MKesenheimer/fault-injection-library/docs/images/multiplexing/gnd-1.8-1000ns.bmp

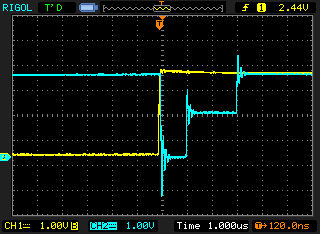
docs/images/multiplexing/gnd-1.8-1000ns.bmp
