MKesenheimer/fault-injection-library/docs/images/multiplexing/gnd-1.8.bmp

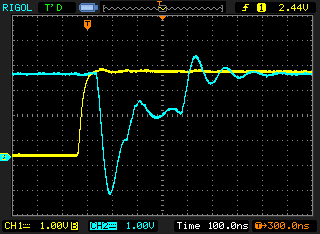
docs/images/multiplexing/gnd-1.8.bmp
