MKesenheimer/fault-injection-library/docs/images/multiplexing/gnd-3.3-gnd.bmp

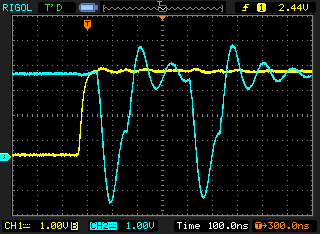
docs/images/multiplexing/gnd-3.3-gnd.bmp
