MKesenheimer/fault-injection-library/docs/images/pgfpv2.1.jpg

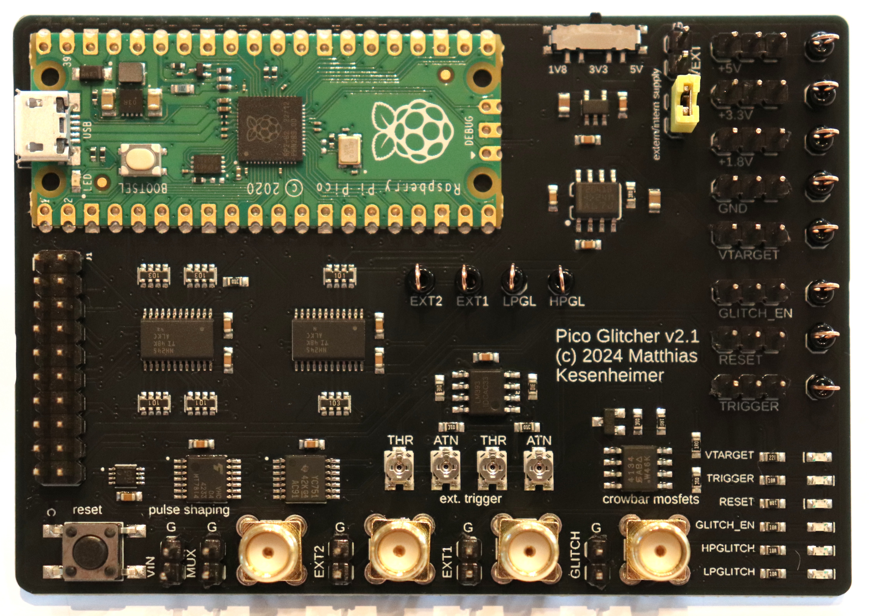
docs/images/pgfpv2.1.jpg
