MKesenheimer/fault-injection-library/docs/images/pinout.png

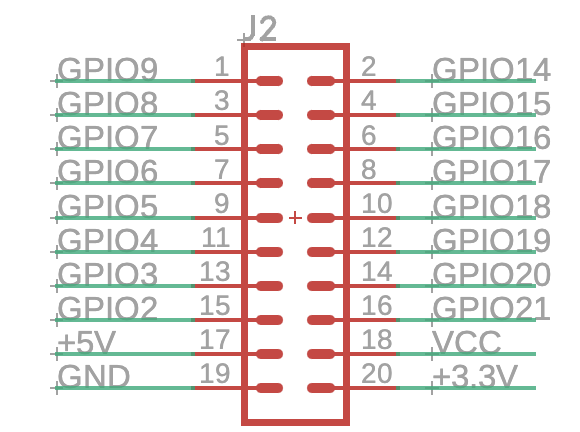
docs/images/pinout.png
