MKesenheimer/fault-injection-library/docs/images/pulse-shaping/4-100ns.bmp

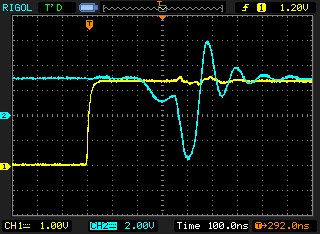
docs/images/pulse-shaping/4-100ns.bmp
