MKesenheimer/fault-injection-library/docs/images/pulse-shaping/4-1000ns.bmp

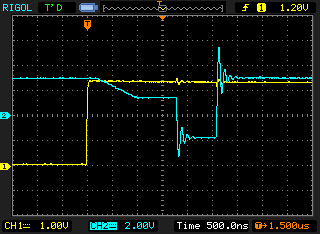
docs/images/pulse-shaping/4-1000ns.bmp
