MKesenheimer/fault-injection-library/docs/images/pulse-shaping/pchip-editor.bmp

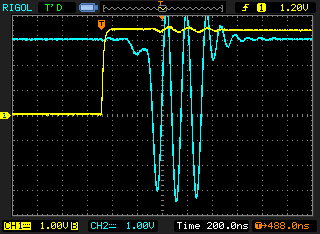
docs/images/pulse-shaping/pchip-editor.bmp
