MKesenheimer/fault-injection-library/docs/images/pulse-shaping/pchip-editor.png

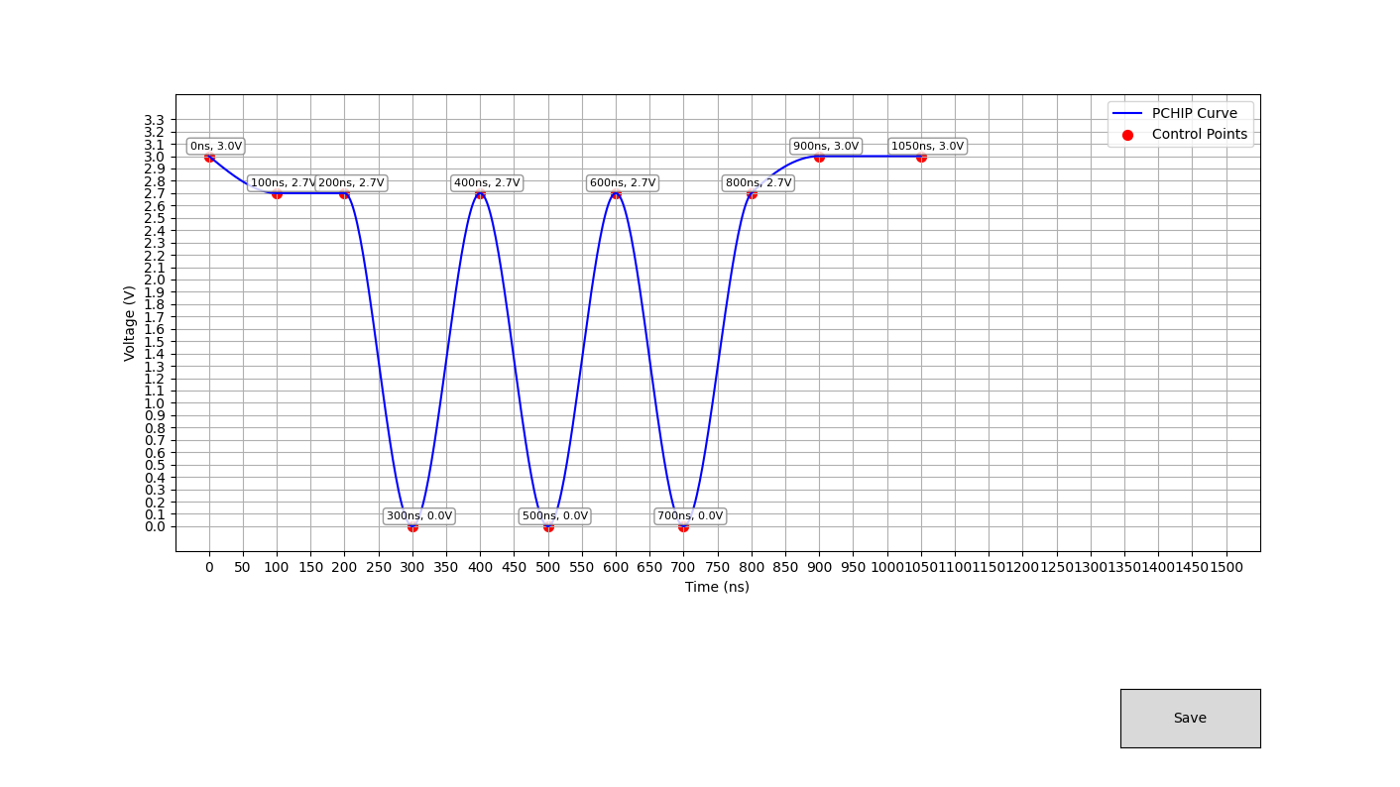
docs/images/pulse-shaping/pchip-editor.png
