MKesenheimer/fault-injection-library/docs/images/pulse-shaping/ps-100n-2.bmp

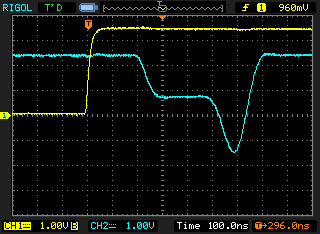
docs/images/pulse-shaping/ps-100n-2.bmp
