MKesenheimer/fault-injection-library/docs/images/pulse-shaping/ps-200n-2.bmp

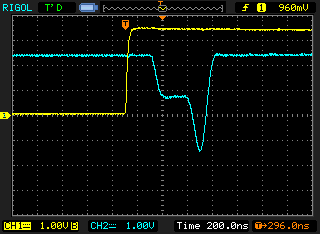
docs/images/pulse-shaping/ps-200n-2.bmp
