MKesenheimer/fault-injection-library/docs/images/stm8s/multiplexing-success.png

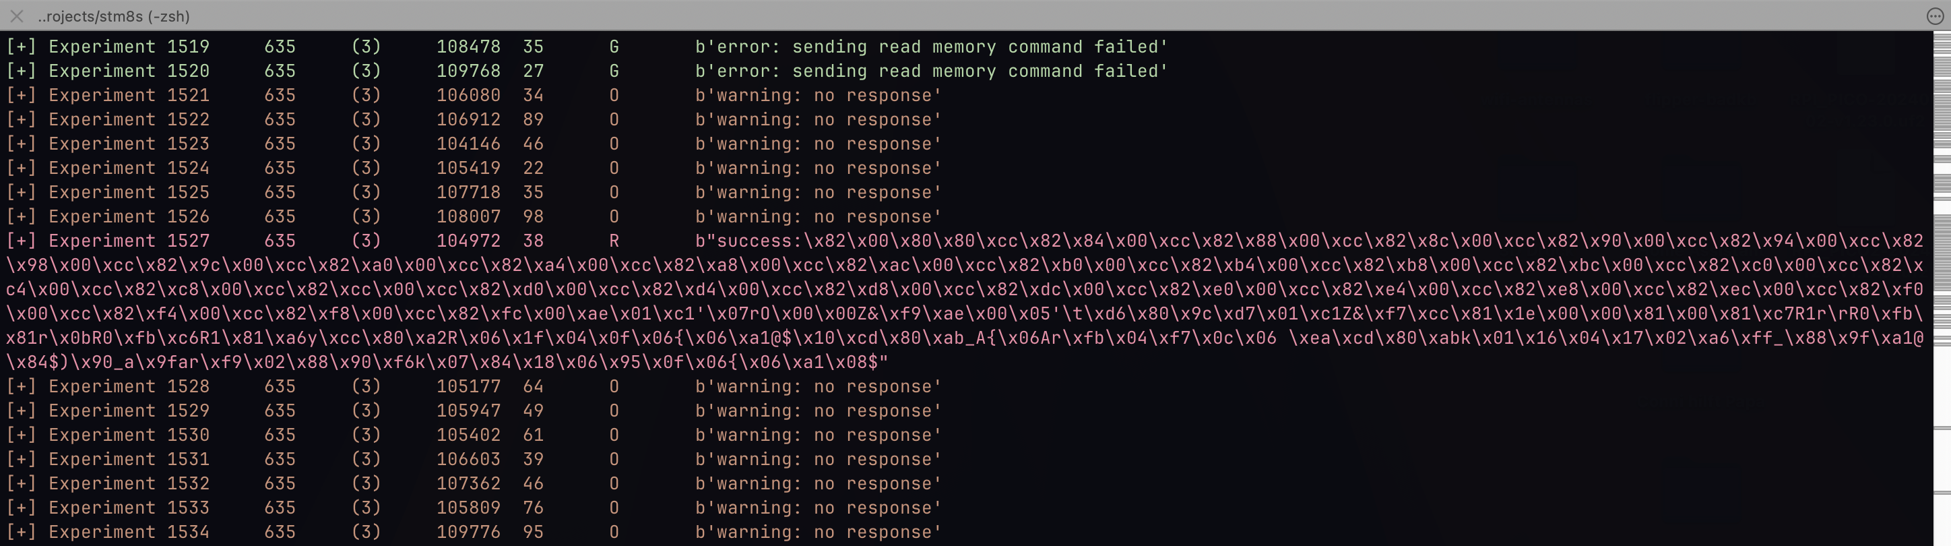
docs/images/stm8s/multiplexing-success.png
