MKesenheimer/fault-injection-library/projects/esp32v1.3/images/esp32-glitching.png

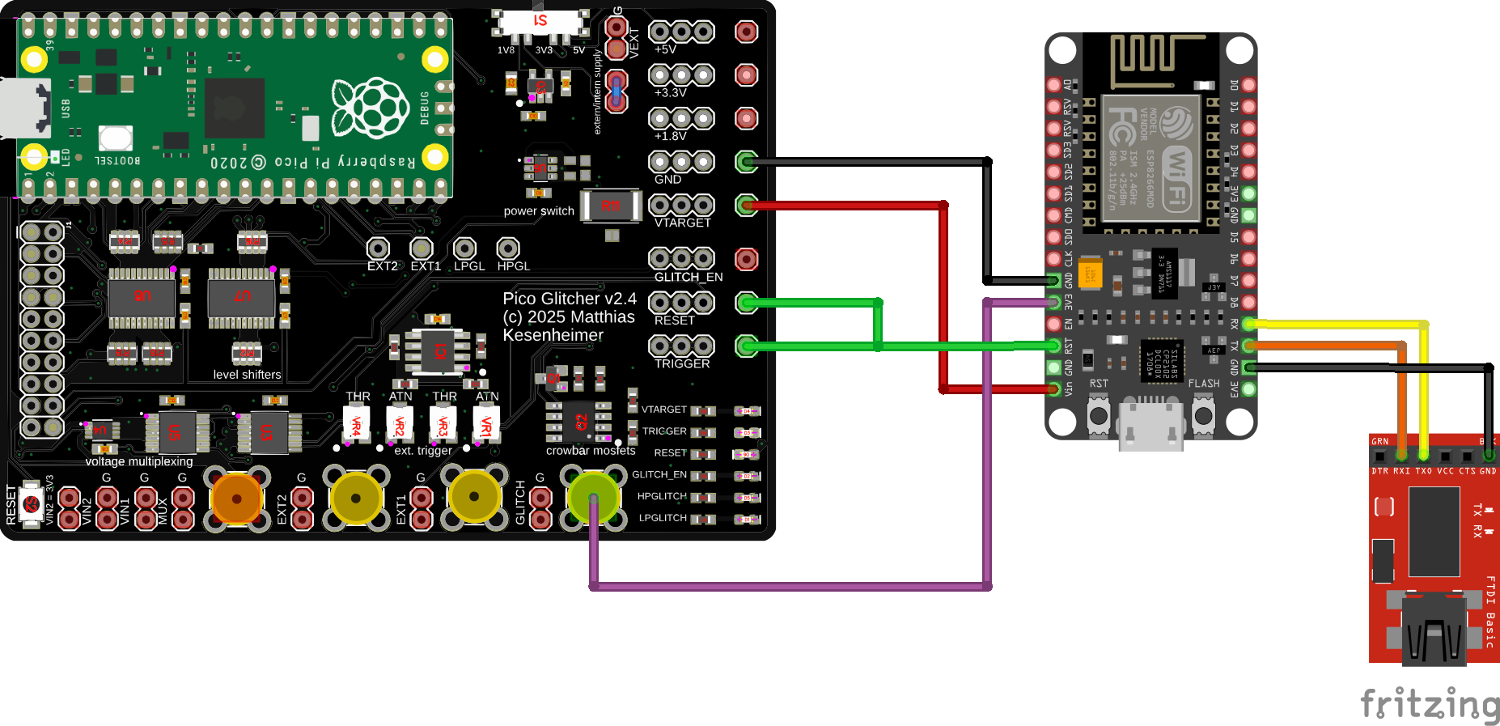
projects/esp32v1.3/images/esp32-glitching.png
