MKesenheimer/fault-injection-library/projects/esp32v1.3/images/multiplexing-t1_500ns-v1_1.8V-t2_variable-v2_GND.png

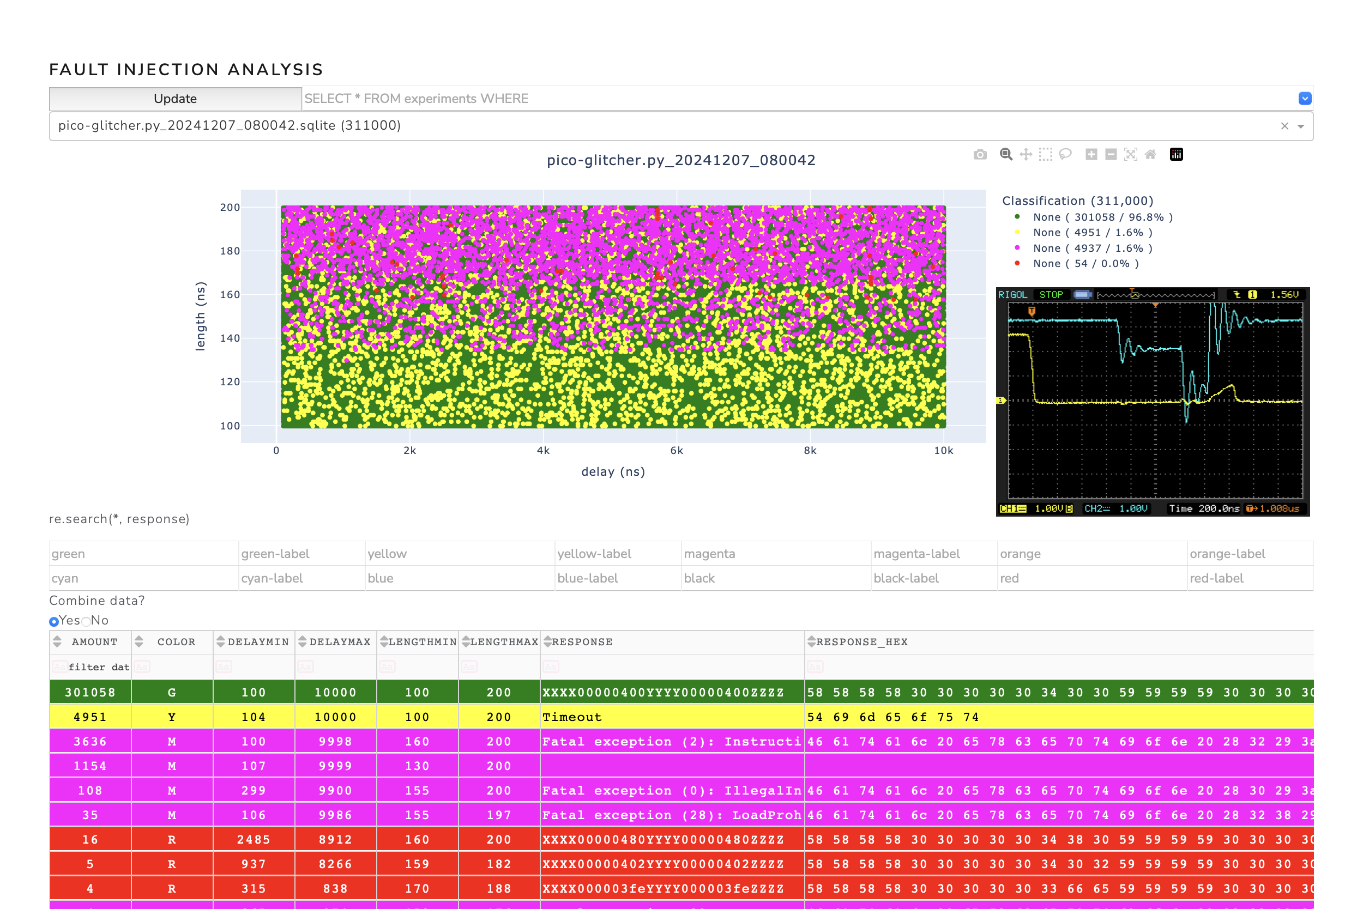
projects/esp32v1.3/images/multiplexing-t1_500ns-v1_1.8V-t2_variable-v2_GND.png
