MKesenheimer/fault-injection-library/projects/esp32v1.3/images/multiplexing-t1_1000ns-v1_1.8V-t2_variable-v2_GND-2.bmp

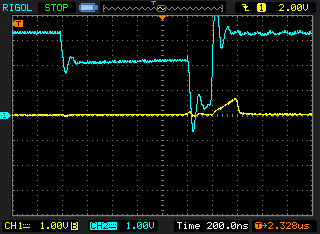
projects/esp32v1.3/images/multiplexing-t1_1000ns-v1_1.8V-t2_variable-v2_GND-2.bmp
