MKesenheimer/fault-injection-library/projects/esp32v1.3/images/multiplexing-t1_variable-v1_1.8V-t2_175ns-v2_GND.bmp

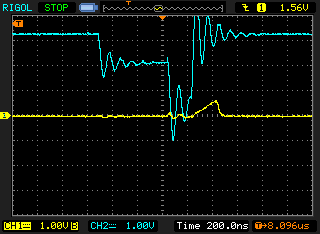
projects/esp32v1.3/images/multiplexing-t1_variable-v1_1.8V-t2_175ns-v2_GND.bmp
