MKesenheimer/fault-injection-library/projects/nrf52832/images/airtag/command-line-pro-glitcher.png

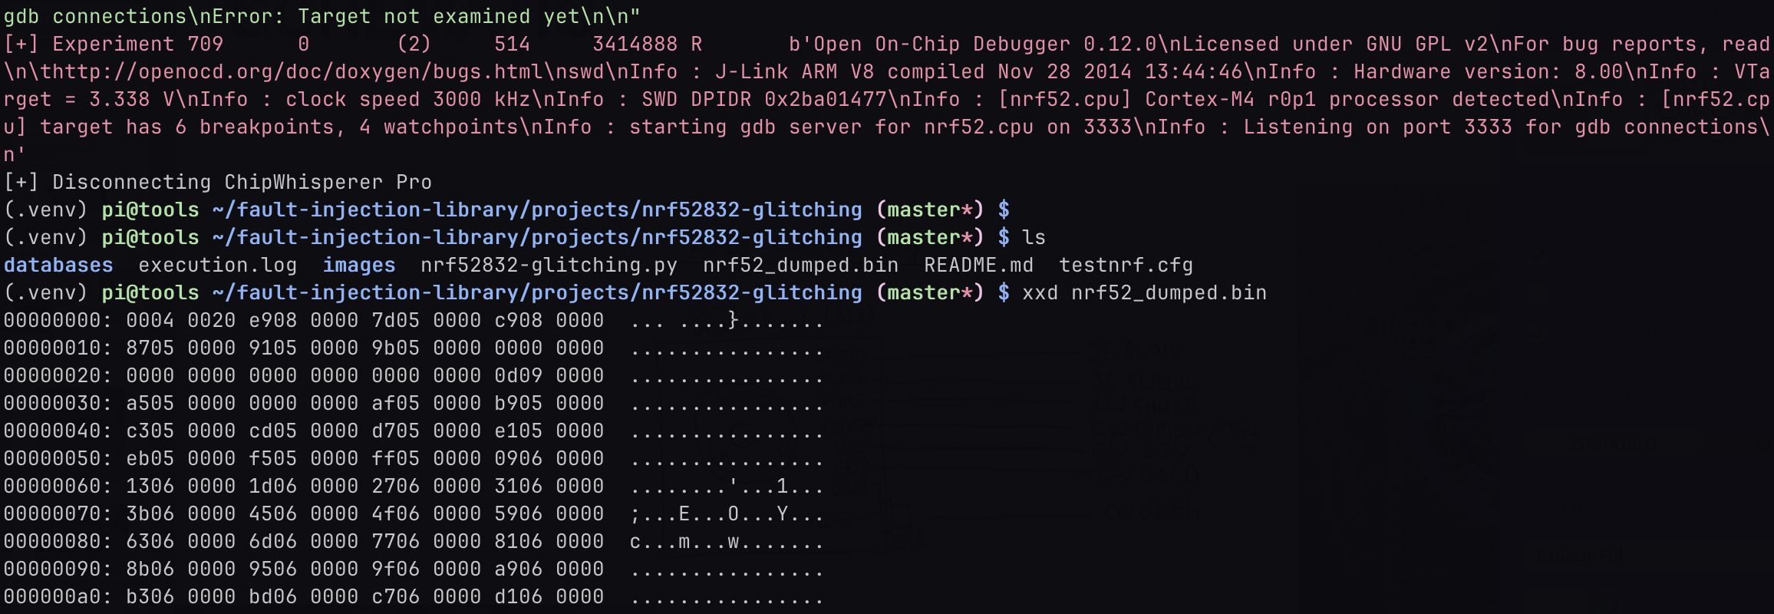
projects/nrf52832/images/airtag/command-line-pro-glitcher.png
