MKesenheimer/fault-injection-library/projects/nrf52832/images/airtag/glitch-2.png

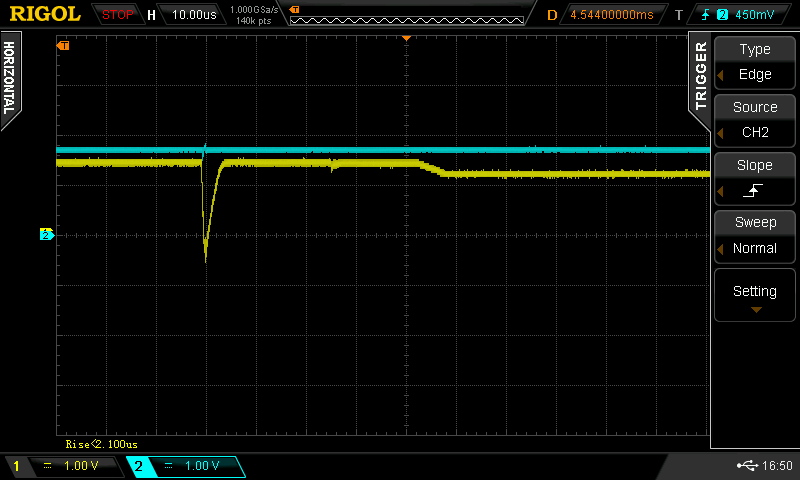
projects/nrf52832/images/airtag/glitch-2.png
