MKesenheimer/fault-injection-library/projects/nrf52832/images/airtag/parameterspace-pro-glitcher.png

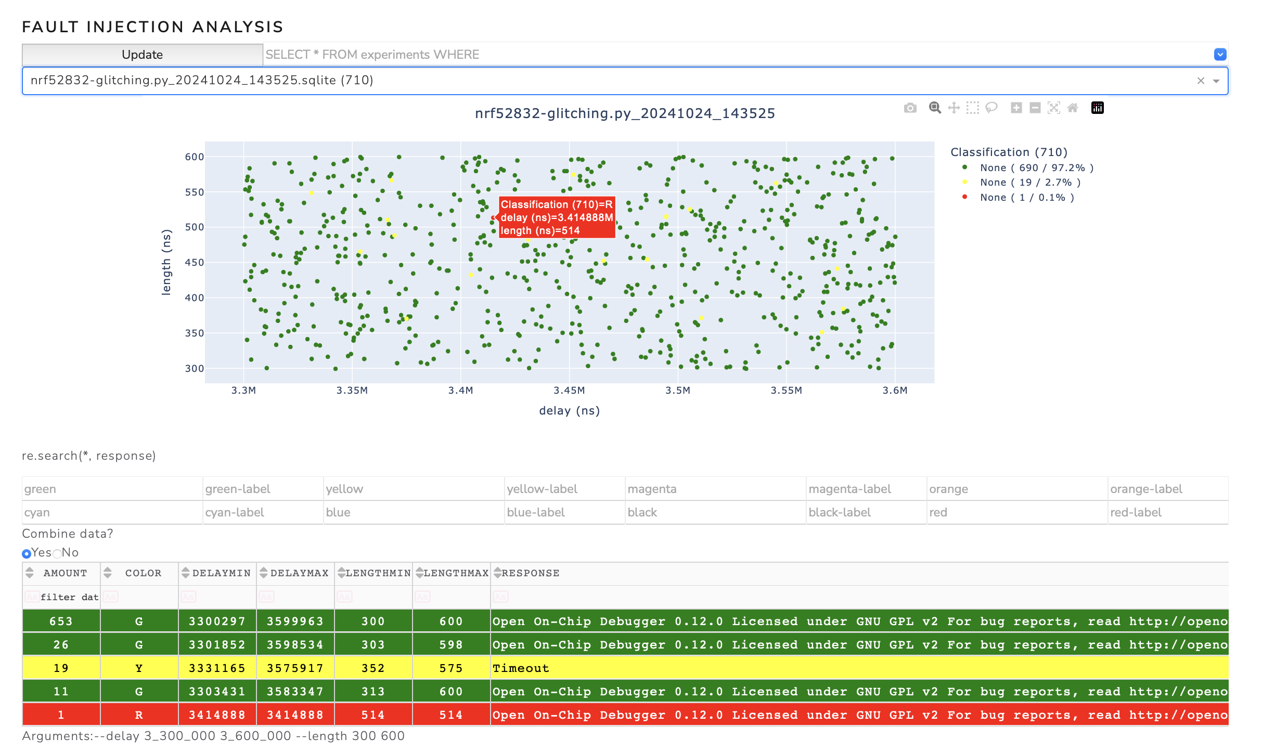
projects/nrf52832/images/airtag/parameterspace-pro-glitcher.png
