MKesenheimer/fault-injection-library/projects/nrf52832/images/airtag/voltage-trace-zoomed.png

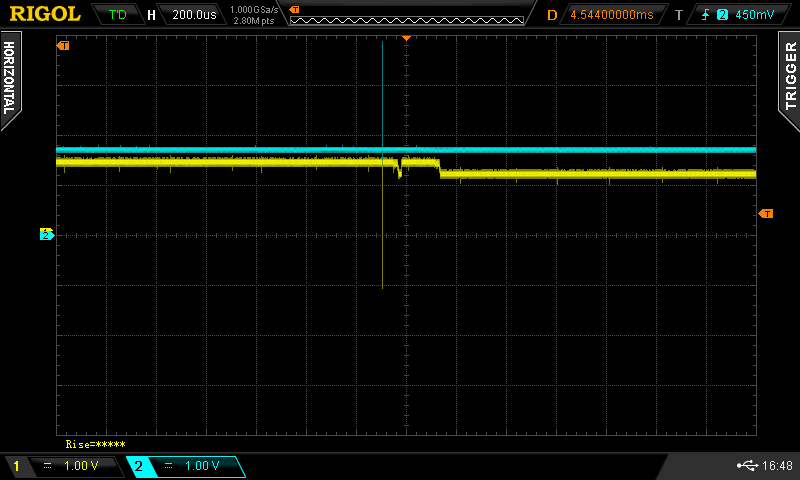
projects/nrf52832/images/airtag/voltage-trace-zoomed.png
