MKesenheimer/fault-injection-library/projects/nrf52832/images/keyboard/campaign-1.png

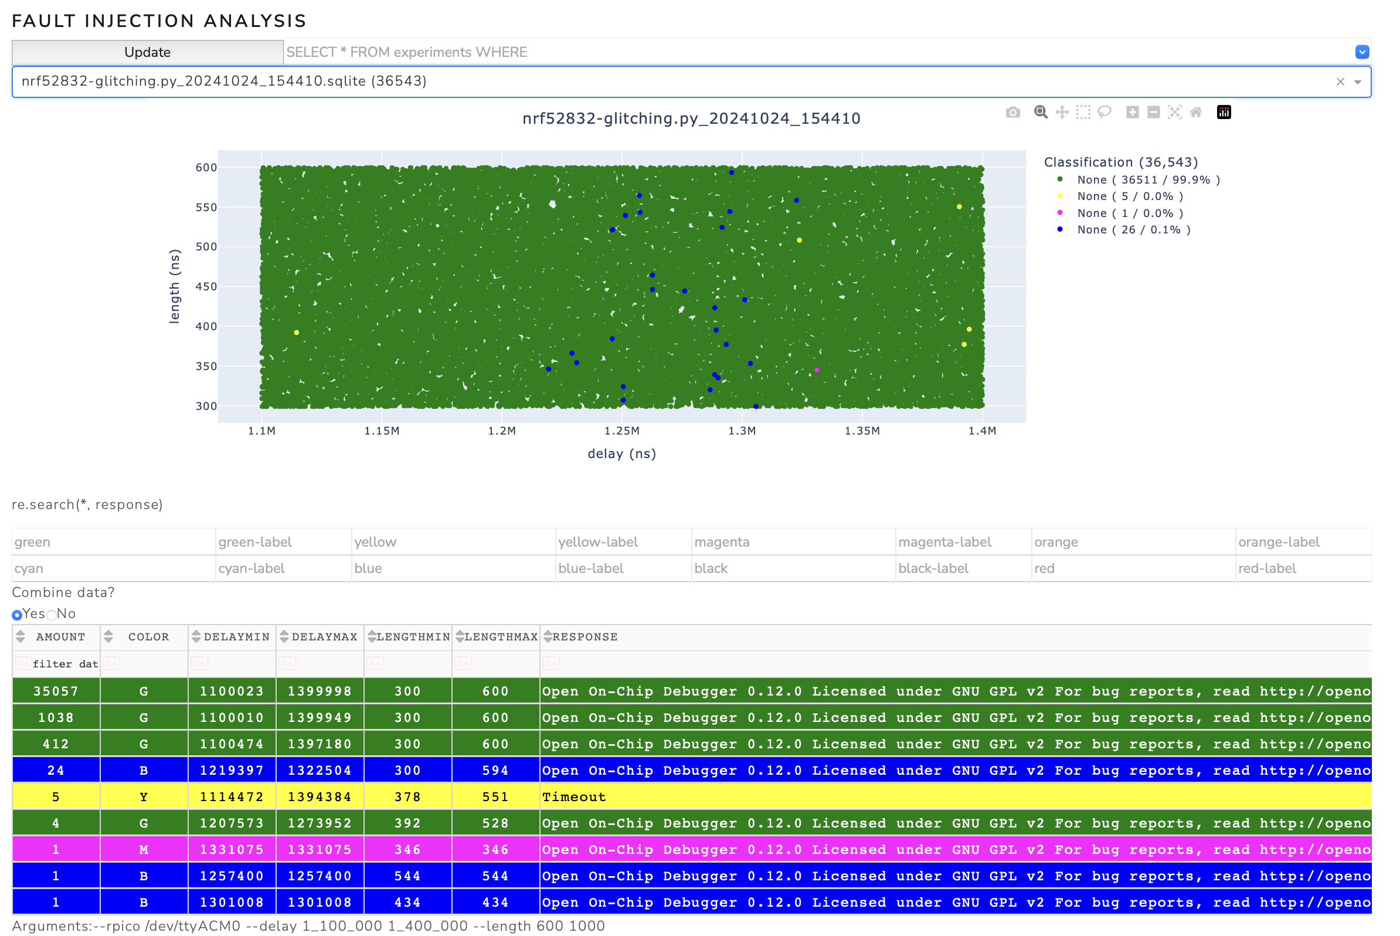
projects/nrf52832/images/keyboard/campaign-1.png
