MKesenheimer/fault-injection-library/projects/nrf52832/images/keyboard/campaign-2.png

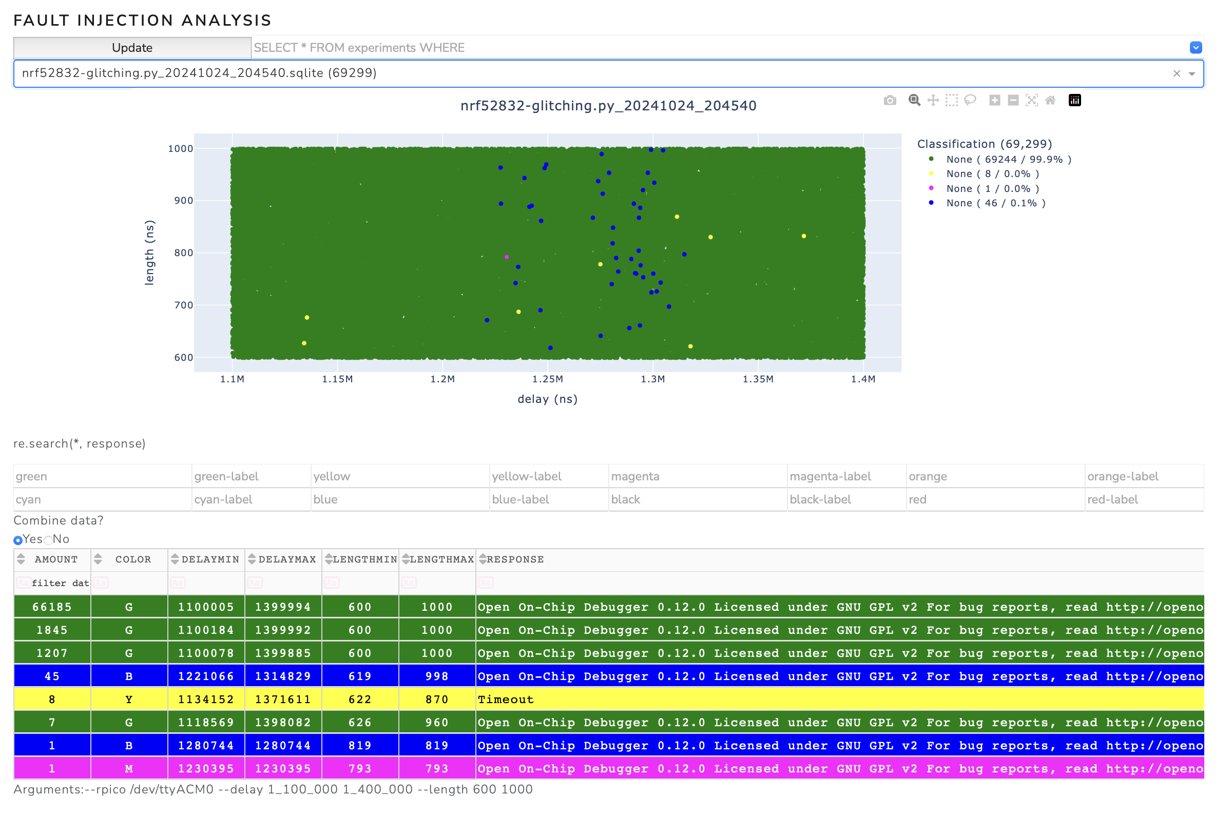
projects/nrf52832/images/keyboard/campaign-2.png
