MKesenheimer/fault-injection-library/projects/nrf52832/images/keyboard/glitch-zoomed.png

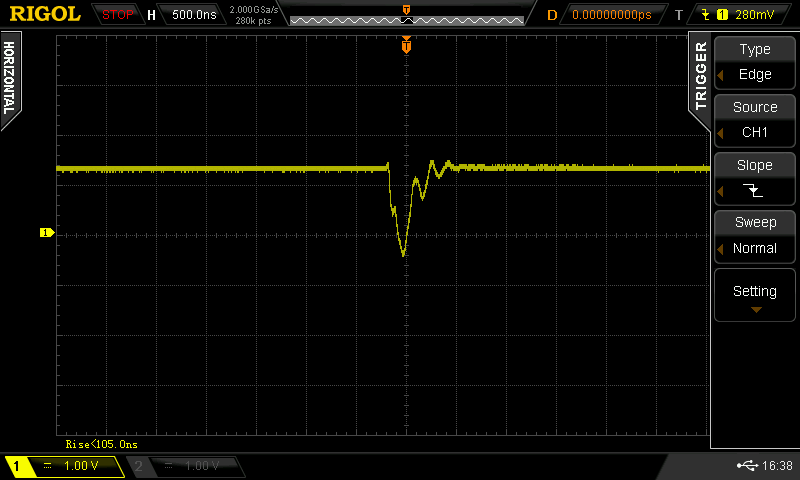
projects/nrf52832/images/keyboard/glitch-zoomed.png
