MKesenheimer/fault-injection-library/projects/nrf52832/images/keyboard/glitch.png

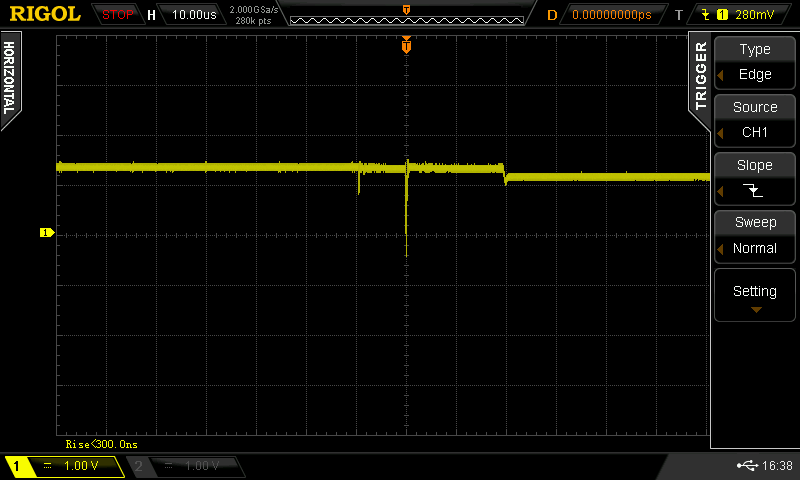
projects/nrf52832/images/keyboard/glitch.png
