MKesenheimer/fault-injection-library/projects/nrf52832/images/keyboard/gpio15_signal.png

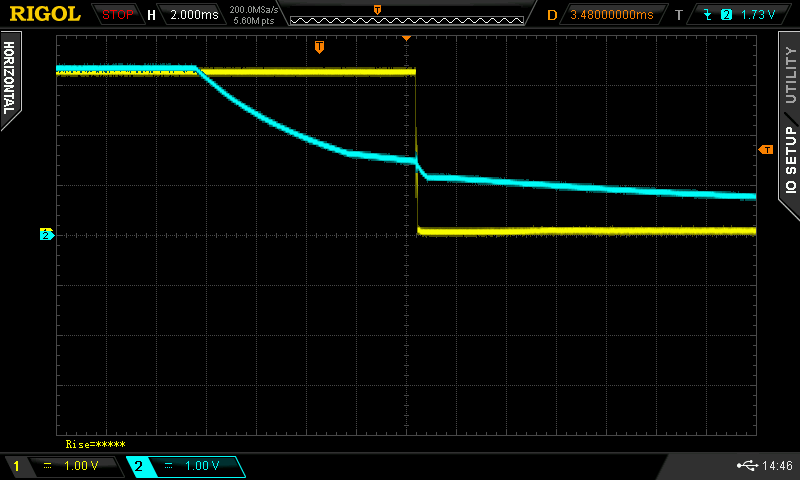
projects/nrf52832/images/keyboard/gpio15_signal.png
