MKesenheimer/fault-injection-library/projects/nrf52832/images/keyboard/gpio15_signal_zoomed.png

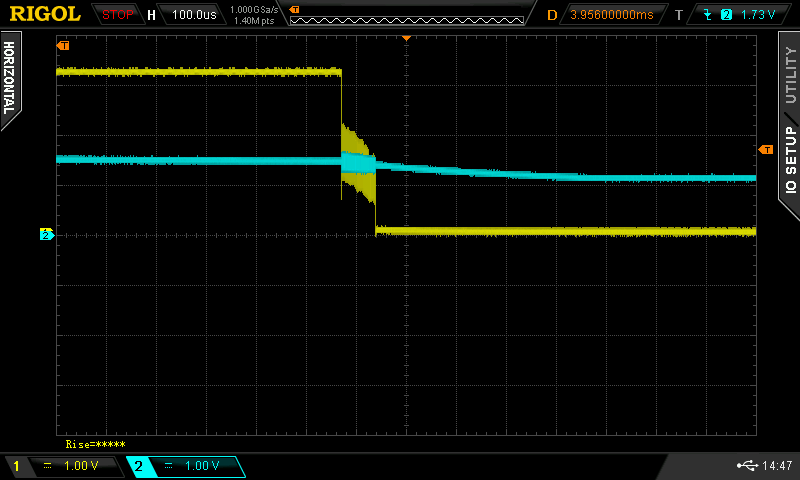
projects/nrf52832/images/keyboard/gpio15_signal_zoomed.png
