MKesenheimer/fault-injection-library/projects/nrf52832/images/keyboard/power-curve.png

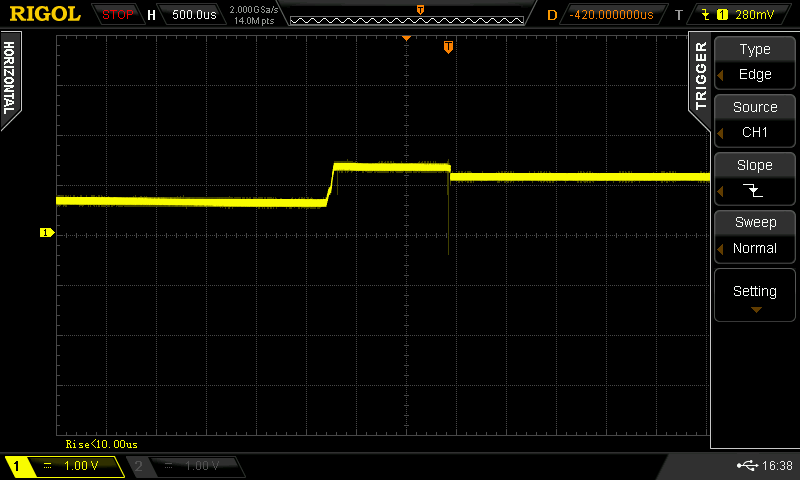
projects/nrf52832/images/keyboard/power-curve.png
