MKesenheimer/fault-injection-library/projects/rp2040/images/no-glitch.png

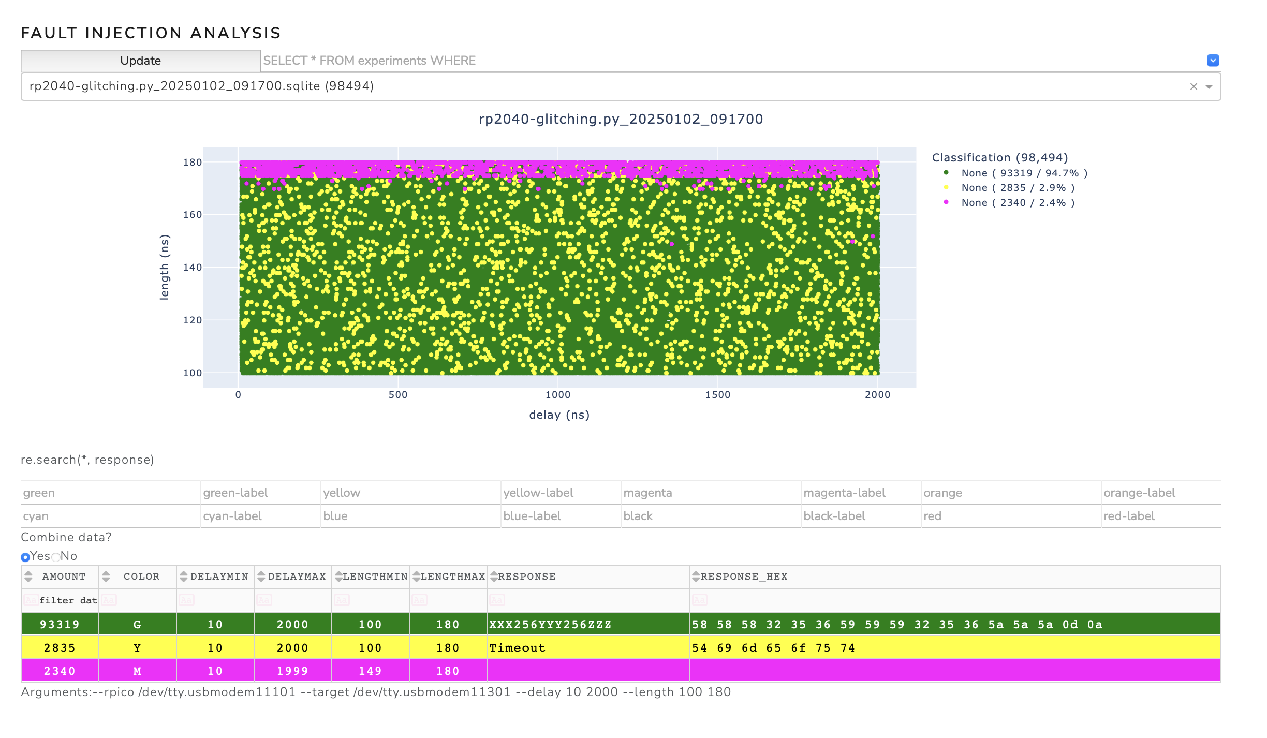
projects/rp2040/images/no-glitch.png
