MKesenheimer/fault-injection-library/projects/rp2040/rpi-program/raspberry-pi-pico-gpio.png

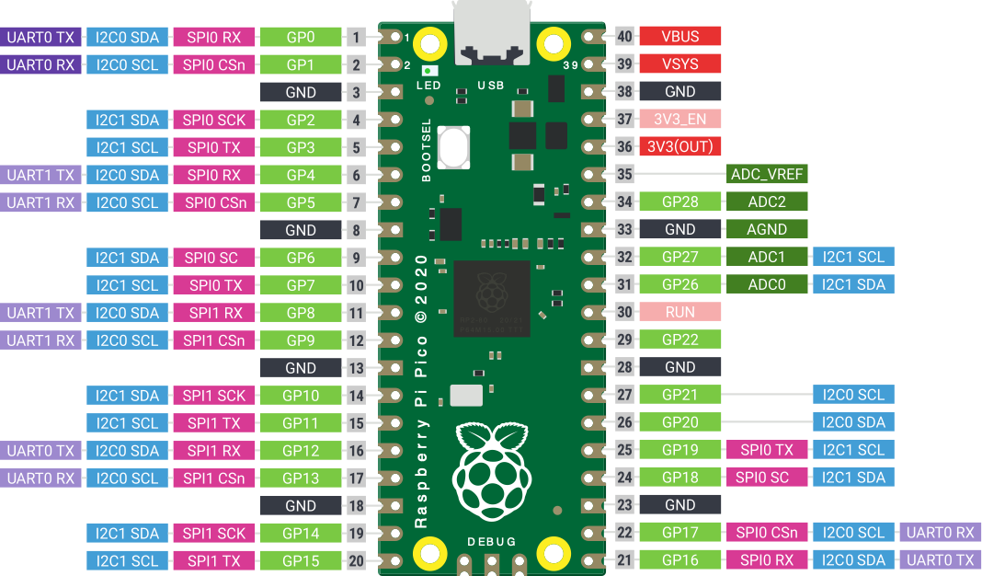
projects/rp2040/rpi-program/raspberry-pi-pico-gpio.png
