MKesenheimer/fault-injection-library/projects/rp2350/images/current-trace.bmp

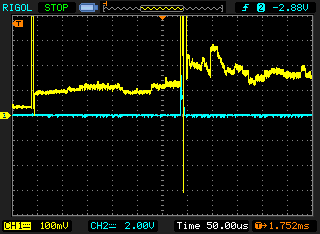
projects/rp2350/images/current-trace.bmp
