MKesenheimer/fault-injection-library/projects/rp2350/images/glitch1.bmp

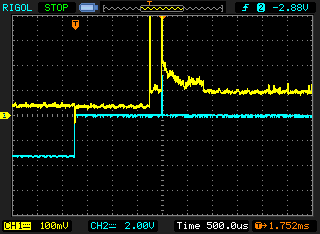
projects/rp2350/images/glitch1.bmp
