MKesenheimer/fault-injection-library/projects/rp2350/images/glitch2.bmp

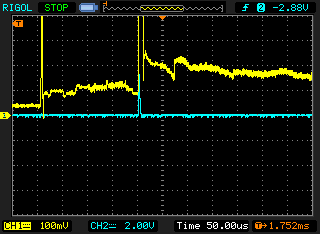
projects/rp2350/images/glitch2.bmp
