MKesenheimer/fault-injection-library/projects/rp2350/images/glitch3.bmp

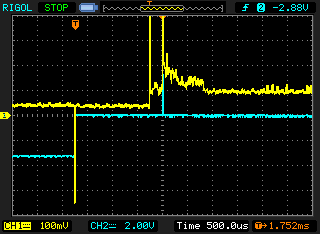
projects/rp2350/images/glitch3.bmp
