MKesenheimer/fault-injection-library/projects/rp2350/images/overall.JPG

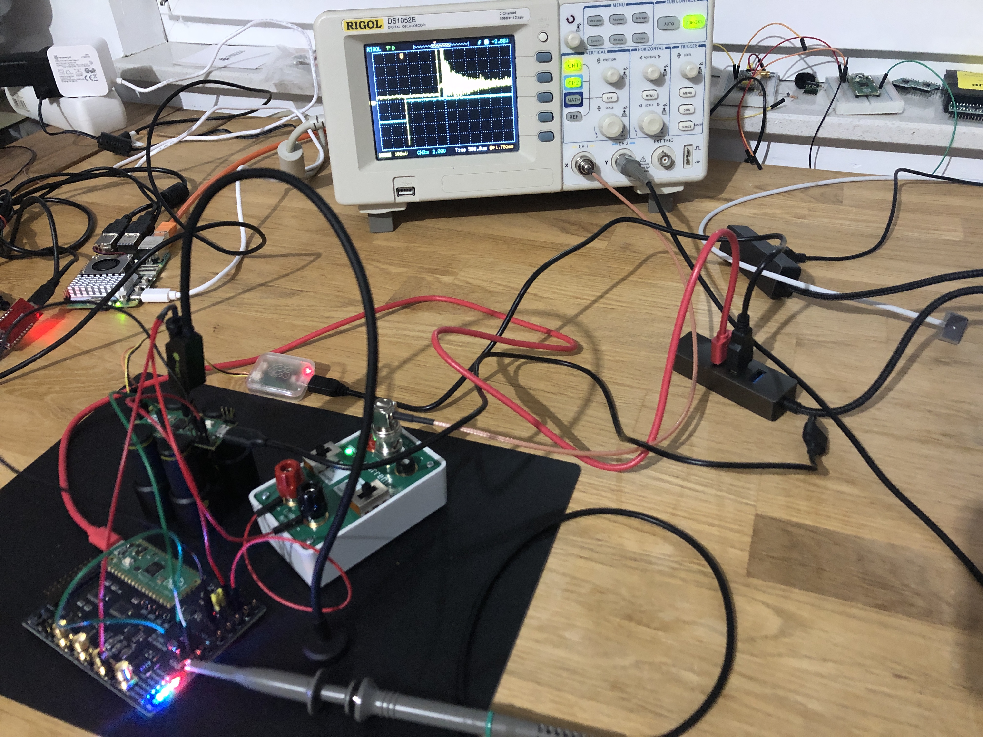
projects/rp2350/images/overall.JPG
