MKesenheimer/fault-injection-library/projects/rp2350/images/parameterspace1.png

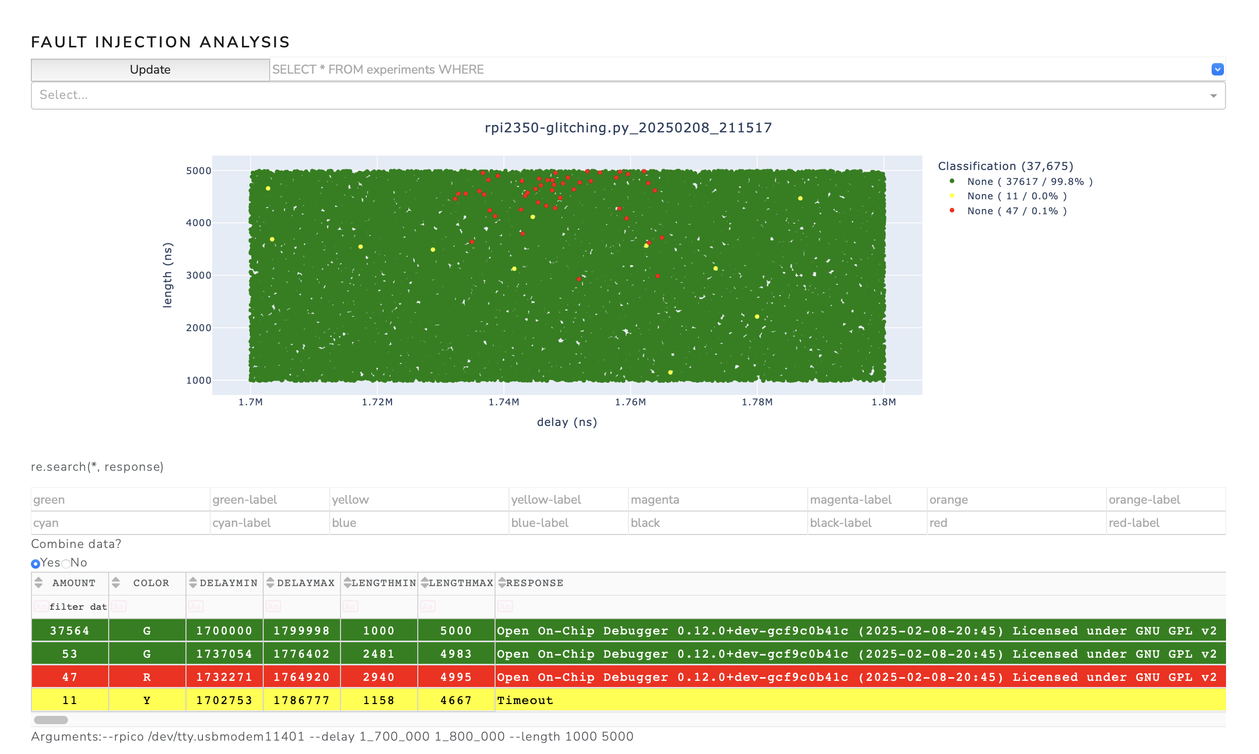
projects/rp2350/images/parameterspace1.png
