MKesenheimer/fault-injection-library/projects/rp2350/images/parameterspace2.png

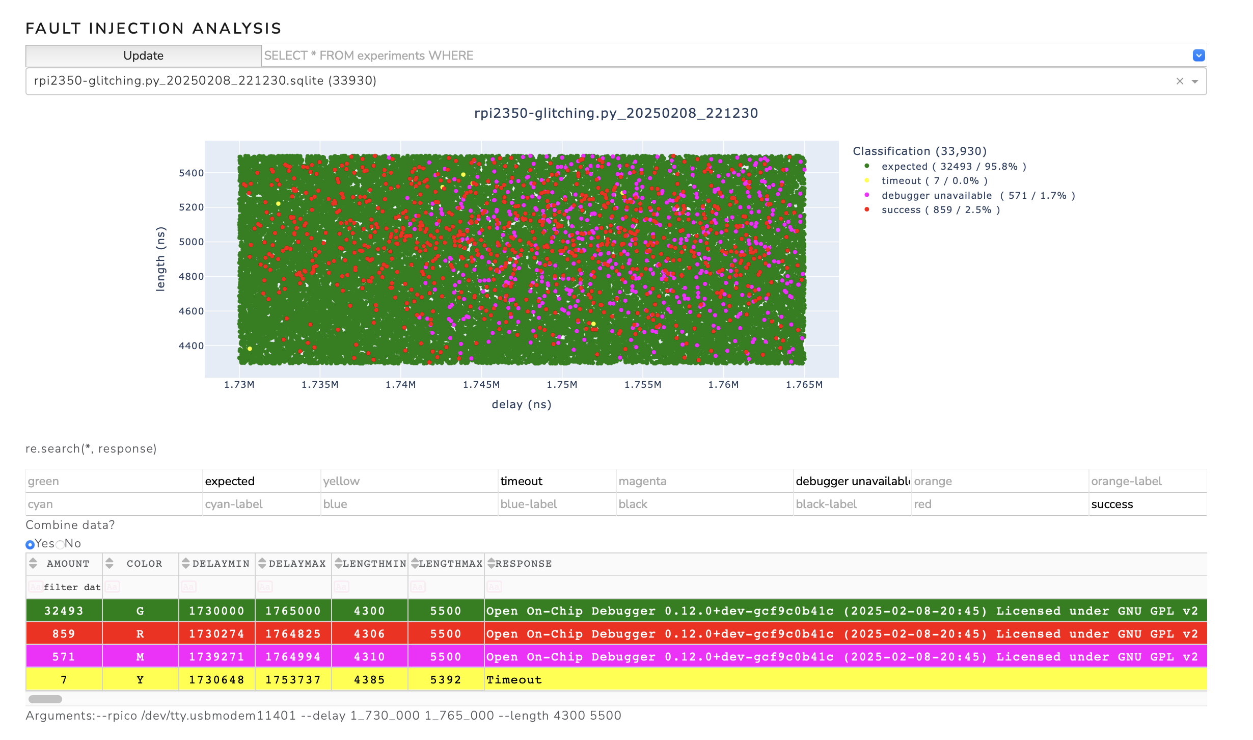
projects/rp2350/images/parameterspace2.png
