MKesenheimer/fault-injection-library/projects/rp2350/images/rp2350-glitching.png

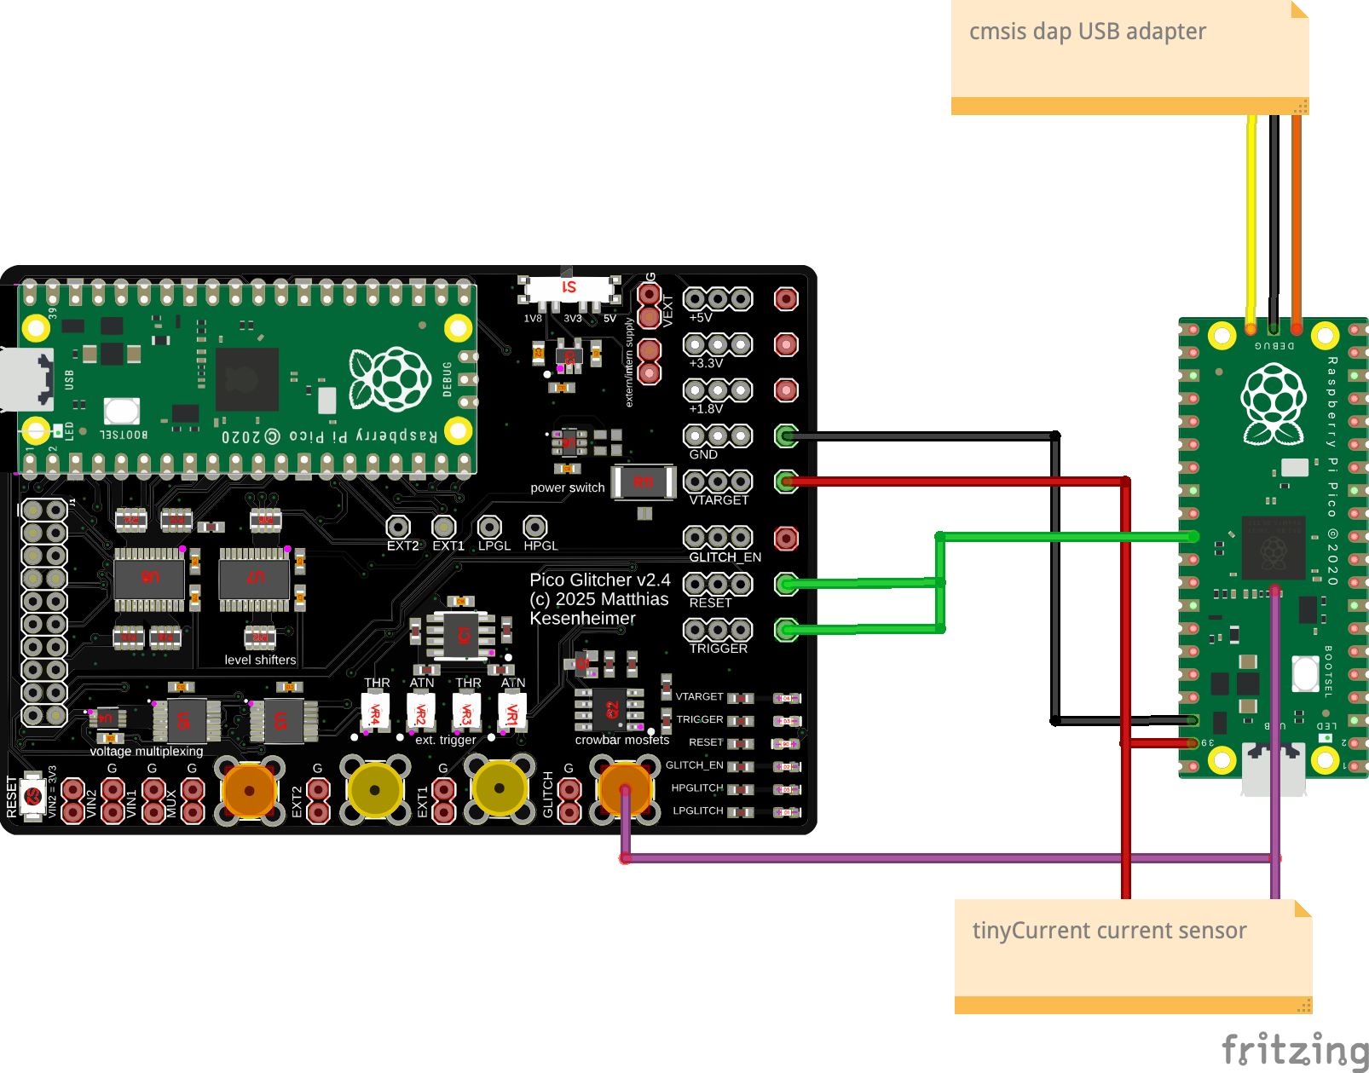
projects/rp2350/images/rp2350-glitching.png
