MKesenheimer/fault-injection-library/projects/rp2350/images/success.png

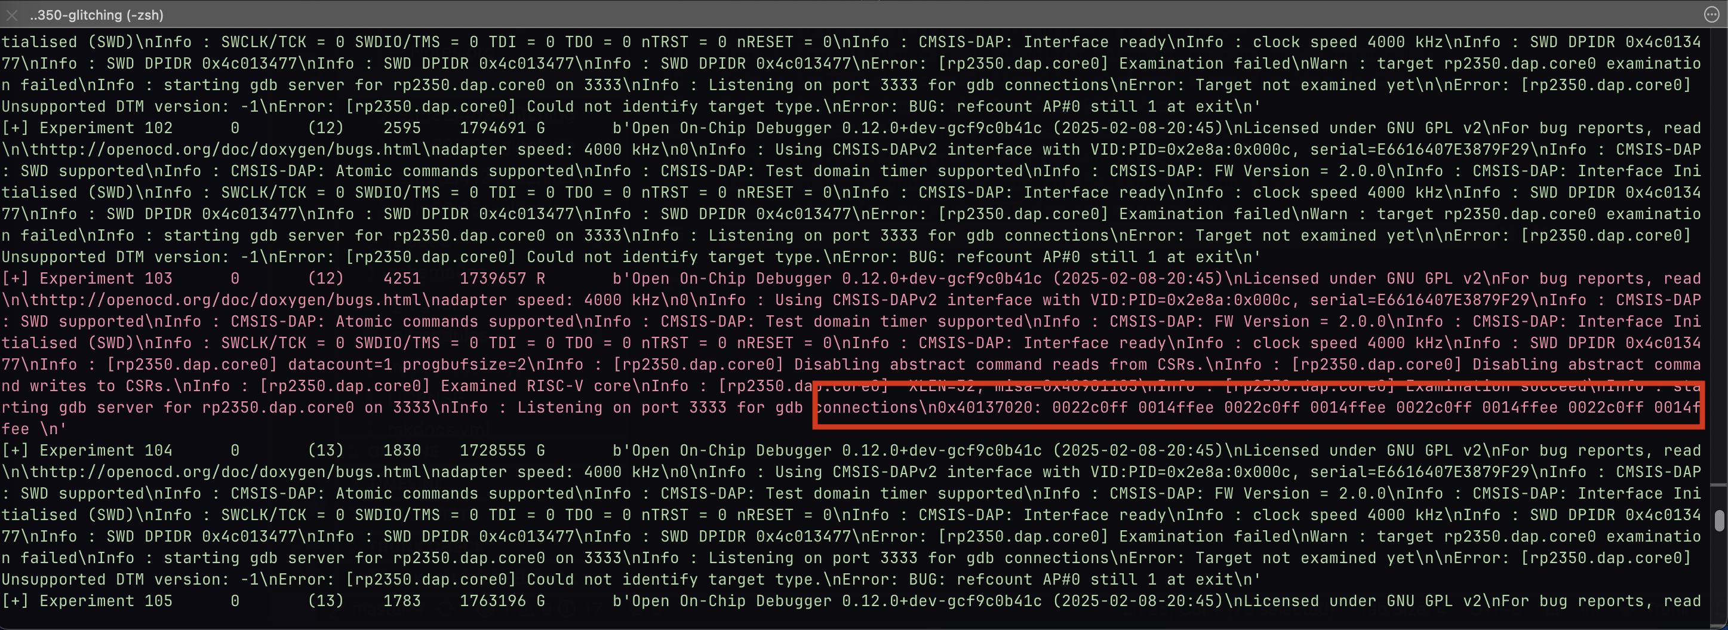
projects/rp2350/images/success.png
