MKesenheimer/fault-injection-library/projects/stm8s/images/bootloader-communication-1.png

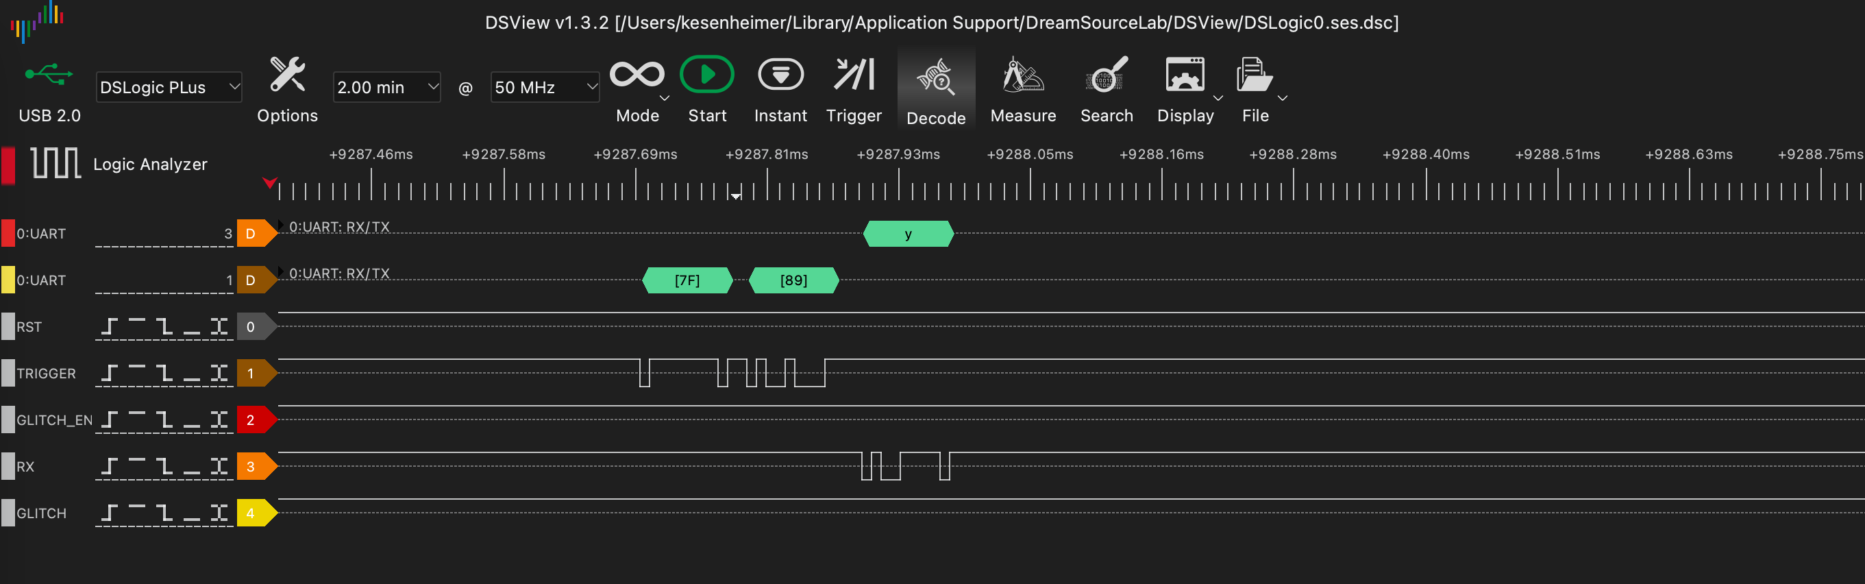
projects/stm8s/images/bootloader-communication-1.png
