MKesenheimer/fault-injection-library/projects/stm8s/images/bootloader-communication-2.png

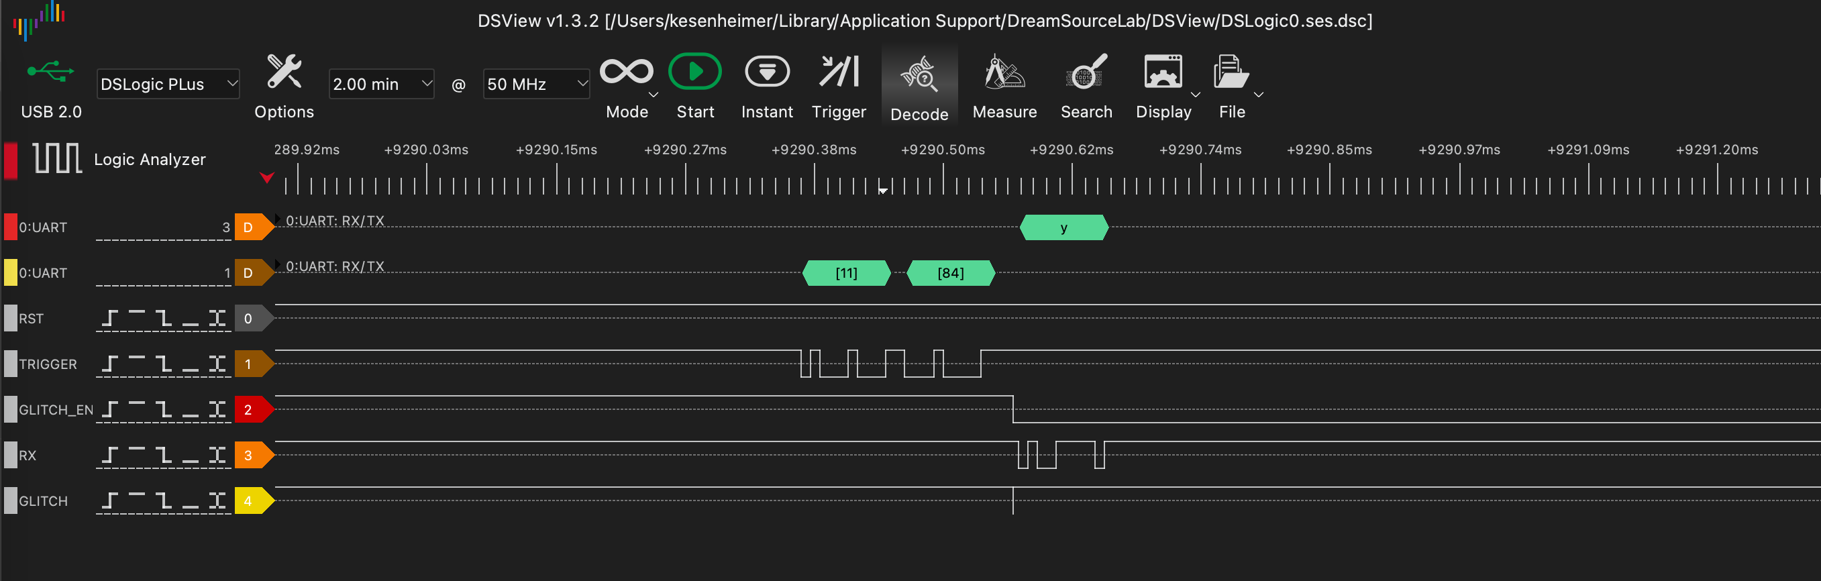
projects/stm8s/images/bootloader-communication-2.png
