MKesenheimer/fault-injection-library/projects/stm8s/images/bootloader-communication-3.png

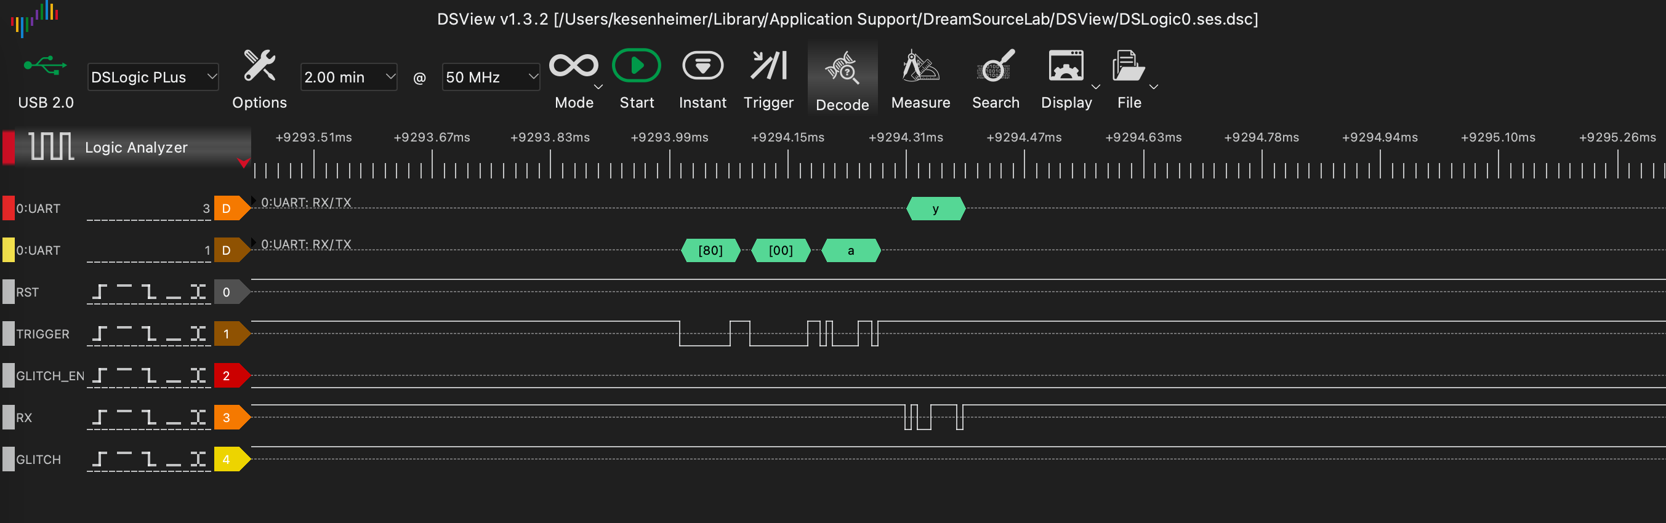
projects/stm8s/images/bootloader-communication-3.png
