MKesenheimer/fault-injection-library/projects/stm8s/images/bootloader-communication-4.png

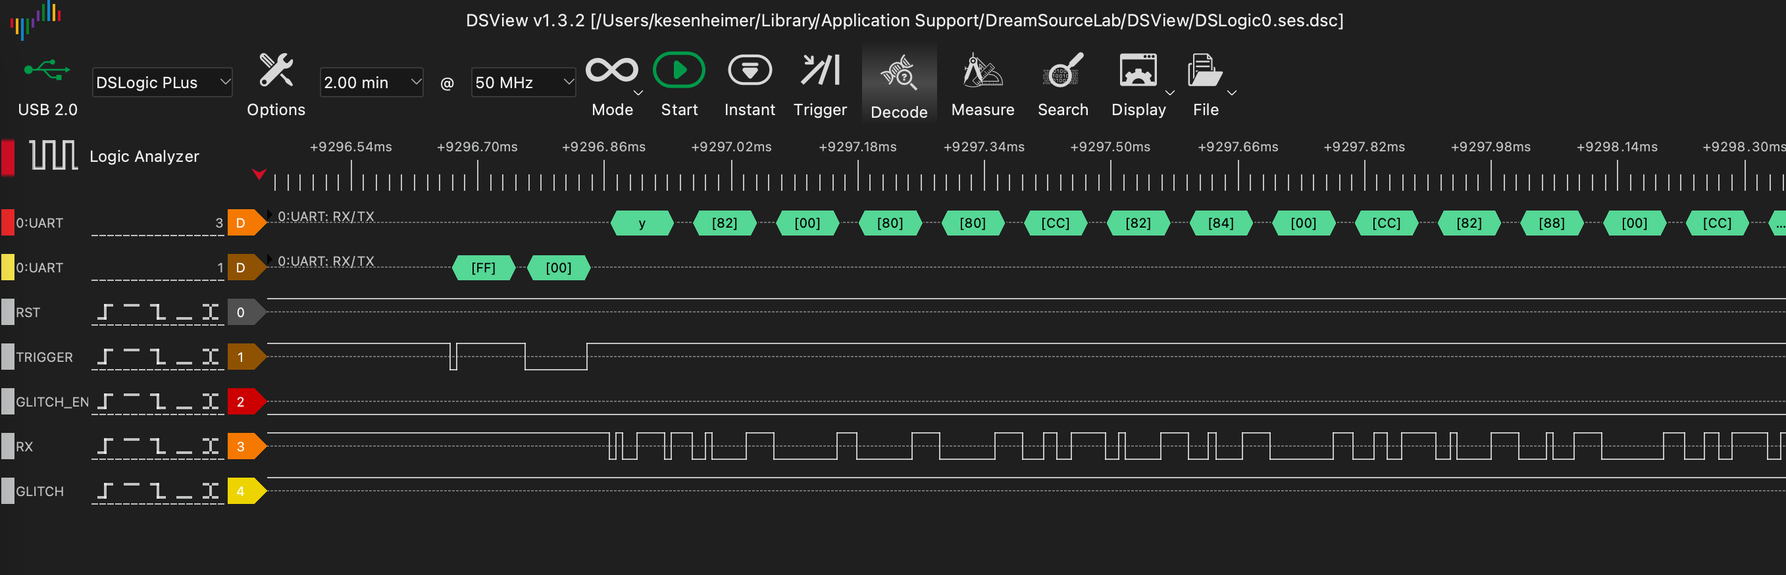
projects/stm8s/images/bootloader-communication-4.png
