MKesenheimer/fault-injection-library/projects/stm8s/images/bootloader-communication.png

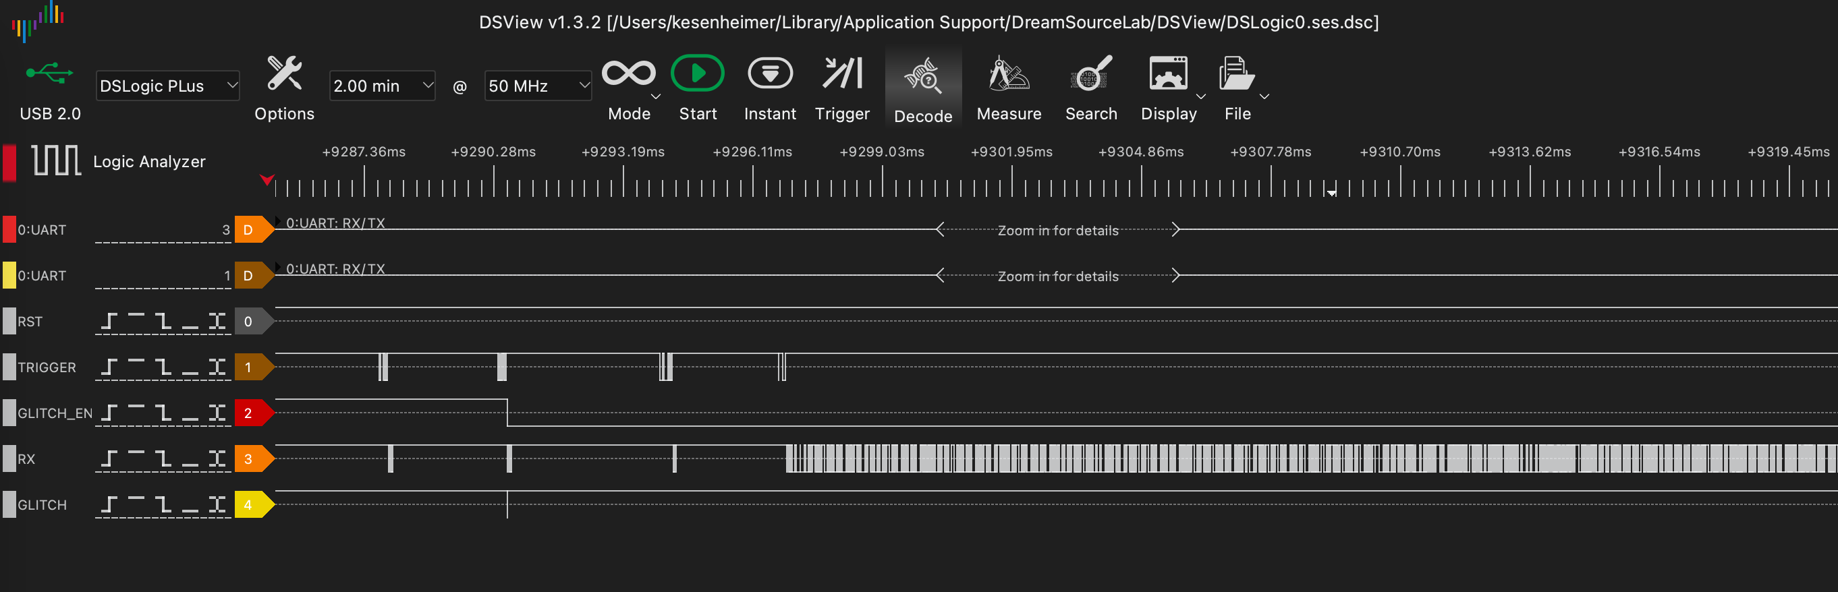
projects/stm8s/images/bootloader-communication.png
