MKesenheimer/fault-injection-library/projects/stm8s/images/success-scaled.png

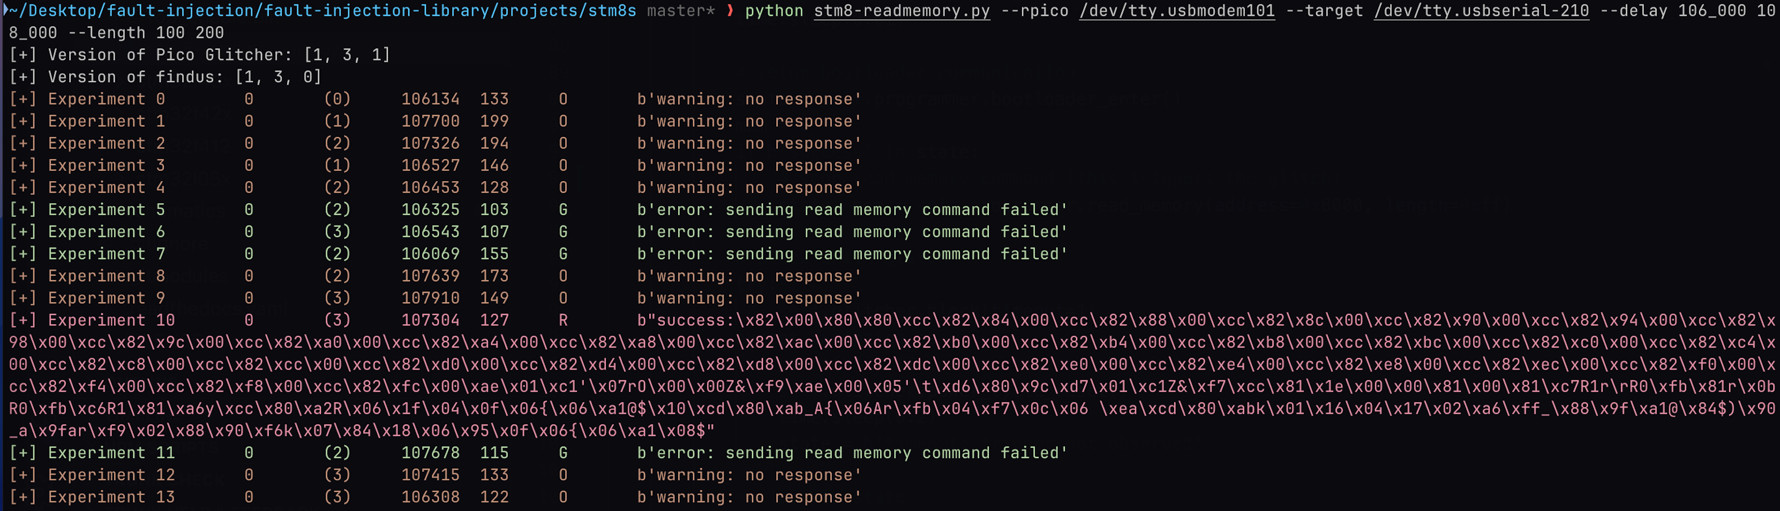
projects/stm8s/images/success-scaled.png
