MKesenheimer/fault-injection-library/projects/stm32f40x/images/Black_pill_pinout.png

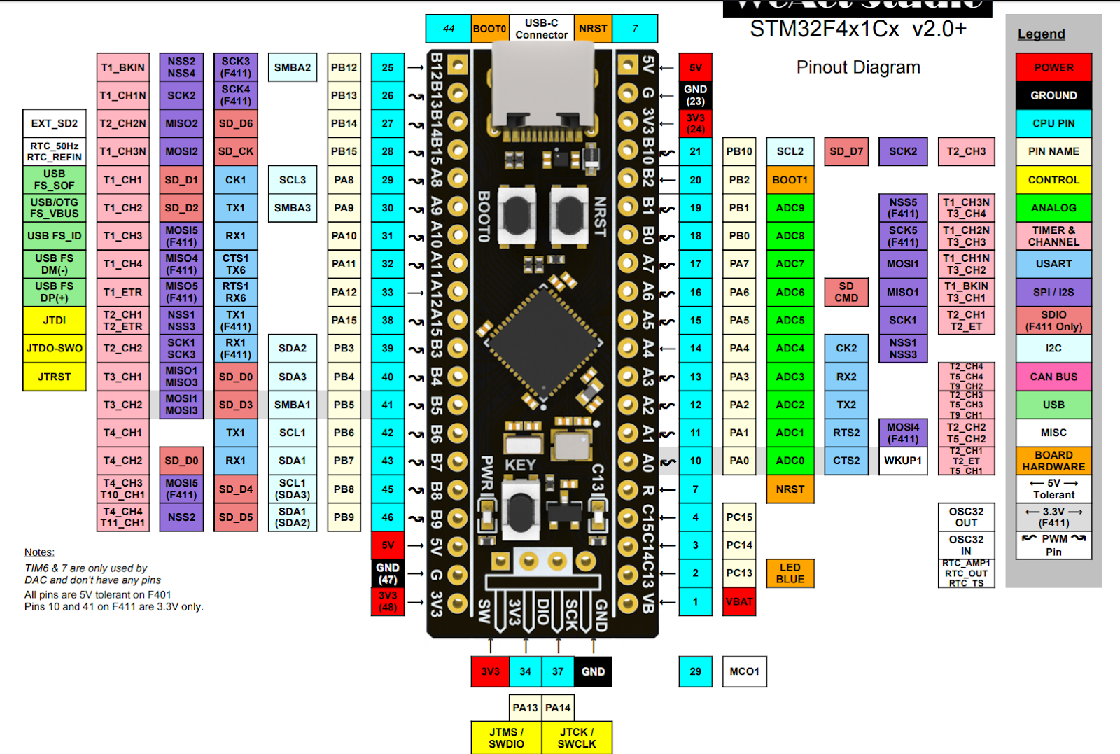
projects/stm32f40x/images/Black_pill_pinout.png
