MKesenheimer/fault-injection-library/projects/stm32f40x/images/power_supply_scheme.png

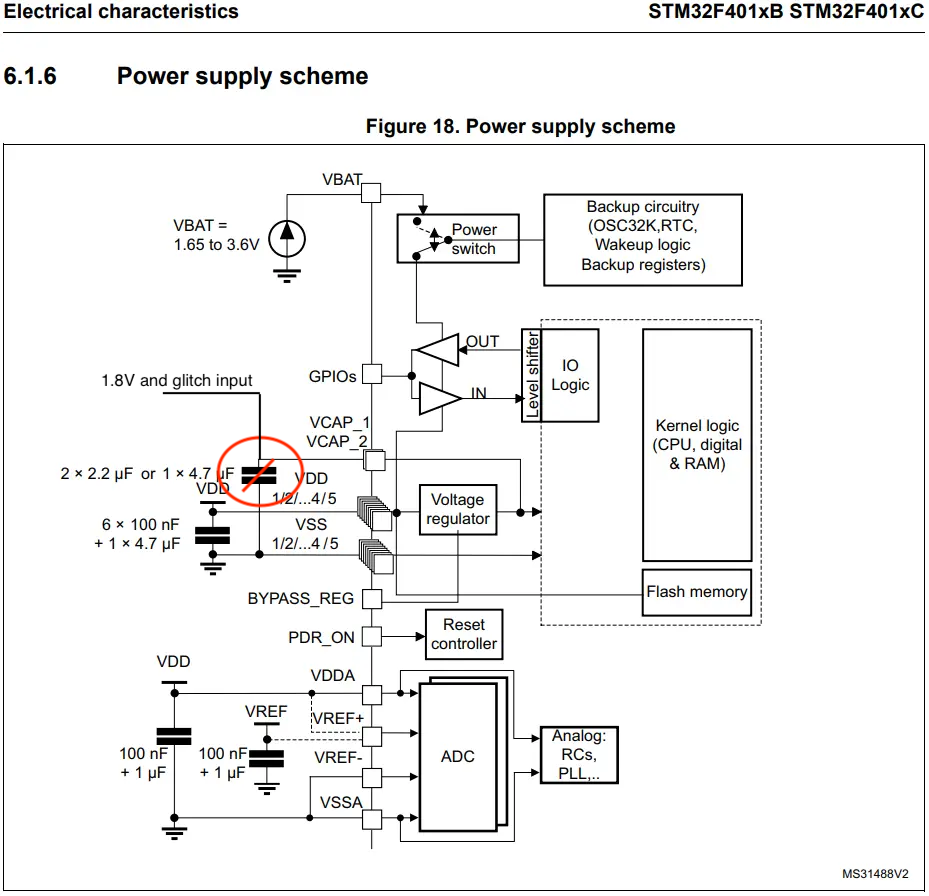
projects/stm32f40x/images/power_supply_scheme.png
