MKesenheimer/fault-injection-library/projects/stm32f40x/images/programmed_flash.png

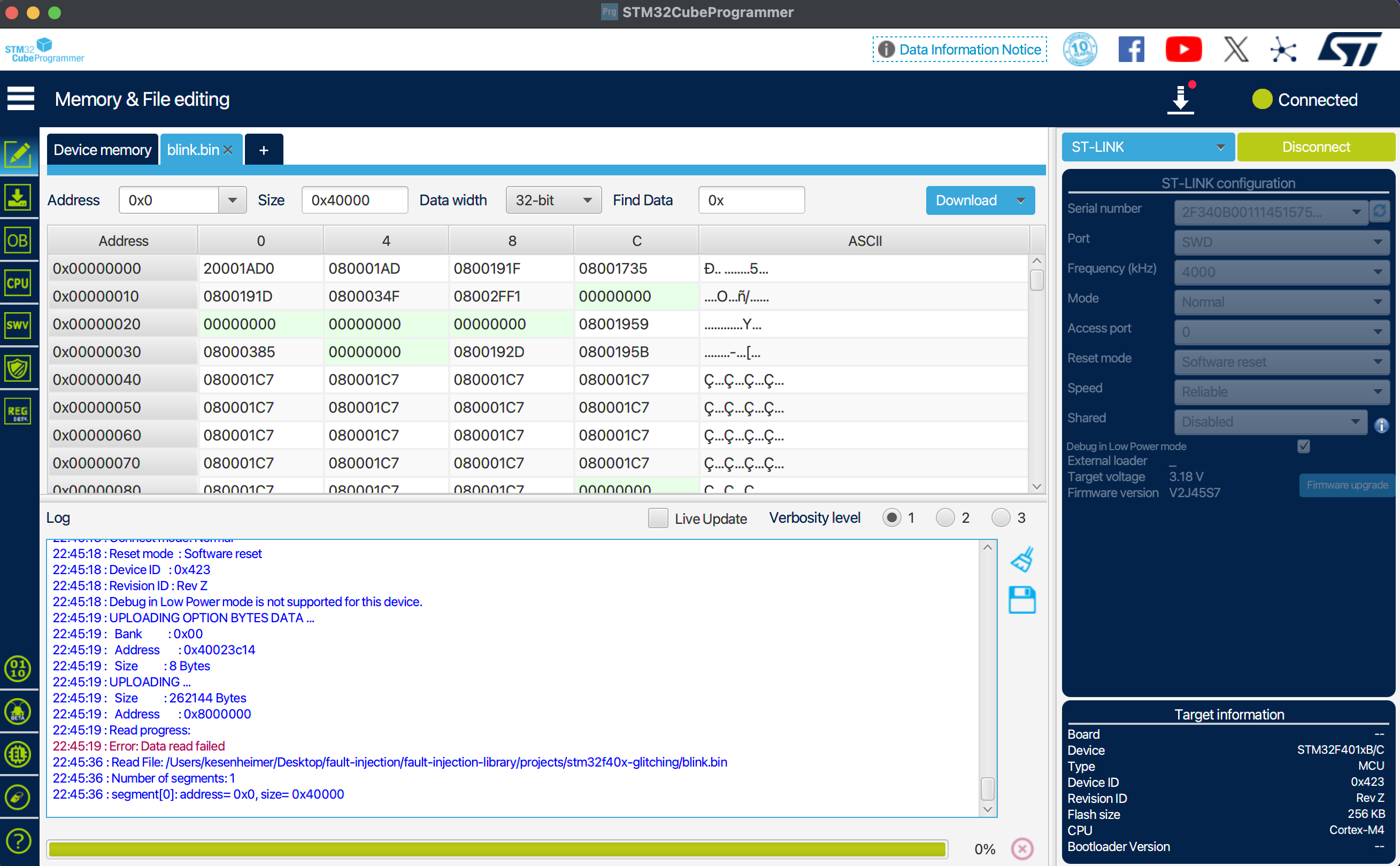
projects/stm32f40x/images/programmed_flash.png
