MKesenheimer/fault-injection-library/projects/stm32l422/datasheets/pinout-lqfp32.png

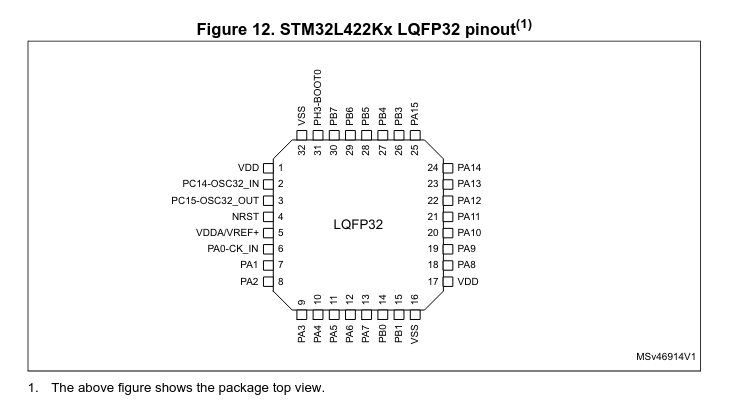
projects/stm32l422/datasheets/pinout-lqfp32.png
