MKesenheimer/fault-injection-library/projects/stm32l422/datasheets/power-scheme.png

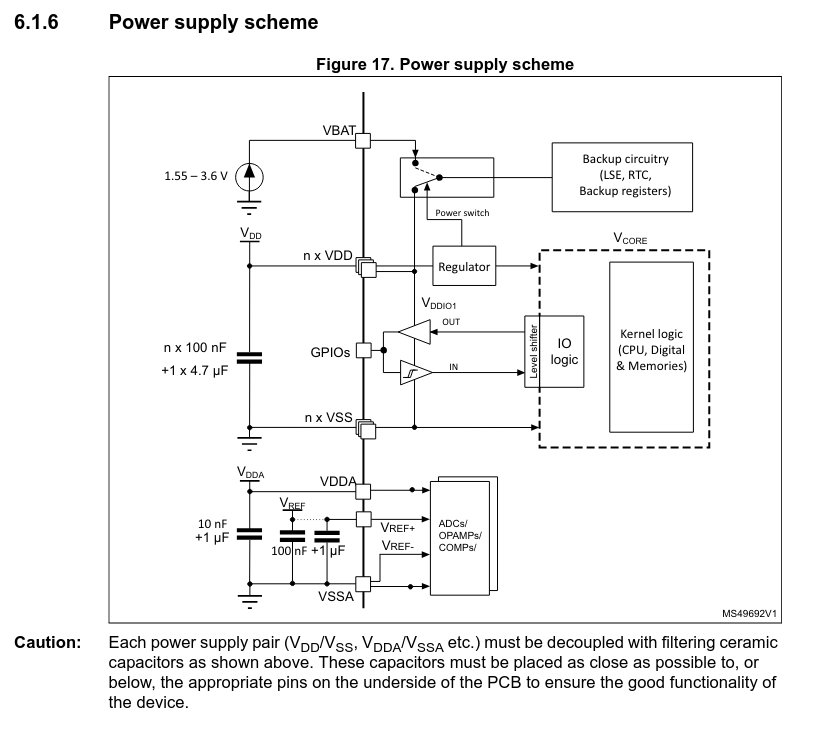
projects/stm32l422/datasheets/power-scheme.png
