MKesenheimer/fault-injection-library/projects/stm32l422/images/cw308-stm32l422.png

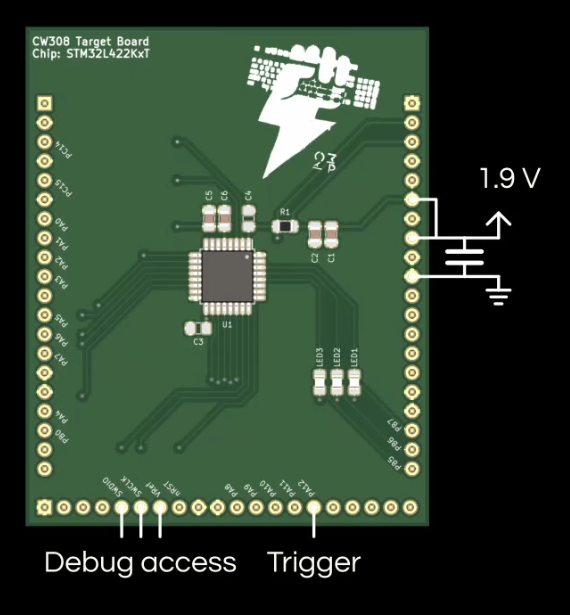
projects/stm32l422/images/cw308-stm32l422.png
