MKesenheimer/fault-injection-library/projects/stm32l422/images/erase-suppression-attack-success-cmd.png

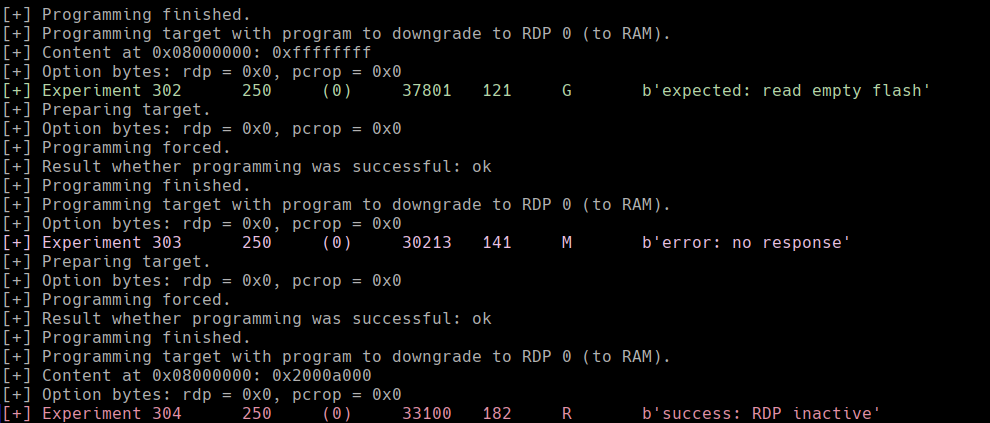
projects/stm32l422/images/erase-suppression-attack-success-cmd.png
