MKesenheimer/fault-injection-library/projects/stm32l422/images/erase-suppression-attack-success-parameterspace.png

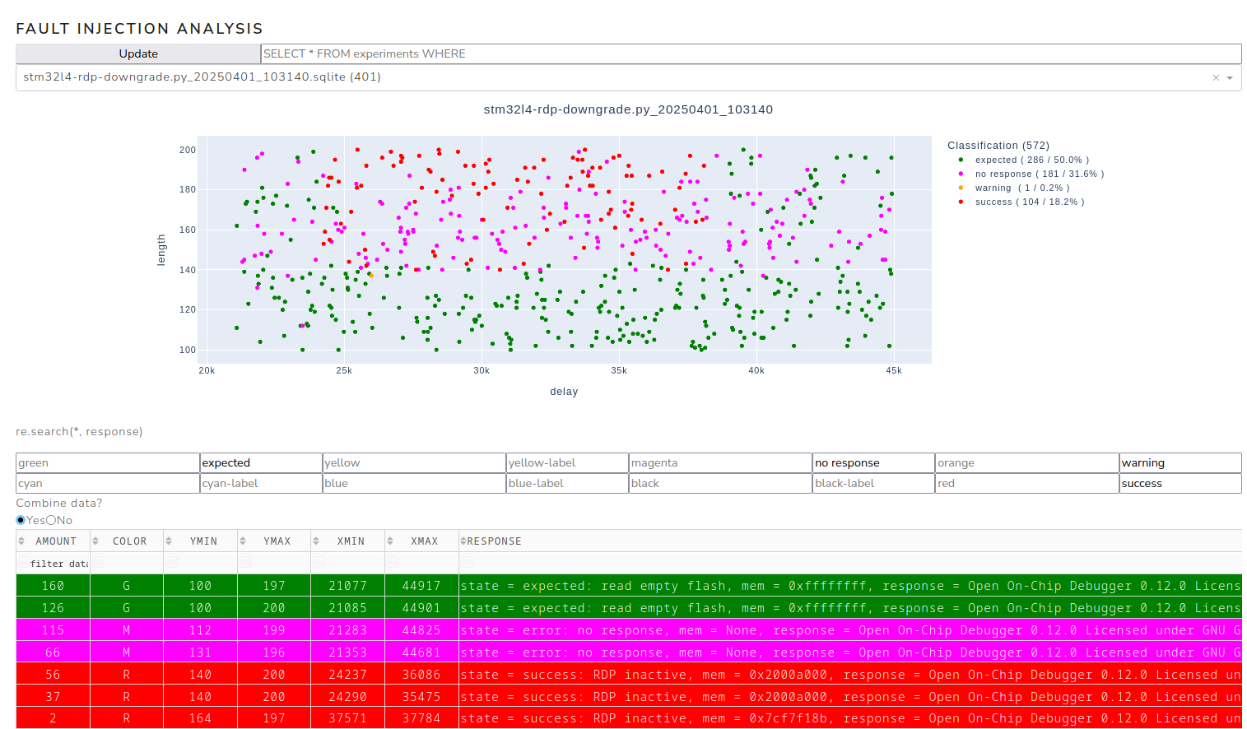
projects/stm32l422/images/erase-suppression-attack-success-parameterspace.png
