MKesenheimer/fault-injection-library/projects/stm32l422/images/flash_erase_100us.bmp

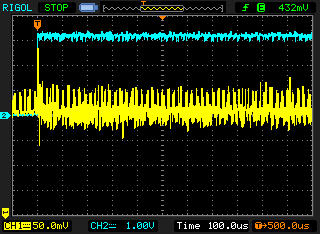
projects/stm32l422/images/flash_erase_100us.bmp
