MKesenheimer/fault-injection-library/projects/stm32l422/images/glitch-burst.png

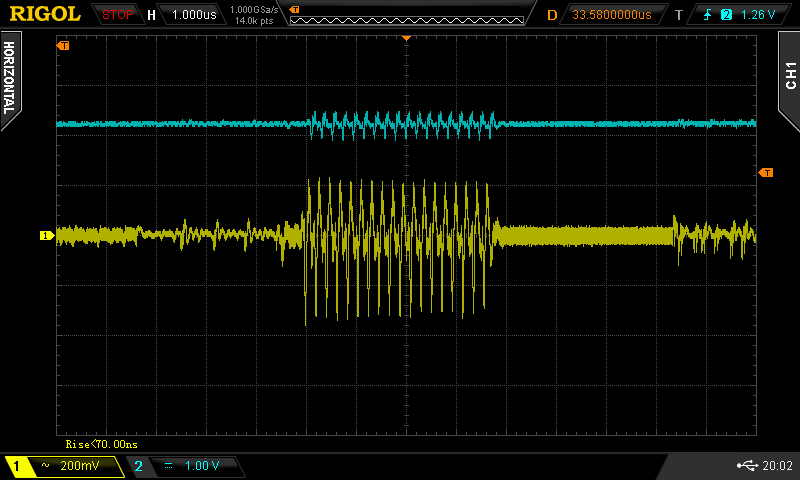
projects/stm32l422/images/glitch-burst.png
