MKesenheimer/fault-injection-library/projects/stm32l422/images/rdp_downgrade_100us.bmp

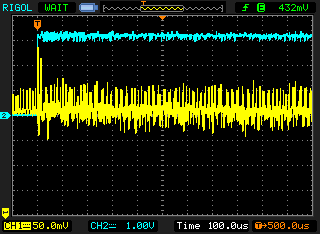
projects/stm32l422/images/rdp_downgrade_100us.bmp
