MKesenheimer/fault-injection-library/projects/stm32l422/images/stm32cubeprogrammer.png

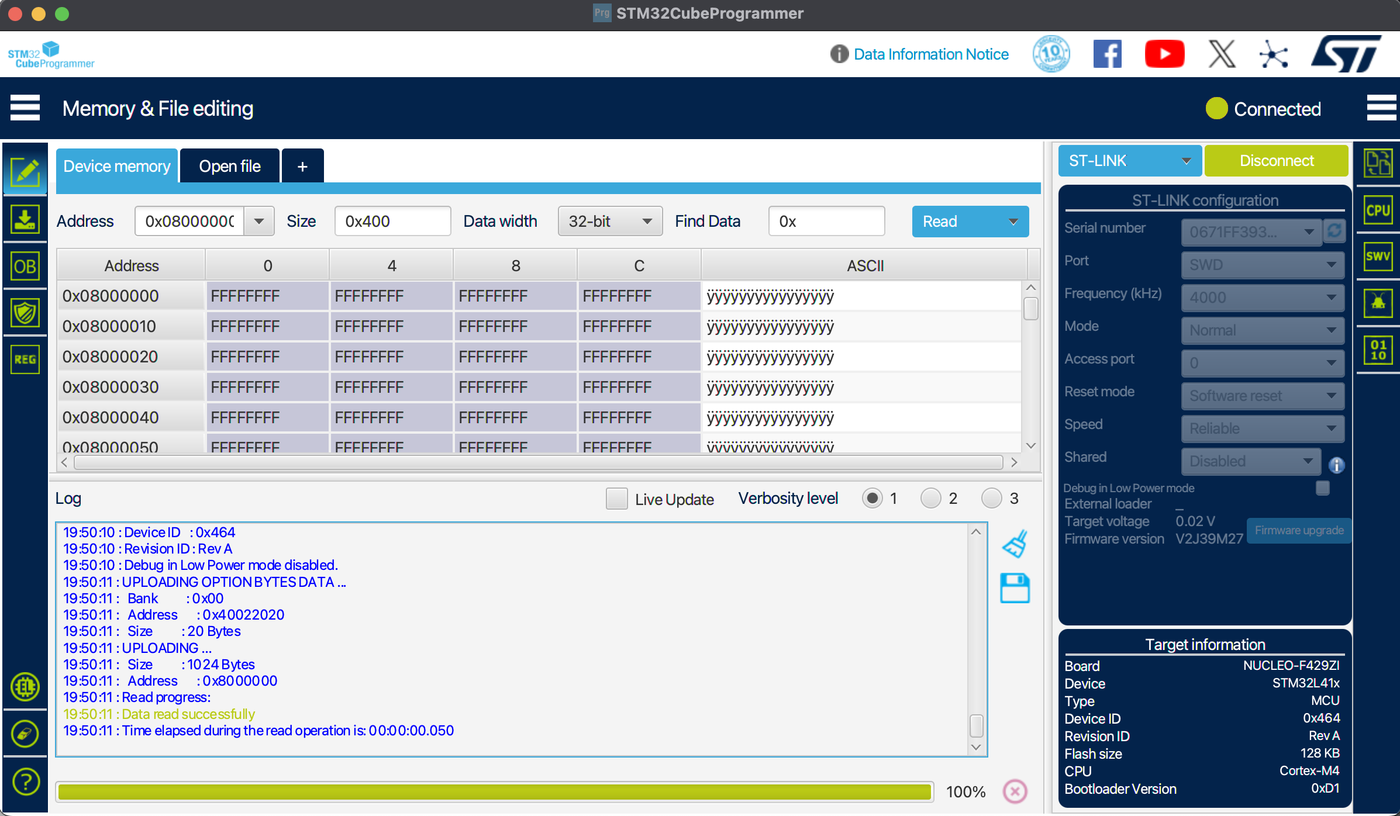
projects/stm32l422/images/stm32cubeprogrammer.png
