MKesenheimer/fault-injection-library/schematics/fusion360/pico-glitcher-v1/pico-glitcher-v1.1_sch.png

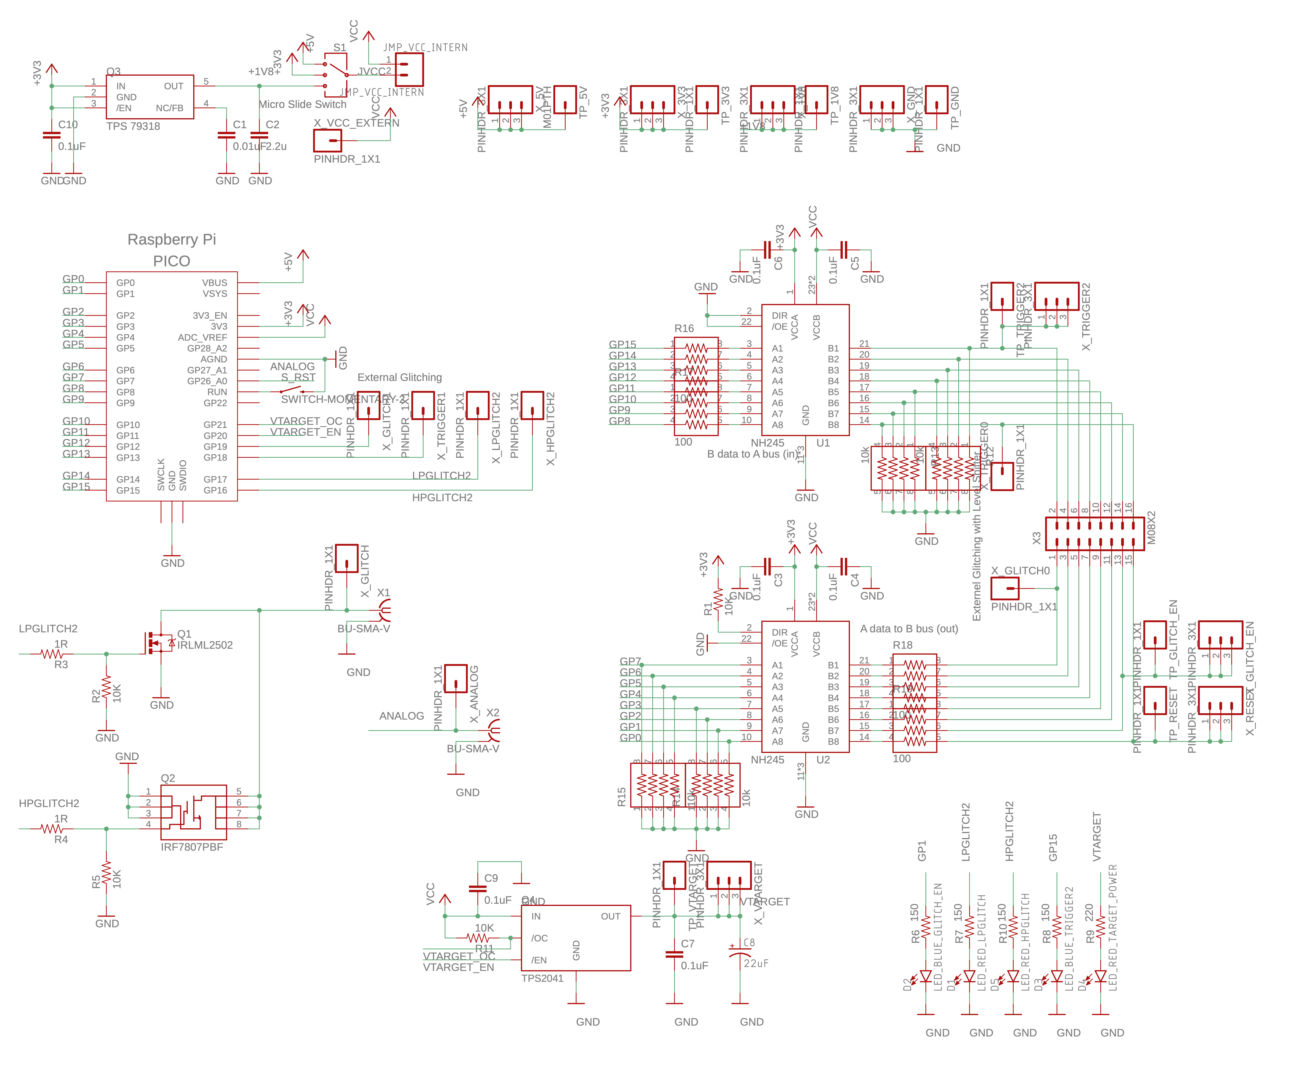
schematics/fusion360/pico-glitcher-v1/pico-glitcher-v1.1_sch.png
