MKesenheimer/fault-injection-library/projects/nrf52832/images/airtag/setup-2.JPG

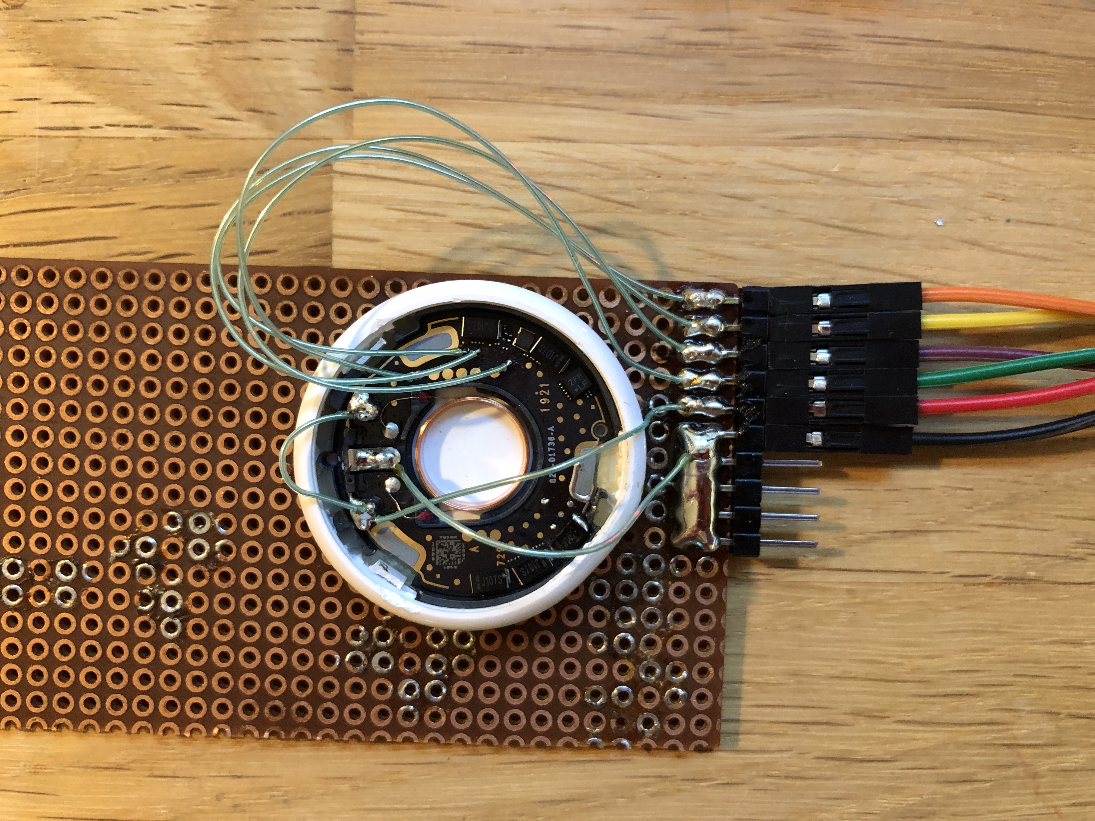
projects/nrf52832/images/airtag/setup-2.JPG
