MKesenheimer/fault-injection-library/projects/rp2350/images/glitching-setup.JPG

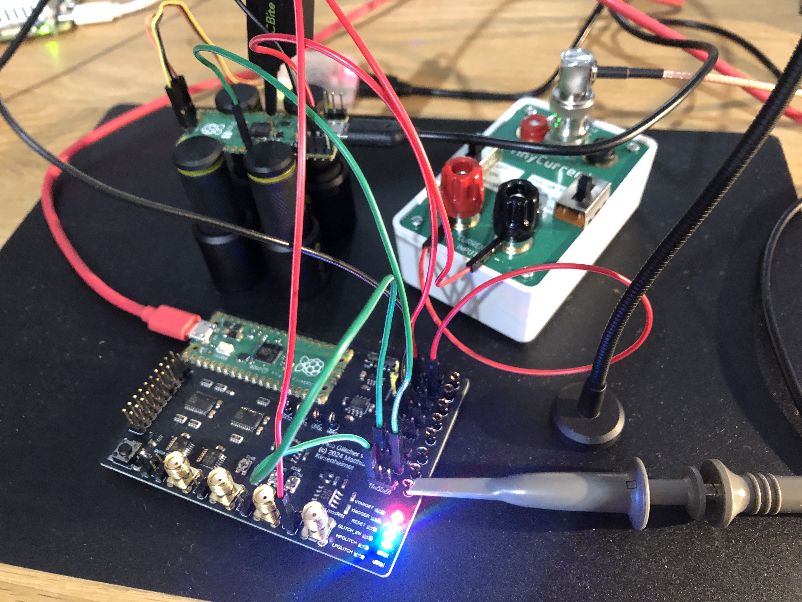
projects/rp2350/images/glitching-setup.JPG
