MKesenheimer/fault-injection-library/projects/rp2350/images/pcbite-setup.JPG

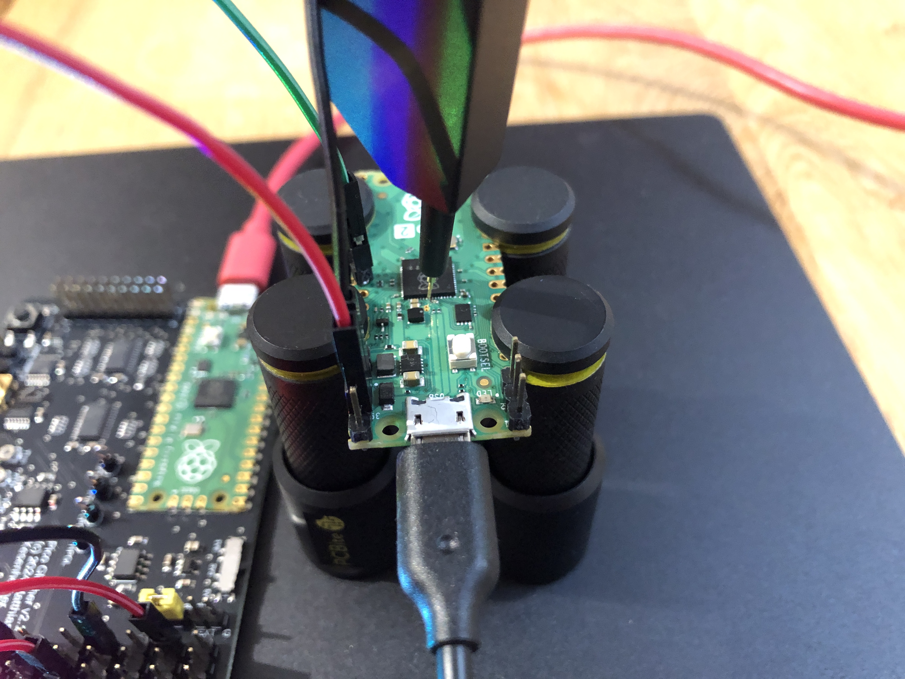
projects/rp2350/images/pcbite-setup.JPG
