MKesenheimer/fault-injection-library/projects/rp2350/images/rp2350-setup.JPG

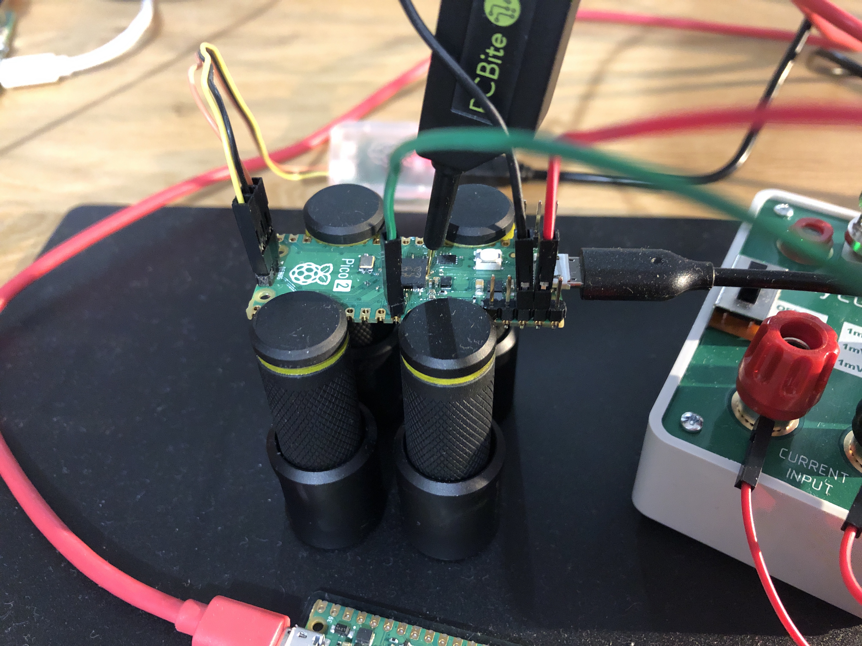
projects/rp2350/images/rp2350-setup.JPG
