MKesenheimer/fault-injection-library/projects/stm32f42x/images/setup-5.JPG

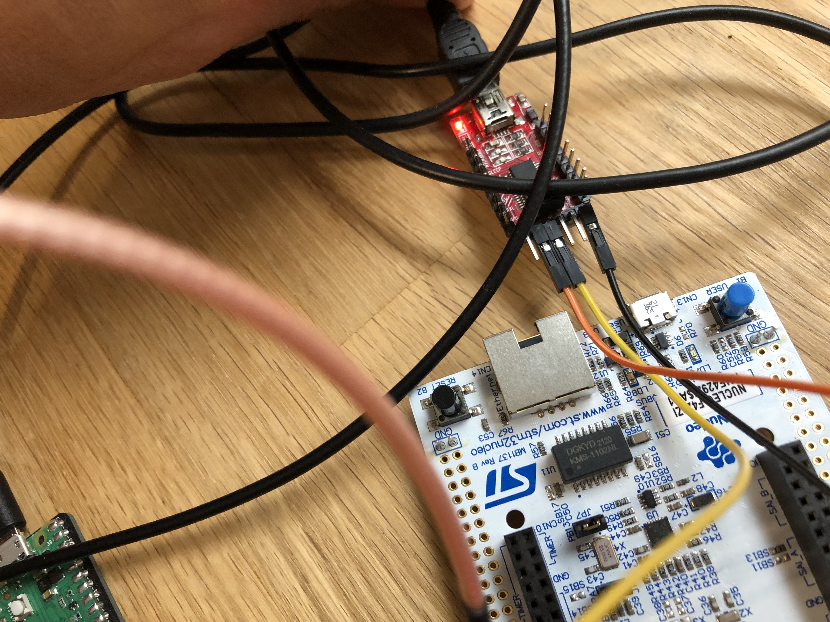
projects/stm32f42x/images/setup-5.JPG
