MKesenheimer/fault-injection-library/projects/stm32l422/images/setup-2.JPG

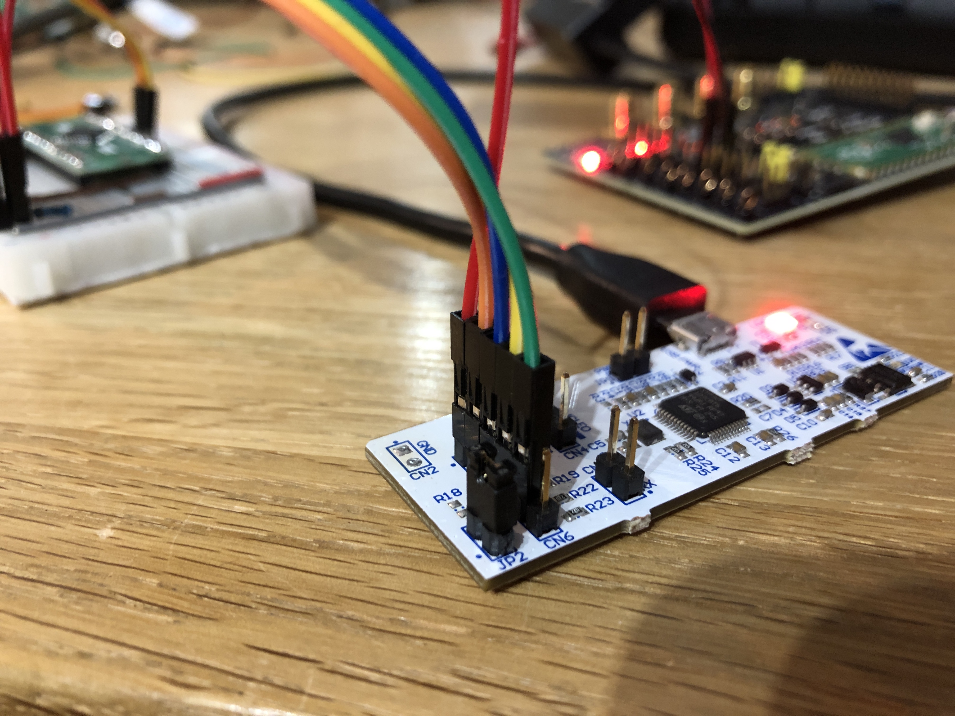
projects/stm32l422/images/setup-2.JPG
