MKesenheimer/fault-injection-library/projects/stm32l422/images/debug-unlock-A.png

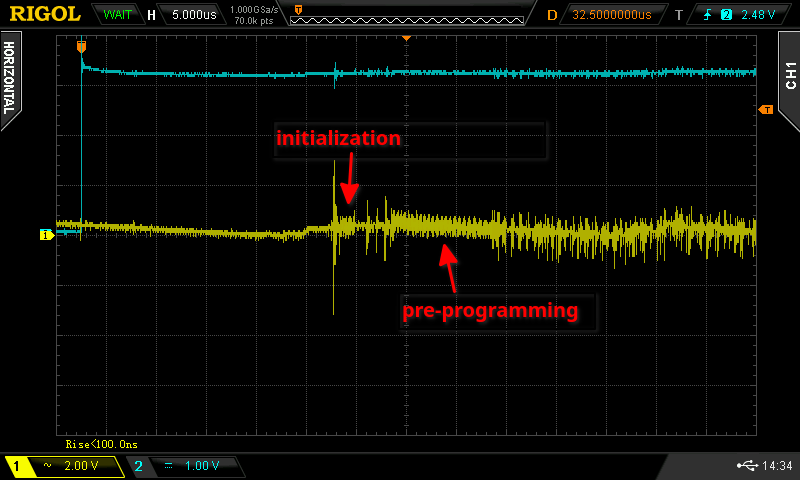
projects/stm32l422/images/debug-unlock-A.png
