MKesenheimer/fault-injection-library/projects/stm32l422/images/debug-unlock-B.png

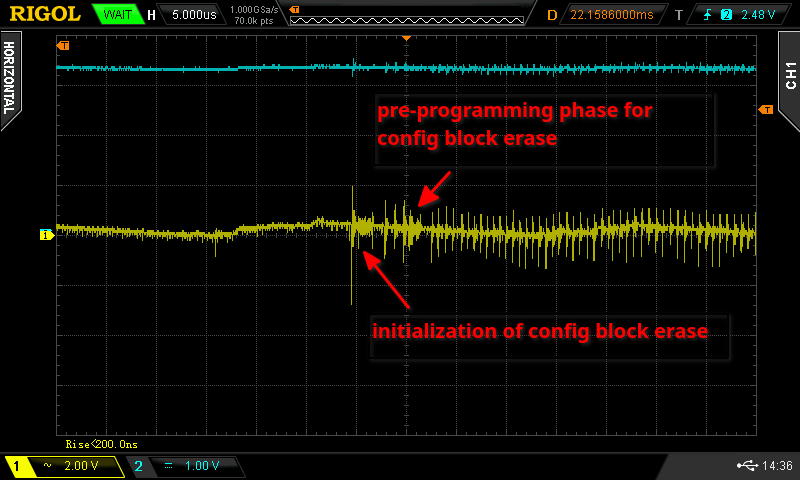
projects/stm32l422/images/debug-unlock-B.png
