MKesenheimer/fault-injection-library/projects/stm32l422/images/debug-unlock-end.png

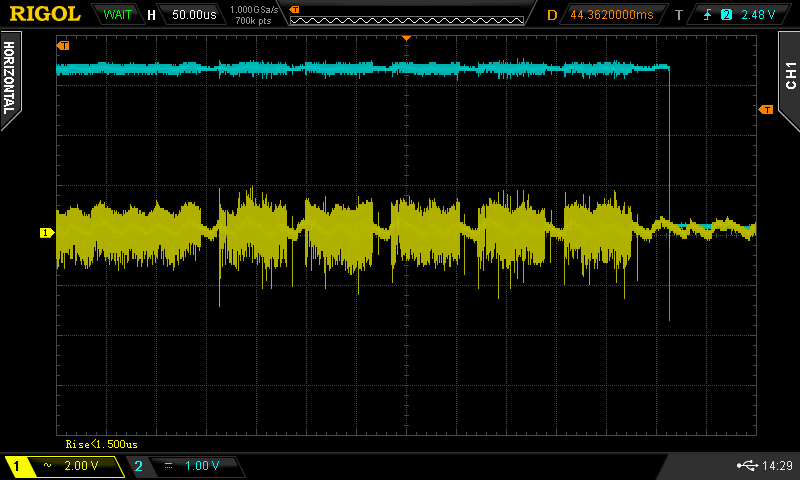
projects/stm32l422/images/debug-unlock-end.png
