MKesenheimer/fault-injection-library/projects/stm32l422/images/debug-unlock-mid.png

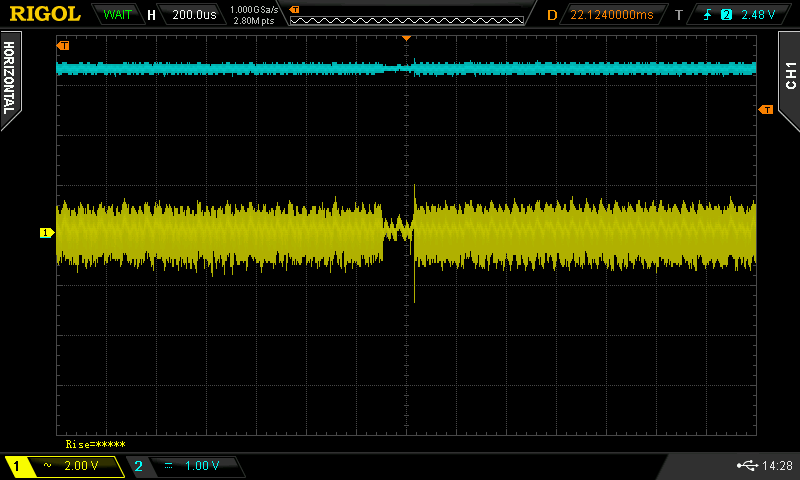
projects/stm32l422/images/debug-unlock-mid.png
