MKesenheimer/fault-injection-library/projects/stm32l422/images/debug-unlock-overview.png

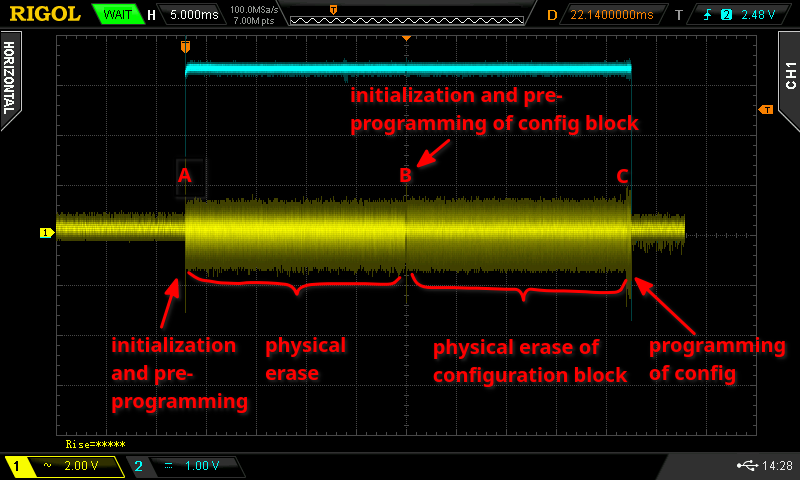
projects/stm32l422/images/debug-unlock-overview.png
