MKesenheimer/fault-injection-library/projects/stm32l422/images/debug-unlock-start.png

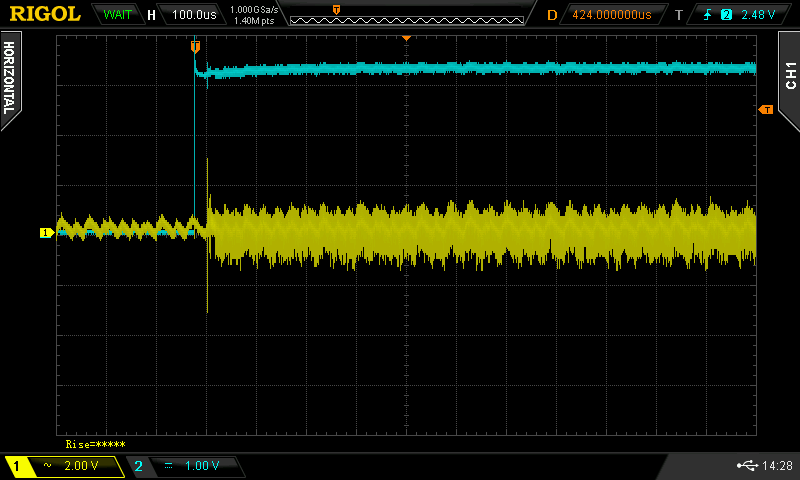
projects/stm32l422/images/debug-unlock-start.png
