MKesenheimer/fault-injection-library/findus/InteractivePchipEditor.py

#!/usr/bin/env python3
# Copyright (C) 2025 Bedri Zija - All Rights Reserved.
# You may use, distribute and modify this code under the terms of the GPL3 license.
#
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
import numpy as np
import matplotlib.pyplot as plt
from matplotlib.widgets import Button
from scipy.interpolate import PchipInterpolator
try:
    import tkinter as tk
    from tkinter.scrolledtext import ScrolledText
except Exception as _:
    pass

class InteractivePchipEditor:
    def __init__(self):
        """
        Initialize the plot with control points, curve, and interactive elements.
        Sets up the figure, axes, data points, annotations, and event handlers.
        """
        self.xpoints = [0, 100, 200, 300, 400, 500, 600, 700, 800, 900, 1050]
        self.ypoints = [3.3, 2.7, 2.7, 0.0, 2.7, 0.0, 2.7, 0.0, 2.7, 3.0, 3.3]

        self.fig, self.ax = plt.subplots()
        plt.subplots_adjust(bottom=0.3)
        self.selected_point = None
        self.annotations = []  # To store annotation objects for the points

        self.curve_line, = self.ax.plot([], [], label="PCHIP Curve", color="blue")
        self.point_scatter = self.ax.scatter(self.xpoints, self.ypoints, color="red", s=50, label="Control Points", picker=True)

        # Set axis limits and finer ticks
        self.ax.set_xlim(-50, 1550)
        self.ax.set_ylim(-0.2, 3.5)
        self.ax.set_xticks(np.arange(0, 1550, 50))  # X-axis gridlines at 50 ns
        self.ax.set_yticks(np.arange(0, 3.4, 0.1))  # Y-axis gridlines at 0.1 V

        self.ax.set_xlabel("Time (ns)")
        self.ax.set_ylabel("Voltage (V)")
        self.ax.legend()
        self.ax.grid(True)

        save_ax = plt.axes([0.8, 0.05, 0.1, 0.075])
        self.save_button = Button(save_ax, 'Save')
        self.save_button.on_clicked(self.save_points)

        self.update_curve()
        self.update_annotations()  # Initialize annotations
        self.cid_click = self.fig.canvas.mpl_connect('button_press_event', self.on_click)
        self.cid_release = self.fig.canvas.mpl_connect('button_release_event', self.on_release)
        self.cid_motion = self.fig.canvas.mpl_connect('motion_notify_event', self.on_motion)

    def update_curve(self):
        """
        Updates the curve based on the stored points using PCHIP interpolation.
        """
        interpolator = PchipInterpolator(self.xpoints, self.ypoints)
        x_smooth = np.linspace(min(self.xpoints), max(self.xpoints), 500)
        y_smooth = interpolator(x_smooth)
        self.curve_line.set_data(x_smooth, y_smooth)
        self.point_scatter.set_offsets(np.c_[self.xpoints, self.ypoints])
        self.fig.canvas.draw_idle()

    def update_annotations(self):
        """
        Clears all existing annotations associated with the object and resets the annotations list.
        """
        # Clear existing annotations
        for annotation in self.annotations:
            annotation.remove()
        self.annotations = []

        # Add new annotations for each point
        for x, y in zip(self.xpoints, self.ypoints):
            annotation = self.ax.annotate(
                f"{x:.0f}ns, {y:.1f}V",
                (x, y),
                textcoords="offset points",
                xytext=(5, 5),  # Offset to prevent overlap
                ha="center",
                fontsize=8,
                color="black",
                bbox=dict(boxstyle="round,pad=0.3", edgecolor="gray", facecolor="white", alpha=0.8),
            )
            self.annotations.append(annotation)
        self.fig.canvas.draw_idle()

    def on_click(self, event):
        """
        Handles mouse click events to select a point from the scatter plot.
        Updates self.selected_point if a point is clicked.
        
        Parameters:
            event: The mouse click event object.
        """
        if event.inaxes != self.ax:
            return
        contains, index = self.point_scatter.contains(event)
        if contains:
            self.selected_point = index["ind"][0]

    def on_release(self, event):
        """
        Handle the release event by deselecting the current point.
        Resets the selected_point attribute to None when the mouse button is released.

        Parameters:
            event: The mouse motion event containing xdata and ydata coordinates.
        """
        self.selected_point = None

    def on_motion(self, event):
        """
        Handles mouse motion events to adjust the position of a selected point.
        Modifies the selected point's coordinates, keeps xpoints sorted, and updates
        the curve and annotations on the plot.
        
        Parameters:
            event: The mouse motion event containing xdata and ydata coordinates.
        """
        if self.selected_point is None or event.inaxes != self.ax:
            return

        # Update point position
        new_x = np.clip(event.xdata, 0, 1500)
        new_y = np.clip(event.ydata, 0, 3.3)
        self.xpoints[self.selected_point] = new_x
        self.ypoints[self.selected_point] = new_y

        # Keep xpoints sorted
        self.xpoints, self.ypoints = zip(*sorted(zip(self.xpoints, self.ypoints)))
        self.xpoints, self.ypoints = list(self.xpoints), list(self.ypoints)

        # Update the curve and annotations
        self.update_curve()
        self.update_annotations()

    def save_points(self, event):
        """
        Formats and saves the x and y points into a string representation.
        Attempts to create a text window with the formatted points. If an error occurs,
        the output is printed to the console instead.
    
        Parameters:
            event: The event that triggered this method (not used in the current implementation).
        """
        xpoints_str = ", ".join(f"{x:.0f}" for x in self.xpoints)
        ypoints_str = ", ".join(f"{y:.1f}" for y in self.ypoints)
        output = f"xpoints = [{xpoints_str}]\nypoints = [{ypoints_str}]"
        try:
            self.create_text_window(output)
        except Exception as _:
            print(output)

    def get_points(self):
        """
        Converts each element in self.xpoints and self.ypoints to float.

        Returns:
            Returns the x and y points as lists of floats.
        """
        return [float(x) for x in self.xpoints], [float(x) for x in self.ypoints]

    def show(self, block=True):
        """
        Displays the current plot and pauses briefly to ensure it is updated properly.
    
        Parameters:
            block: If True, the display call blocks until the window is closed. If False, the display call returns immediately.
        """
        plt.show(block=block)
        plt.pause(0.001)

    def create_text_window(self, output):
        """
        Creates a new topmost window displaying the provided output text.
        The window features a scrollable text area with a fixed font and size.
        The text area is set to be editable to allow copying of content.

        Parameters:
            output: The text content to be displayed in the window.
        """
        self.root = tk.Tk()
        self.root.title("Saved Points")
        self.text_output = ScrolledText(self.root, wrap=tk.WORD, width=80, height=5, font=("Courier", 10))
        self.text_output.pack(fill=tk.BOTH, expand=True)
        self.text_output.insert(tk.END, output)
        self.text_output.configure(state='normal')  # Enable copying
        self.root.attributes("-topmost", True)  # Keep window on top
        self.root.mainloop()

def main():
    editor = InteractivePchipEditor()
    editor.show()
    editor.get_points()

if __name__ == "__main__":
    main()
