MKesenheimer/fault-injection-library/findus/findus.py

#!/usr/bin/env python3
# Copyright (C) 2024 Dr. Matthias Kesenheimer - All Rights Reserved.
# This file is based on TAoFI-FaultLib which is released under the GPL3 license.
# Go to https://github.com/raelize/TAoFI-FaultLib/LICENSE for full license details.
#
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
"""
Findus is a Python library to perform fault-injection attacks on embedded devices. It was developed for the Pico Glitcher, however, the ChipWhisperer Pro and the ChipWhisperer Husky is also supported.

This is the documentation of the findus module and all its classes.
"""

import sqlite3
import time
import ast
import serial
import sys
import datetime
import os
import glob
import random
from findus import pyboard
from importlib.metadata import version

class Database():
    """
    Database class managing access to the SQLite databases to store results from a glitching campaign.
    The parameter points stored in these databases are used to render an overview of the scanned parameter point via a web application.
    The web application and data analyzer can be run separately from the glitcher scripts by the following command:

        analyzer --directory databases

    Example usage:

        # import Database from findus
        from findus import Database
        ...
        database = Database(argv=argv)
        ...
        database.insert(experiment_id, delay, length, color, response)

    Example usage for multi-dimensional parameter space:

        # import Database from findus
        from findus import Database
        ...
        database = Database(argv=argv, column_names=["delay", "length", "t1"])
        ...
        database.insert(experiment_id, delay, length, t1, color, response)

    If you want to plot the `(length, t1)`-slice, you can call the `analyzer` script as follows:

        analyzer --directory databases -x length -y t1

    If `dbname` is not provided, a name will automatically generated based on `argv`.

    Methods:
        __init__: Default constructor.
        insert: Method to insert datapoints into the SQLite database.
        get_parameters_of_experiment_rel: Get the parameters of a dataset by experiment_id relative to the base row count.
        get_parameters_of_experiment: Get the parameters of a dataset by experiment_id.
        remove_conditional: Remove a parameter point from the database by a condition.
        remove_rel: Remove a parameter point from the database by experiment_id relative to the base row count.
        remove: Remove a parameter point from the database by experiment_id.
        cleanup: Remove all parameter points with a given color.
        get_number_of_experiments: Get the total number of performed experiments (number of datasets in the database).
        get_latest_experiment_id: Get the latest experiment_id.
        get_base_experiments_count: [Deprecated] Get the total number of performed experiments (number of datasets in the database).
        close: Close the connection to the database.
    """

    def __init__(self, argv:list[str], dbname:str = None, resume:bool = False, nostore:bool = False, column_names:list[str] = None, dirname:str = "databases"):
        """
        Default constructor of the Database class.

        Parameters:
            argv: Arguments that were supplied to the main-script. These arguments are stored as metadata when the database is instantiated.
            dbname: Name of the database to be generated.
            resume: Resume a previous run and write the results into the previously generated database
            nostore: Do not store the results in a database (can be used for debugging).
            column_names: Specify the parameter names of the experiments.
            dirname: Directory name to store the databases. If dirname is None, dbname can be an absolut path.
        """
        self.nostore = nostore
        if dirname is not None and not os.path.isdir(dirname):
            os.mkdir(dirname)

        if resume and dbname is None:
            list_of_files = glob.glob(f'{dirname}/*.sqlite')
            latest_file = max(list_of_files, key=os.path.getctime)[10:]
            print(f"[+] Resuming previous database {latest_file}")
            self.dbname = latest_file
        elif dbname is None:
            script_name = os.path.basename(sys.argv[0])
            self.dbname = f"{script_name}_%s.sqlite" % datetime.datetime.now().strftime("%Y%m%d_%H%M%S")
        else:
            self.dbname = dbname

        if dirname is not None:
            self.con = sqlite3.connect(f"{dirname}/" + self.dbname)
        else:
            self.con = sqlite3.connect(self.dbname)
        self.cur = self.con.cursor()
        self.argv = argv
        self.column_names = column_names
        if column_names is None:
            self.column_names = ["delay", "length"]
        if not resume:
            columns = ", ".join(f"{col} INTEGER" for col in self.column_names)
            #print(f"CREATE TABLE experiments (id INTEGER, {columns}, color TEXT, response BLOB)")
            self.cur.execute(f"CREATE TABLE experiments (id INTEGER, {columns}, color TEXT, response BLOB);")
            self.cur.execute("CREATE TABLE metadata (stime_seconds INTEGER, argv BLOB);")

        self.base_row_count = self.get_latest_experiment_id()
        if self.base_row_count is None:
            self.base_row_count = 0

    def get_column_names(self):
        self.cur.execute("SELECT * FROM experiments LIMIT 1")
        column_names = [description[0] for description in self.cur.description]
        return column_names[1:-2]

    def insert(self, *dataset):
        """
        Method to insert datapoints into the SQLite database.

        Parameters:
            dataset: Dataset consisting of experiment_id, delay, length, [additional parameters, ...], color and response.
                - experiment_id: ID of the experiment to insert into the database.
                - delay: Time from trigger until the glitch is set (in nano seconds).
                - length: Length of glitch (in nano seconds).
                - color: Color with which the parameter point (delay, length) is to be displayed in the graph.
                - response: Byte string of target response. 
        """
        if len(dataset) < 4:
            raise Exception("Database.insert: Too less arguments given.")
        experiment_id = dataset[0]
        if not self.nostore:
            if (experiment_id + self.base_row_count) == 0:
                s_argv = ' '.join(self.argv[1:])
                self.cur.execute("INSERT INTO metadata (stime_seconds,argv) VALUES (?,?)", [int(time.time()), s_argv])
            parameters = dataset[1:-2]
            color = dataset[-2]
            response = dataset[-1]
            #print(f"{experiment_id}, {parameters}, {color}, {response}")
            columns = ",".join(f"{col}" for col in self.column_names)
            values = [experiment_id + self.base_row_count, color, response]
            # insert the parameters after position 1
            values[1:1] = parameters
            #print(values)
            qmarks = ",".join("?" for _ in range(len(values)))
            #print(qmarks)
            #print(f"INSERT INTO experiments (id,{columns},color,response) VALUES ({qmarks})")
            self.cur.execute(f"INSERT INTO experiments (id,{columns},color,response) VALUES ({qmarks})", values)
            self.con.commit()

    def change_color_of_experiment_rel(self, experiment_id:int, color:str):
        """
        Change the color of a dataset by experiment_id relative to the base row count.

        Parameters:
            experiment_id: ID of the experiment r1elative to the base row count
        """
        self.cur.execute("UPDATE experiments SET color = (?) WHERE id = (?);", [color, experiment_id + self.base_row_count])
        self.con.commit()

    def change_color_of_experiment(self, experiment_id:int, color:str):
        """
        Change the color of a dataset by experiment_id.
        
        Parameters:
            experiment_id: ID of the experiment
        """
        self.cur.execute("UPDATE experiments SET color = (?) WHERE id = (?);", [color, experiment_id])
        self.con.commit()

    def get_parameters_of_experiment(self, experiment_id:int) -> list:
        """
        Get the parameters of a dataset by experiment_id.

        Parameters:
            experiment_id: ID of the experiment

        Returns:
            List of parameters.
        """
        self.cur.execute("SELECT * FROM experiments WHERE id = (?);", [experiment_id])
        self.con.commit()
        return next(self.cur, [None])

    def get_parameters_of_experiment_rel(self, experiment_id:int) -> list:
        """
        Get the parameters of a dataset by experiment_id relative to the base row count.

        Parameters:
            experiment_id: ID of the experiment relative to the base row count.

        Returns:
            List of parameters.
        """
        self.cur.execute("SELECT * FROM experiments WHERE id = (?);", [experiment_id + self.base_row_count])
        self.con.commit()
        return next(self.cur, [None])

    def remove_conditional(self, condition:str):
        r"""
        Remove a parameter point from the database by a condition.

        Parameters:
            condition: Condition to apply. For example, `id = 1000`, `id > 1000`, `color = \"C\"` or `delay < 6000`.
        """
        self.cur.execute(f"DELETE FROM experiments WHERE {condition};")
        self.con.commit()

    def remove(self, experiment_id:int):
        """
        Remove a parameter point from the database by experiment_id.

        Parameters:
            experiment_id: ID of the experiment to insert into the database.
        """
        self.cur.execute("DELETE FROM experiments WHERE id = (?);", [experiment_id])
        self.con.commit()

    def remove_rel(self, experiment_id:int):
        """
        Remove a parameter point from the database by experiment_id relative to the base row count.

        Parameters:
            experiment_id: ID of the experiment to insert into the database.
        """
        self.cur.execute("DELETE FROM experiments WHERE id = (?);", [experiment_id + self.base_row_count])
        self.con.commit()

    def cleanup(self, color):
        """
        Remove all parameter points with a given color.
        """
        self.cur.execute("DELETE FROM experiments WHERE color = (?);", [color])
        #self.cur.execute("DELETE FROM experiments WHERE length >= (?);", [color])
        self.con.commit()

    def get_number_of_experiments(self) -> int:
        """
        Get the total number of performed experiments (number of datasets in the database).

        Returns:
            Number of experiments performed so far in the current database.
        """
        self.cur.execute("SELECT count(id) FROM experiments")
        result = self.cur.fetchone()
        row_count = result[0]
        return row_count

    def get_latest_experiment_id(self) -> int:
        """
        Get the latest experiment_id.

        Returns:
            Experiment ID.
        """
        try:
            self.cur.execute("SELECT * FROM experiments WHERE id=(SELECT max(id) FROM experiments);")
            self.con.commit()
            return next(self.cur, [None])[0]
        except sqlite3.OperationalError:
            return 0

    def get_base_experiments_count(self) -> int:
        """
        [Deprecated] Get the total number of performed experiments (number of datasets in the database).

        Returns:
            Number of experiments performed so far in the current database.
        """
        return self.base_row_count

    def close(self):
        """
        Close the connection to the database.
        """
        self.con.close()

class Serial():
    r"""
    Class to manage serial connections more easily.
    Example usage:

        # import Serial from findus
        from findus import Serial
        ser = Serial(port="/dev/ttyUSB0")
        ser.write(b'\x7f')
        ...
        result = ser.read(3)

    Methods:
        __init__: Default constructor.
        write: Write data out via the serial interface.
        read: Read data from the serial interface.
        reset: Reset target via DTR pin and flush data lines.
        flush: Flush data buffers.
        flush_v2: Flush serial data buffers with timeout.
        close: Close serial connection.
    """
    def __init__(self, port:str = "/dev/ttyUSB0", baudrate:int = 115200, timeout:float = 0.1, bytesize:int = 8, parity:str = 'N', stopbits:int = 1):
        """
        __init__: Default constructor.

        Parameters:
            port: Port identifier of the serial connection.
            baudrate: Baudrate of the serial connection.
            timeout: Timeout after the serial connection stops listening.
            bytesize: Number of bytes per payload.
            parity: Even ('E') or Odd ('O') parity.
            stopbits: Number of stop bits.
        """
        self.ser = None
        self.port = port
        self.baudrate = baudrate
        self.timeout = timeout
        self.bytesize = bytesize
        self.parity = parity
        self.stopbits = stopbits
        self.init()

    def init(self):
        """
        Initializes the serial connection. Can be called again, if the connection was closed previously.
        """
        try:
            self.ser = serial.Serial(port=self.port, baudrate=self.baudrate, timeout=self.timeout, bytesize=self.bytesize, parity=self.parity, stopbits=self.stopbits)
        except Exception as _:
            print("[-] Serial device not found. Aborting")
            sys.exit(-1)

    def write(self, message: bytes) -> int:
        """
        Write the bytes data to the port. This should be of type `bytes` (or compatible such as `bytearray` or `memoryview`). Unicode strings must be encoded (e.g. `'hello'.encode('utf-8')`.

        Parameters:
            message: Data to send
        Returns:
            Number of bytes written.
        """
        return self.ser.write(message)

    def read(self, length: int) -> bytes:
        """
        Read `length` bytes from the serial port. If a timeout is set it may return fewer characters than requested. With no timeout it will block until the requested number of bytes is read.

        Parameters:
            length: Number of bytes to read.
        Returns:
            Bytes read from the port.
        """
        response = self.ser.read(length)
        return response
    
    def readline(self) -> bytes:
        r"""
        Read up to one line, including the \n at the end.

        Returns:
            The line received from the target.
        """
        response = self.ser.readline()
        return response

    def read_until(self, expected:bytes = '\n', size:int = None) -> bytes:
        r"""
        Read until an expected sequence is found (`\n` by default), the size is exceeded or until timeout occurs. If a timeout is set it may return fewer characters than requested. With no timeout it will block until the requested number of bytes is read.

        Parameters:
            expected: The byte string to search for.
            size: Number of bytes to read

        Returns:
            The line received from the target.
        """
        response = self.ser.read_until(expected, size)
        return response

    def reset_target(self, debug:bool = False) -> bool:
        """
        Reset target via DTR pin and flush data lines. Can be used alternatively to the reset lines of the Pico Glitcher (or ChipWhisperer Husky, or ChipWhisperer Pro) to reset the target.

        Parameters:
            debug: If set to true, garbage on the serial interface is plotted to tty.
        """
        print("[+] Resetting target...")
        self.ser.dtr = True
        time.sleep(0.1)
        self.ser.dtr = False
        response = self.ser.read(4096)
        if debug:
            for line in response.splitlines():
                print('\t', line.decode())

    def reset(self, debug:bool = False) -> bool:
        """
        Reset target via DTR pin and flush data lines. Can be used alternatively to the reset lines of the Pico Glitcher (or ChipWhisperer Husky, or ChipWhisperer Pro) to reset the target. This function is the same as `reset_target`. Left in for downward compatibility.

        Parameters:
            debug: If set to true, garbage on the serial interface is plotted to tty.
        """
        return self.reset_target(debug)

    def flush(self):
        """
        Flush serial data buffers.
        """
        self.ser.reset_input_buffer()

    def flush_v2(self, timeout:float = 0.01):
        """
        Flush serial data buffers with timeout.

        Parameters:
            timeout: Timeout after the serial connection stops listening. Can be tweaked to make sure all data is flushed.
        """
        self.ser.timeout = timeout
        self.ser.read(8192)
        self.ser.timeout = self.timeout

    def close(self):
        """
        Close serial connection.
        """
        self.ser.close()

class MicroPythonScript():
    def __init__(self, port:str = '/dev/ttyACM1', debug:bool = False):
        self.port   = None
        self.pyb    = None
        self.debug = debug

    def init(self, port:str, micropy_script:str, debug:bool = False):
        self.port = port
        try:
            self.pyb = pyboard.Pyboard(self.port)
        except Exception as _:
            print("[-] Pico Glitcher not found. Aborting")
            sys.exit(-1)
        self.pyb.enter_raw_repl()
        self.pyb.exec(f'import {micropy_script}')
        self.pyb.exec(f'mp = {micropy_script}.{micropy_script}()')

# inherit functionality and overwrite some functions
class PicoGlitcherInterface(MicroPythonScript):
    def clean_init(self):
        self.pyb.exec('mp.init()')

    def switch_pio(self, pio_base:int):
        if pio_base == 0 or pio_base == 1:
            self.pyb.exec(f'mp.switch_pio({pio_base})')

    def get_firmware_version(self):
        version_bytes = self.pyb.exec('mp.get_firmware_version()')
        decoded_str = version_bytes.decode('utf-8').strip()
        return ast.literal_eval(decoded_str)

    def set_trigger(self, mode:str, pin_trigger:str, edge_type:str = "rising"):
        self.pyb.exec(f'mp.set_trigger("{mode}", "{pin_trigger}", "{edge_type}")')

    def set_number_of_edges(self, number_of_edges:int):
        self.pyb.exec(f'mp.set_number_of_edges({number_of_edges})')

    def set_frequency(self, frequency:int):
        self.pyb.exec(f'mp.set_frequency({frequency})')

    def get_frequency(self):
        return self.pyb.exec('mp.get_frequency()')

    def set_baudrate(self, baud:int):
        self.pyb.exec(f'mp.set_baudrate({baud})')

    def set_number_of_bits(self, number_of_bits:int):
        self.pyb.exec(f'mp.set_number_of_bits({number_of_bits})')

    def set_pattern_match(self, pattern:int):
        self.pyb.exec(f'mp.set_pattern_match({pattern})')

    def power_cycle_target(self, power_cycle_time:float):
        self.pyb.exec(f'mp.power_cycle_target({power_cycle_time})')

    def power_cycle_reset(self, power_cycle_time:float):
        self.pyb.exec(f'mp.power_cycle_reset({power_cycle_time})')

    def set_mux_voltage(self, voltage:str):
        self.pyb.exec(f'mp.set_mux_voltage("{voltage}")')

    def cleanup_pio(self):
        self.pyb.exec('mp.cleanup_pio()')

    def arm(self, delay:int, length:int, number_of_pulses:int = 1, delay_between:int = 0):
        if number_of_pulses == 1:
            self.pyb.exec(f'mp.arm({delay}, {length})')
        else:
            self.pyb.exec(f'mp.arm({delay}, {length}, {number_of_pulses}, {delay_between})')

    def arm_double(self, delay1:int, length1:int, delay2:int, length2:int):
        self.pyb.exec(f'mp.arm_double({delay1}, {length1}, {delay2}, {length2})')

    def arm_multiplexing(self, delay:int, mul_config:dict, vinit:str = "config"):
        return self.pyb.exec(f'mp.arm_multiplexing({delay}, {mul_config}, "{vinit}")')

    def arm_pulseshaping_from_config(self, delay:int, ps_config:list[list[int]]):
        return self.pyb.exec(f'mp.arm_pulseshaping_from_config({delay}, {ps_config})')

    def arm_pulseshaping_from_spline(self, delay:int, xpoints:list[int], ypoints:list[float]):
        return self.pyb.exec(f'mp.arm_pulseshaping_from_spline({delay}, {xpoints}, {ypoints})')

    def arm_pulseshaping_from_lambda(self, delay:int, ps_lambda:str, pulse_number_of_points:int):
        return self.pyb.exec(f'mp.arm_pulseshaping_from_lambda({delay}, {ps_lambda}, {pulse_number_of_points})')

    def arm_pulseshaping_from_list(self, delay:int, pulse:list[int]):
        return self.pyb.exec(f'mp.arm_pulseshaping_from_list({delay}, {pulse})')

    def initiate_reset(self):
        self.pyb.exec('mp.initiate_reset()')

    def release_reset(self):
        self.pyb.exec('mp.release_reset()')

    def disable_vtarget(self):
        self.pyb.exec('mp.disable_vtarget()')

    def enable_vtarget(self):
        self.pyb.exec('mp.enable_vtarget()')

    def reset_target(self, reset_time:float):
        self.pyb.exec(f'mp.reset_target({reset_time})')

    def configure_gpio_out(self, pin_number:int):
        self.pyb.exec(f'mp.configure_gpio_out({pin_number})')

    def set_gpio(self, pin_number:int, value:int):
        self.pyb.exec(f'mp.set_gpio({pin_number}, {value})')

    def block(self, timeout:float):
        self.pyb.exec(f'mp.block({timeout})')

    def check_glitch(self) -> bool:
        ret = self.pyb.exec('mp.check_glitch()')
        return ret.strip() == b'True'

    def get_sm1_output(self) -> str:
        return self.pyb.exec('mp.get_sm1_output()')

    def set_lpglitch(self):
        self.pyb.exec('mp.set_lpglitch()')

    def set_hpglitch(self):
        self.pyb.exec('mp.set_hpglitch()')
    
    def set_ext_mosfet(self, pin):
        if len(pin) == 1:
            self.pyb.exec(f'mp.set_ext_mosfet({pin[0]})')
        else:
            self.pyb.exec('mp.set_ext_mosfet()')

    def set_multiplexing(self):
        self.pyb.exec('mp.set_multiplexing()')

    def set_pulseshaping(self, vinit=1.8):
        self.pyb.exec(f'mp.set_pulseshaping({vinit})')

    def do_calibration(self, vhigh:float):
        self.pyb.exec(f'mp.do_calibration({vhigh})')

    def apply_calibration(self, vhigh:float, vlow:float, store:bool = True):
        self.pyb.exec(f'mp.apply_calibration({vhigh}, {vlow}, {store})')

    def waveform_generator(self, frequency:int, gain:float, waveid:int):
        return self.pyb.exec(f'mp.waveform_generator({frequency}, {gain}, {waveid})')

    def set_dead_zone(self, dead_time:float, pin_condition:str, condition:str):
        self.pyb.exec(f'mp.set_dead_zone({dead_time}, "{pin_condition}", "{condition}")')

    def change_config_and_reset(self, key, value) -> str:
        return self.pyb.exec(f'mp.change_config_and_reset("{key}", "{value}")')

    def change_config_and_apply(self, key, value) -> str:
        return self.pyb.exec(f'mp.change_config_and_apply("{key}", "{value}")')

    def arm_adc(self):
        self.pyb.exec('mp.arm_adc()')

    def get_adc_samples(self, timeout:float = 1.0) -> list[int]:
        return self.pyb.exec(f'mp.get_adc_samples({timeout})')

    def configure_adc(self, number_of_samples:int = 1024, sampling_freq:int = 500_000):
        self.pyb.exec(f'mp.configure_adc({number_of_samples}, {sampling_freq})')

    def hard_reset(self):
        self.pyb.exec('mp.hard_reset()')

class Glitcher():
    """
    Glitcher template class. This class defines a common anchestor from which other glitcher modules should inherit from.

    Methods:
        __init__: Default constructor. Does nothing in this case.
        classify: Template method to classify an output state.
        colorize: Returns a colored string depending on a color identifier (G, Y, R, M, C, B).
        get_speed: Calculate and return the average speed of the glitching campaign (glitches per second).
    """
    def __init__(self):
        """
        Default constructor. Does nothing in this case.
        """
        pass

    @staticmethod
    def classify(state:bytes) -> str:
        """
        Template method to classify an output state. Overload this class if you want to customize the targets response classification. Alternatively, use the built-in class `GlitchState` to characterize the targets responses. Remember to define certain response states depending on the possible responses. See class `STM32Bootloader` for an example.

            from findus import PicoGlitcher
            from findus.STM32Bootloader import STM32Bootloader
            glitcher = PicoGlitcher()
            ...
            programmer = STM8Programmer(port=self.args.target, baud=115200)
            ...
            state = programmer.bootloader_enter()
            ...
            glitcher.classify(state)
        """
        color = 'C'
        if b'expected' in state:
            color = 'G'
        elif b'ok' in state:
            color = 'C'
        elif b'error' in state:
            color = 'M'
        elif b'failure' in state:
            color = 'B'
        elif b'timeout' in state:
            color = 'Y'
        elif b'warning' in state:
            color = 'O'
        elif b'success' in state:
            color = 'R'
        return color

    @staticmethod
    def colorize(s:str, color:str) -> str:
        """
        Returns a colorized string depending on a color identifier (G, Y, R, M, C, B, O, Z).
        
        Parameters:
            s: The string you want to colorize.
            color: Color identifier, one of 'G', 'Y', 'R', 'M', 'C', 'B', 'O', 'Z' (black).
        Returns:
            Returns the colorized string.
        """
        colors = {
            'G': [182, 214, 168],
            'Y': [232, 237, 164],
            'R': [228, 145, 167],
            'M': [234, 192, 226],
            'C': [113, 198, 177],
            'B': [109, 174, 217],
            'O': [197, 148, 124],
            'Z': [31, 31, 31]
        }
        #colors = {
        #    'G': [0, 255, 0],
        #    'Y': [255, 255, 0],
        #    'R': [170, 0, 0],
        #    'M': [255, 0, 255],
        #    'C': [0, 255, 255],
        #    'B': [0, 0, 255],
        #    'O': [255, 100, 50],
        #    'Z': [0, 0, 0]
        #}
        r = colors[color][0]
        g = colors[color][1]
        b = colors[color][2]
        return f"\033[38;2;{r};{g};{b}m{s}\033[0m"

    @staticmethod
    def get_speed(start_time:int, number_of_experiments:int) -> int | str:
        """
        Calculate and return the average speed of the glitching campaign (glitches per second).
        
        Parameters:
            start_time: Start time of the glitching campaign in seconds.
            number_of_experiments: Number of experiments carried out so far.
        Returns:
            Returns the average number of experiments per second.
        """
        elapsed_time = int(time.time()) - start_time
        if elapsed_time == 0:
            return 'NA'
        else:
            return number_of_experiments // elapsed_time

class PicoGlitcher(Glitcher):
    """
    Class giving access to the functions of the Pico Glitcher. Derived from Glitcher class.
    For an example, connect the Pico Glitcher as follows:

    - Remove any capacitors on your target device that could infere with the glitch.
    - Set the desired output voltage `VTARGET` with the micro switch.
    - Connect `VTARGET` with the voltage input of your target (`VCC`).
    - Connect the `GLITCH` output (either the SMA connector or the pin header) to an appropriate target pin, for example `VCC`.
    - Connect the `RESET` output with the target's reset input.
    - Connect the `RESET` line with the `TRIGGER` input.
    
    Code snippet:

        from findus import PicoGlitcher
        glitcher = PicoGlitcher()
        glitcher.init(port="/dev/ttyACM0", ext_power="/dev/ttyACM1", ext_power_voltage=3.3)
        # set up database, define delay and length
        ...
        # one shot glitching
        glitcher.arm(delay, length)
        # reset target for 0.01 seconds (the rising edge on reset line triggers the glitch)
        glitcher.reset_target(0.01)
        # read the response from the device (for example UART, SWD, etc.)
        response = ...
        # classify the response and put into database
        color = glitcher.classify(response)
        database.insert(experiment_id, delay, length, color, response)

    Methods:
        __init__: Default constructor. Does nothing in this case.
        init: Default initialization procedure.
        arm: Arm the Pico Glitcher and wait for trigger condition.
        block: Block the main script until trigger condition is met. Times out.
        reset: Reset the target via the Pico Glitcher's `RESET` output.
        release_reset: Release the reset to the target via the Pico Glitcher's `RESET` output.
        power_cycle_target: Power cycle the target via the Pico Glitcher `VTARGET` output or optionally via the multiplexing stage.
        power_cycle_reset: Power cycle and reset the target via the Pico Glitcher `RESET` and `VTARGET` output.
        reset_and_eat_it_all: Reset the target and flush the serial buffers.
        reset_wait: Reset the target and read from serial.
        set_lpglitch: Enable low-power MOSFET for glitch generation.
        set_hpglitch: Enable high-power MOSFET for glitch generation.
        rising_edge_trigger: Configure the Pico Glitcher to trigger on a rising edge on the `TRIGGER` line.
        uart_trigger: Configure the Pico Glitcher to trigger when a specific byte pattern is observed on the `TRIGGER` line.
        set_cpu_frequency: Set the CPU frequency of the Raspberry Pi Pico.
        get_cpu_frequency: Get the current CPU frequency of the Raspberry Pi Pico.
        __del__: Default deconstructor. Disconnects Pico Glitcher.
    """
    def __init__(self):
        """
        Default constructor. Does nothing in this case.
        """
        self.pico_glitcher = None

    def __del__(self):
        print("[+] Terminating gracefully.")
        try:
            self.hard_reset()
        except Exception as _:
            pass

    def clean_init(self):
        """
        Re-initialize the Pico Glitcher on the fly. Can be used to make changes to the configuration on the fly.
        """
        self.pico_glitcher.clean_init()

    def init(self, port:str, ext_power:str = None, ext_power_voltage:float = 3.3, enable_vtarget:bool = True):
        """
        Default initialization procedure of the Pico Glitcher. Default configuration is:

        - Set the trigger input to rising-edge trigger on `TRIGGER` input and assume triggering when the reset is released.
        - Set a dead time that prohibits triggering within a certain time (trigger rejection). This is intended to exclude false trigger conditions.
        - Use the low-power crowbar MOSFET as default.

        Parameters:
            port: Port identifier of the Pico Glitcher.
            ext_power: Port identifier of the external power supply (RD6006). If None, target is assumed to be supplied by `VTARGET` of the Pico Glitcher.
            ext_power_voltage: Supply voltage of the external power supply. Must be used in combination with `ext_power`. You can not control the supply voltage `VTARGET` of the Pico Glitcher with this parameter.
        """
        self.pico_glitcher = PicoGlitcherInterface()
        self.pico_glitcher.init(port, 'PicoGlitcher')

        # check compatibility
        try:
            pg_fw_version = self.pico_glitcher.get_firmware_version()
            fi_fw_version = list(map(int, version("findus").split('.')))
            print(f"[+] Version of Pico Glitcher: {pg_fw_version}")
            print(f"[+] Version of findus: {fi_fw_version}")
            # check only major and minor version, but not the build number
            if pg_fw_version[:2] != fi_fw_version[:2]:
                raise Exception("Version mismatch")
        except Exception as _:
            print("[-] Fatal error: Versions of findus and Pico Glitcher do not match.")
            print("[*] Update the Pico Glitcher firmware and findus software. See README.md.")
            print("[*] pip install --upgrade findus")
            print("[*] update-fw --port /dev/<rpi-tty-port> --version <pico-glitcher-version>")
            sys.exit(-1)

        if ext_power is not None:
            from findus.ExternalPowerSupply import ExternalPowerSupply
            self.pico_glitcher.disable_vtarget()
            self.power_supply = ExternalPowerSupply(port=ext_power)
            self.power_supply.set_voltage(ext_power_voltage)
            print(self.power_supply.status())
            if enable_vtarget:
                self.power_supply.enable_vtarget()
        else:
            if enable_vtarget:
                self.pico_glitcher.enable_vtarget()
            self.power_supply = None

    def get_power_supply(self):
        """
        To control the external power supply in a script, the `power_supply` object is necessary.

        Returns:
            Returns the `power_supply` object if the external power supply is used.
        """
        return self.power_supply

    def cleanup_pio(self):
        """
        Remove all programs from the internal statemachines. Could be necessary before a program is added to the statemachine but it is out of memory. Some weird behavior was observed when removing and adding programs to the statemachines. Use with caution.
        """
        self.pico_glitcher.cleanup_pio()

    def switch_pio(self, pio_base:int):
        """
        In some rare cases, it might be necessary to switch to the other internal statemachine. For example, if a change in the glitch configuration is necessary but the statemachine is out of memory. Instead of removing the programs from the statemachine (`cleanup_pio`), one can simply switch to the other statemachine and setup the Pico Glitcher to use the configuration on the second statemachine.

        Parameters:
            pio_base: Base number of the statemachine. Can either be 0 or 1. Other values are ignored.
        """
        self.pico_glitcher.switch_pio(pio_base)

    def arm(self, delay:int, length:int, number_of_pulses:int = 1, delay_between:int = 0):
        """
        Arm the Pico Glitcher and wait for the trigger condition. The trigger condition can either be when the reset on the target is released or when a certain pattern is observed in the serial communication.

        Parameters:
            delay: Glitch is emitted after this time. Given in nano seconds. Expect a resolution of about 5 nano seconds.
            length: Length of the glitch in nano seconds. Expect a resolution of about 5 nano seconds.
            number_of_pulses: The number of pulses to emit. This can be used to emit bursts of crowbar glitches.
            delay_between: The delay between each pulse.
        """
        self.pico_glitcher.arm(delay, length, number_of_pulses, delay_between)

    def arm_double(self, delay1:int, length1:int, delay2:int, length2:int):
        """
        Arm the Pico Glitcher and wait for the trigger condition. The trigger condition can either be when the reset on the target is released or when a certain pattern is observed in the serial communication. This functions emits two glitches after a given time, each measured separately from the trigger condition.
        Be sure that `delay2 > delay1 + length1`.

        Parameters:
            delay1: First glitch is emitted after this time. Given in nano seconds. Expect a resolution of about 5 nano seconds.
            length1: Length of the frist glitch in nano seconds. Expect a resolution of about 5 nano seconds.
            delay2: Second glitch is emitted after this time measured from the trigger condition.
            length2: Length of the second glitch in nano seconds.
        """
        self.pico_glitcher.arm_double(delay1, length1, delay2, length2)

    def arm_multiplexing(self, delay:int, mul_config:dict, vinit:str = "config"):
        """
        Arm the Pico Glitcher and wait for the trigger condition. The trigger condition can either be when the reset on the target is released or when a certain pattern is observed in the serial communication. Only available for hardware revision 2 and later.

        Parameters:
            delay: Glitch is emitted after this time. Given in nano seconds. Expect a resolution of about 5 nano seconds.
            mul_config: The dictionary for the multiplexing profile with pairs of identifiers and values. For example, this could be `{"t1": 10, "v1": "GND", "t2": 20, "v2": "1.8", "t3": 30, "v3": "GND", "t4": 40, "v4": "1.8"}`. Meaning that when triggered, a GND-voltage pulse with duration of `10ns` is emitted, followed by a +1.8V step with duration of `20ns` and so on.
            vinit: The initial value of the multiplexer. If `'config'` is chosen, the initial value is read from the configuration file. Additionally, the user can choose between `'VI1'` or `'VI2'`.
        """
        self.pico_glitcher.arm_multiplexing(delay, mul_config, vinit)

    def arm_pulseshaping_from_config(self, delay:int, ps_config:list[list[int]]):
        """
        Arm the Pico Glitcher and wait for the trigger condition. The trigger condition can either be when the reset on the target is released or when a certain pattern is observed in the serial communication. Only available for hardware revision 2 and later. Additionally, the Pulse Shaping Expansion board is needed.

        Parameters:
            delay: Glitch is emitted after this time. Given in nano seconds. Expect a resolution of about 5 nano seconds.
            ps_config: The pulse configuration given as a list of time deltas and voltage values.

        Example:

            ps_config = [[4*length, 1.8], [4*length, 0.95], [length, 0.0]]
            glitcher.arm_pulseshaping_from_config(delay, ps_config)
        """
        return self.pico_glitcher.arm_pulseshaping_from_config(delay, ps_config)

    def arm_pulseshaping_from_spline(self, delay:int, xpoints:list[int], ypoints:list[float]):
        """
        Arm the Pico Glitcher and wait for the trigger condition. The pulse definition is given by time and voltage points. Intermediate values are interpolated.

        Parameters:
            delay: Glitch is emitted after this time. Given in nano seconds. Expect a resolution of about 5 nano seconds.
            xpoints: A list of time points (in nanoseconds) where voltage changes occur.
            ypoints: The corresponding voltage levels at each time point.

        Example:

            xpoints = [0,   100, 200, 300, 400, 500, 515, 520]
            ypoints = [3.0, 2.1, 2.0, 2.0, 1.7, 0.0, 2.0, 3.0]
            glitcher.arm_pulseshaping_from_spline(delay, xpoints, ypoints)
        """
        return self.pico_glitcher.arm_pulseshaping_from_spline(delay, xpoints, ypoints)

    def arm_pulseshaping_from_lambda(self, delay:int, ps_lambda:str, pulse_number_of_points:int):
        """
        Arm the Pico Glitcher and wait for the trigger condition. Generate the pulse from a lambda function depending on the time.

        Parameters:
            delay: Glitch is emitted after this time. Given in nano seconds. Expect a resolution of about 5 nano seconds.
            ps_lambda: A lambda function that defines the glitch at certain times. Must be given as string which is processed by the Pico Glitcher at runtime.
            pulse_number_of_points: The approximate length of the pulse. This is needed to constrain the pulse and to save computing time.

        Example:

            ps_lambda = f"lambda t:-1.0/({2*length})*t+3.0 if t<{2*length} else 2.0 if t<{4*length} else 0.0 if t<{5*length} else 3.0"
            glitcher.arm_pulseshaping_from_lambda(delay, ps_lambda, 6*length)
        """
        return self.pico_glitcher.arm_pulseshaping_from_lambda(delay, ps_lambda, pulse_number_of_points)

    def arm_pulseshaping_from_list(self, delay:int, pulse:list[int]):
        """
        Arm the Pico Glitcher and wait for the trigger condition. Genereate the pulse from a raw array of values.

        Parameters:
            delay: Glitch is emitted after this time. Given in nano seconds. Expect a resolution of about 5 nano seconds.
            pulse: A raw list of points that define the pulse. No calibration and no constraints are applied to the list. The list is forwarded directly to the DAC.

        Example:

            pulse = [-0x1fff] * 50 + [-0x0fff] * 50 + [-0x07ff] * 50 + [0x0000] * 50
            glitcher.arm_pulseshaping_from_list(delay, pulse)
        """
        return self.pico_glitcher.arm_pulseshaping_from_list(delay, pulse)

    def block(self, timeout:float = 1.0):
        """
        Block until trigger condition is met. Raises an exception if times out.
        
        Parameters:
            timeout: Time after the block is released.
        """
        self.pico_glitcher.block(timeout)

    def check_glitch(self) -> bool:
        """
        Check if the glitch was emitted.

        Returns:
            Returns True if statemachine 1, that is used for glitch generation, was triggered.
        """
        return self.pico_glitcher.check_glitch()

    def get_sm1_output(self) -> str:
        return self.pico_glitcher.get_sm1_output()

    def reset_target(self, reset_time:float = 0.2):
        """
        Reset the target via the Pico Glitcher's `RESET` output.

        Parameters:
            reset_time: Time how long the target is held in reset.
        """
        self.pico_glitcher.reset_target(reset_time)

    def reset(self, reset_time:float = 0.2):
        """
        Reset the target via the Pico Glitcher's `RESET` output. This function is the same as `reset_target`. Left in for downward compatibility.
        
        Parameters:
            reset_time: Time how long the target is held in reset.
        """
        self.pico_glitcher.reset_target(reset_time)

    def set_gpio(self, pin_number:int, value:int):
        """
        Set the GPIO pin `pin_number` to a specific output value (0 or 1).

        Parameters:
            pin_number: GPIO pin number (for example 4, 5, 6).
            value: Output value of the GPIO pin (0 or 1).
        """
        self.pico_glitcher.set_gpio(pin_number, value)

    def configure_gpio_out(self, pin_number:int):
        """
        Configure the GPIO pin `pin_number` as an output.

        Parameters:
            pin_number: GPIO pin number (for example 4, 5, 6).
        """
        self.pico_glitcher.configure_gpio_out(pin_number)

    def release_reset(self):
        """
        Release the reset of the target via the Pico Glitcher's `RESET` output.
        """
        self.pico_glitcher.release_reset()

    def initiate_reset(self):
        """
        Initiate the reset of the target via the Pico Glitcher's `RESET` output.
        """
        self.pico_glitcher.initiate_reset()

    def enable_vtarget(self):
        """
        Enable the Pico Glitcher's `VTARGET` output.
        """
        self.pico_glitcher.enable_vtarget()

    def disable_vtarget(self):
        """
        Disable the Pico Glitcher's `VTARGET` output.
        """
        self.pico_glitcher.disable_vtarget()

    def set_mux_voltage(self, voltage:str):
        """
        TODO
        """
        self.pico_glitcher.set_mux_voltage(voltage)

    def power_cycle_target(self, power_cycle_time:float = 0.2):
        """
        Power cycle the target via the Pico Glitcher `VTARGET` output or optionally via the multiplexing stage. Depending on the glitch configuration (crowbar, multiplexing, pulse-shaping), the power-cycle is performed with either the crowbar, multiplexing or pulse-shaping stage.
        If available, target is power-cycled by the external power supply RD6006.
        
        Parameters:
            power_cycle_time: Time how long the power supply is cut. If `ext_power` is defined, the external power supply (RD6006) is cycled.
        """
        if self.power_supply is not None:
            self.power_supply.power_cycle_target(power_cycle_time)
        else:
            self.pico_glitcher.power_cycle_target(power_cycle_time)

    def power_cycle_reset(self, power_cycle_time:float = 0.2):
        """
        Power cycle and reset the target via the Pico Glitcher `VTARGET` and `RESET` output. Optionally the multiplexing stage can be used to power-cycle the target. Can also be used to define sharper trigger conditions via the `RESET` line. Depending on the glitch configuration (crowbar, multiplexing, pulse-shaping), the power-cycle is performed with either the crowbar, multiplexing or pulse-shaping stage.
        
        Parameters:
            power_cycle_time: Time how long the power supply is cut. If `ext_power` is defined, the external power supply is cycled.
        """
        if self.power_supply is not None:
            self.power_supply.disable_vtarget()
            self.pico_glitcher.initiate_reset()
            time.sleep(power_cycle_time)
            self.power_supply.enable_vtarget()
            self.pico_glitcher.release_reset()
        else:
            self.pico_glitcher.power_cycle_reset(power_cycle_time)

    def reset_and_eat_it_all(self, target:serial.Serial, target_timeout:float = 0.3):
        """
        Reset the target via the Pico Glitcher's `RESET` output and flush the serial buffers.
        
        Parameters:
            target: Serial communication object (usually defined as `target = serial.Serial(...)`).
            target_timeout: Time-out of the serial communication. After this time, reading from the serial connection is canceled and it is assumed that there is no more garbage on the line.
        """
        self.pico_glitcher.initiate_reset()
        target.ser.timeout = target_timeout
        target.read(4096)
        target.ser.timeout = target.timeout
        self.pico_glitcher.release_reset()

    def reset_wait(self, target:serial.Serial, token:bytes, reset_time:float = 0.2, debug:bool = False) -> bytes:
        """
        Reset the target via the Pico Glitchers's `RESET` output and wait until the target responds (read from serial).

        Parameters:
            target: Serial communication object (usually defined as `target = serial.Serial(...)`).
            token: Expected response from target. Read from serial multiple times until target responds.
            reset_time:  Time how long the target is held under reset.
            debug: If `true`, more output is given.

        Returns:
            Returns the target's response.
        """
        self.pico_glitcher.initiate_reset()
        time.sleep(reset_time)
        self.pico_glitcher.release_reset()
        response = target.read(4096)
        for _ in range(0, 5):
            if token in response:
                break
            response += target.read(4096)
        if debug:
            for line in response.splitlines():
                print('\t', line.decode())
        return response

    def set_lpglitch(self):
        """
        Enable the low-power crowbar MOSFET for glitch generation.

        The glitch output is an SMA-connected output line that is normally connected to a target's power rails. If this setting is enabled, a low-powered MOSFET shorts the power-rail to ground when the glitch module's output is active.
        """
        self.pico_glitcher.set_lpglitch()

    def set_hpglitch(self):
        """
        Enable the high-power crowbar MOSFET for glitch generation.
        
        The glitch output is an SMA-connected output line that is normally connected to a target's power rails. If this setting is enabled, a high-powered MOSFET shorts the power-rail to ground when the glitch module's output is active.
        """
        self.pico_glitcher.set_hpglitch()
    
    def set_ext_mosfet(self, *pin:int):
        """
        Enable glitch generation on a given GPIO output. Could be used generate glitches by an external MOSFET.

        Parameters:
            pin: Optional GPIO pin to use. Default pin is 19 which is an unbuffered GPIO (recommended for glitch generation). Other options are GPIO pin 16, 17 or 18.
        """
        self.pico_glitcher.set_ext_mosfet(pin)

    def set_multiplexing(self):
        """
        Enables the multiplexing mode of the Pico Glitcher version 2 to quickly switch between different voltage levels.
        """
        self.pico_glitcher.set_multiplexing()

    def set_pulseshaping(self, vinit:float = 1.8):
        """
        Enables the pulse-shaping mode of the Pico Glitcher version 2 to apply a voltage profile to the target's supply voltage.

        Parameters:
            vinit: The initial voltage (voltage offset) to base the calculations on. This does not change the output voltage of the pulse shaping expansion board. However, this parameter is used to calculate the correct offsets and scaling of the pulse.
        """
        self.pico_glitcher.set_pulseshaping(vinit)

    def do_calibration(self, vhigh:float):
        """
        Emit a calibration pulse with the Pico Glitcher Pulse Shaping expansion board to determine `vhigh` and `vlow`. These parameters are used to calculate the offset and gain parameters of the DAC.

        Parameters:
            vhigh: The initial voltage to perform the calibration with. Default is `1V`.
        """
        self.pico_glitcher.do_calibration(vhigh)

    def apply_calibration(self, vhigh:float, vlow:float, store:bool = True):
        """
        Calculate and store the offset and gain parameters that were determined by the calibration routine. These values are stored in `config.json` and must be re-calculated if the config is overwritten.

        Parameters:
            vhigh: The maximum voltage of the calibration voltage trace.
            vlow: The minimum voltage of the calibration voltage trace.
            store: wether to store the offset and gain factor in the Pico Glitcher configuration.
        """
        self.pico_glitcher.apply_calibration(vhigh, vlow, store)

    def tio_trigger(self, pin_trigger:str = "default", edge_type:str = "rising"):
        """
        Configure the Pico Glitcher to trigger on a rising or falling edge on the `TRIGGER` line.

        Parameters:
            pin_trigger: The trigger pin to use. Can either be `'default'` (default `TRIGGER` input) or `'alt'` (alternative trigger input `TRIGGER1`). For hardware version 2 options `'ext1'` or `'ext2'` are also available.
            edge_type: Trigger on a `'rising'` (default) or `'falling'` edge.
        """
        self.pico_glitcher.set_trigger("tio", pin_trigger, edge_type)

    def rising_edge_trigger(self, pin_trigger:str = "default", dead_time:float = 0, pin_condition:str = "default", condition:str = "rising"):
        """
        Configure the Pico Glitcher to trigger on a rising edge on the `TRIGGER` line with optional trigger suppression (dead time).
        
        Parameters:
            pin_trigger: The trigger pin to use. Can either be `'default'` (default `TRIGGER` input) or `'alt'` (alternative trigger input `TRIGGER1`). For hardware version 2 options `'ext1'` or `'ext2'` are also available.
            dead_time: Set a dead time that prohibits triggering within a certain time (trigger rejection). This is intended to exclude false trigger conditions. Can also be set to 0 to disable this feature.
            pin_condition: The rejection time is generated internally by measuring the state of the the given pin of the Pico Glitcher. If you want to trigger on the reset condition, set `pin_condition = 'reset'`, else if you want to trigger on the target power set `pin_condition = 'power'`. `pin_condition` can either be `'default'`, `'power'`, `'reset'` or a GPIO pin number (for example "4", "5" or "6"). If `dead_time` is set to zero and `pin_condition = 'default'`, this parameter is ignored.
            condition: Can either be `'falling'` or `'rising'`. The `dead_time` is measured on the pin `pin_condition` after the specified condition (falling- or rising-edge). For example, a good choice is `'rising'` for the `'default'` configuration and `'falling'` for the `'reset'` configuration. However, this could depend on the specific use case.
        """
        self.pico_glitcher.set_trigger("tio", pin_trigger, "rising")
        self.pico_glitcher.set_dead_zone(dead_time, pin_condition, condition)

    def falling_edge_trigger(self, pin_trigger:str = "default", dead_time:float = 0, pin_condition:str = "default", condition:str = "rising"):
        """
        Configure the Pico Glitcher to trigger on a falling edge on the `TRIGGER` line with optional trigger suppression (dead time).

        Parameters:
            pin_trigger: The trigger pin to use. Can either be `'default'` (default `TRIGGER` input) or `'alt'` (alternative trigger input `TRIGGER1`). For hardware version 2 options `'ext1'` or `'ext2'` are also available.
            dead_time: Set a dead time that prohibits triggering within a certain time (trigger rejection). This is intended to exclude false trigger conditions. Can also be set to 0 to disable this feature.
            pin_condition: The rejection time is generated internally by measuring the state of the the given pin of the Pico Glitcher. If you want to trigger on the reset condition, set `pin_condition = 'reset'`, else if you want to trigger on the target power set `pin_condition = 'power'`. `pin_condition` can either be `'default'`, `'power'`, `'reset'` or a GPIO pin number (for example "4", "5" or "6"). If `dead_time` is set to zero and `pin_condition = 'default'`, this parameter is ignored.
            condition: Can either be `'falling'` or `'rising'`. The `dead_time` is measured on the pin `pin_condition` after the specified condition (falling- or rising-edge). For example, a good choice is `'rising'` for the `'default'` configuration and `'falling'` for the `'reset'` configuration. However, this could depend on the specific use case.
        """
        self.pico_glitcher.set_trigger("tio", pin_trigger, "falling")
        self.pico_glitcher.set_dead_zone(dead_time, pin_condition, condition)

    def uart_trigger(self, pattern:int, baudrate:int = 115200, number_of_bits:int = 8, pin_trigger:str = "default"):
        """
        Configure the Pico Glitcher to trigger when a specific byte pattern is observed on the `TRIGGER` line.
        
        Parameters:
            pattern: Byte pattern that is transmitted on the serial lines to trigger on. For example `0x11`.
            baudrate: The baudrate of the serial communication.
            number_of_bits: The number of bits of the UART payload.
            pin_trigger: The trigger pin to use. Can be either `'default'` or `'alt'`. For hardware version 2 options `'ext1'` or `'ext2'` can also be chosen.
        """
        self.pico_glitcher.set_trigger("uart", pin_trigger)
        self.pico_glitcher.set_baudrate(baudrate)
        self.pico_glitcher.set_number_of_bits(number_of_bits)
        self.pico_glitcher.set_pattern_match(pattern)

    def edge_count_trigger(self, pin_trigger:str = "default", number_of_edges:int = 2, edge_type:str = "rising"):
        """
        Configure the Pico Glitcher to trigger after a certain number of eddges on the `TRIGGER` line.

        Parameters:
            pin_trigger: The trigger pin to use. Can either be `'default'` (default `TRIGGER` input) or `'alt'` (alternative trigger input `TRIGGER1`). For hardware version 2 options `'ext1'` or `'ext2'` are also available.
            number_of_edges: The number of edges after which the Pico Glitcher triggers.
            edge_type: Trigger on a `'rising'` (default) or `'falling'` edge.
        """
        self.pico_glitcher.set_trigger("edge", pin_trigger, edge_type)
        self.pico_glitcher.set_number_of_edges(number_of_edges)

    def set_cpu_frequency(self, frequency:int = 200_000_000):
        """
        Set the CPU frequency of the Raspberry Pi Pico.
        
        Parameters:
            frequency: the CPU frequency.
        """
        self.pico_glitcher.set_frequency(frequency)

    def get_cpu_frequency(self) -> int:
        """
        Get the current CPU frequency of the Raspberry Pi Pico.
        
        Returns:
            Returns the CPU frequency.
        """
        return self.pico_glitcher.get_frequency()

    def change_config_and_reset(self, key:str, value:int|float|str):
        """
        Change the content of the configuration file `config.json`. Note that the value to be changed must already exist. After calling this function, the Pico Glitcher must be re-initialized (call `glitcher.init(port=args.rpico, ext_power=args.power, ext_power_voltage=3.3)` again).

        Parameters:
            key: Key of value to be replaced.
            value: Value to be set.
        """
        return self.pico_glitcher.change_config_and_reset(key, value)

    def change_config_and_apply(self, key:str, value:int|float|str):
        """
        Change the content of the configuration file `config.json`. Note that the value to be changed must already exist. Apply the values afterwards without reset by calling `glitcher.switch_pio(1)`. This will re-initialize the internal statemachines and apply the configuration.

        Parameters:
            key: Key of value to be replaced.
            value: Value to be set.
        """
        return self.pico_glitcher.change_config_and_apply(key, value)

    def waveform_generator(self, frequency:int, gain:float, waveid:int):
        """
        The Pulse Shaping expansion board of the Pico Glitcher v2 can be used to generate arbitrary and continous waveforms as well.

        Parameters:
            frequency: The frequency of the signal.
            gain: The gain (overall amplitude) of the signal.
            waveid: This determines the signal type, that is, what signal should be generated.

        - sine wave: `waveid = 0`
        - cosine wave: `waveid = 1`
        - triangle: `waveid = 2`
        - positive sawtooth: `waveid = 3`
        - negative sawtooth: `waveid = 4`
        """
        self.pico_glitcher.waveform_generator(frequency, gain, waveid)

    def arm_adc(self):
        """
        Arm the ADC on pin 26 and capture ADC samples if the trigger condition is met. On Pico Glitcher hardware version 1, the separate SMA connector labeled `Analog` can be used to measure analog voltage traces. On revision 2, the analog input is directly connected to the `GLITCH` line.
        """
        self.pico_glitcher.arm_adc()

    def get_adc_samples(self, timeout:float = 1.0) -> list[int]:
        """
        Read back the captured ADC samples.
        """
        samples = self.pico_glitcher.get_adc_samples(timeout)
        #print(samples)
        decoded_str = samples.decode().strip()
        num_str = decoded_str.split("[")[1].split("]")[0]
        int_list = [int(x) for x in num_str.split(",")]
        return int_list

    def configure_adc(self, number_of_samples:int = 1024, sampling_freq:int = 500_000):
        """
        Configure the onboard ADC of the Pico Glitcher.

        Parameters:
            number_of_samples: The number of samples to capture after triggering.
            sampling_freq: The sampling frequency of the ADC. `500 kSPS` is the maximum for the Pico Glitcher.
        """
        self.pico_glitcher.configure_adc(number_of_samples, sampling_freq)

    def hard_reset(self):
        """
        Perform a hard reset of the Pico Glitcher (Raspberry Pi Pico).
        """
        try:
            self.pico_glitcher.hard_reset()
        except Exception as _:
            pass

class Helper():
    """
    Helper class that provides useful functions.
    Example usage:
    
        from findus import Helper as helper
        filename = f"{helper.timestamp()}_memory_dump.bin"

    Methods:
        timestamp: Provides the current timestamp in a file-friendly format.
    """
    @staticmethod
    def timestamp() -> str:
        """
        Provides the current timestamp in a file-friendly format.
        
        Returns:
            Returns the current timestamp in the format %Y-%m-%d_%H-%M-%S.
        """
        return datetime.datetime.now().strftime("%Y-%m-%d_%H-%M-%S")

    @staticmethod
    def linspace(start, stop, num, endpoint=True) -> list:
        """
        Generate equidistant points from a start to a stop point. Equivalent to numpy's linspace function.

        Parameters:
            start: Start point of the interval.
            stop: End point of the interval.
            num: Number of points to divide the interval into.
            endpoint: Whether the stop point should be part of the interval.

        Returns:
            List of integer or real numbers.
        """
        if num <= 0:
            return []
        if endpoint:
            step = (stop - start) / (num - 1)
        else:
            step = (stop - start) / num
        return [start + i * step for i in range(num)]

    @staticmethod
    def arange(start, stop=None, step=1.0) -> list:
        """
        Return evenly spaced values within a given interval. Equivalent to numpy's arange function.

        Parameters:
            start: Start of interval. The interval includes this value. The default start value is 0.
            stop: End of interval. The interval does not include this value, except in some cases where step is not an integer and floating point round-off affects the length of out.
            step: Spacing between values. For any output out, this is the distance between two adjacent values, `out[i+1] - out[i]`. The default step size is 1. If step is specified as a position argument, start must also be given.

        Returns:
            List of integer or real numbers.
        """
        if stop is None:  # If only one argument is provided, treat it as stop
            stop = start
            start = 0.0
        if step == 0:
            raise ValueError("step argument must not be zero")
        result = []
        i = start
        if step > 0:
            while i < stop:
                result.append(round(i, 10))  # Rounding to avoid floating-point precision issues
                i += step
        else:
            while i > stop:
                result.append(round(i, 10))
                i += step
        return result

    @staticmethod
    def random_point(a, b, stride=0, dtype=int):
        points = None
        if a == b:
            return a
        if stride > (b - a):
            raise ValueError("Stride is larger than the interval length.")
        elif stride == 0:
            points = Helper.arange(a, b + 1)
        else:
            points = Helper.arange(a, b + stride, stride)
        choice = random.choice(points)
        return dtype(choice)

    @staticmethod
    def range(start, end, step=1):
        if start == end:
            return [start]
        else:
            return Helper.arange(start, end + step, step)

class ErrorHandling():
    def __init__(self, max_fails:int = 10, look_back:int = 30, database:Database = None):
        self.successive_fails = 0
        self.fail_gate_open = False
        self.fail_gate_close = 0
        self.max_fails = max_fails
        self.look_back = look_back
        if self.max_fails > self.look_back:
            self.look_back = self.max_fails
        self.database = database

    def exit_action(self):
        # can be overwritten to suit specific needs
        print("[-] Successive error occurred. Exiting.")
        sys.exit(-1)

    def check(self, experiment_id:int, response:bytes, expected:bytes = b'expected', keep:list[bytes] = None, user_action = None, recolor:str = 'O'):
        """
        Check for consecutive errors and act accordingly.

        Parameters:
            experiment_id: The current experiment id.
            response: Response of the current experiment id.
            expected: The expected response. Everything else is considered erroneous.
            keep: List of characterization to keep. For example `keep = [b'ok', b'success']`.
            user_action: Function to execute in the case of consecutive errors. Could be a function to reprogram the target, for example.

        Returns:
            Returns the response. If a consecutive error is detected, `b'error: successive error occurred'` is returned.
        """
        # exit if too many successive fails (including a supposedly successful memory read)
        # open fail gate, if error occurred and everything was ok previously
        if expected not in response and not self.fail_gate_open:
            self.fail_gate_open = True
            self.fail_gate_close = experiment_id + self.look_back
            self.successive_fails = 0

        # if fail gate open and error occurred, increase the fail count
        if expected not in response and self.fail_gate_open:
            self.successive_fails += 1

        # close fail gate after max_fails more experiments and check result
        if  experiment_id >= self.fail_gate_close and self.fail_gate_open:
            self.fail_gate_open = False
            if self.successive_fails >= self.max_fails:

                # delete the erroneous data points
                # last_good: last "good" experiment with expected characterization
                # last_good + 1: first erroneous experiment of consecutive erroneous events. We want to keep this in order to observe what happened.
                # last_good + 2: second erroneous experiment. Everything after this is removed from the database. This experiment is overwritten by an experiment with characterization `b'error: successive error occurred'`
                if self.database is not None:
                    print("Successive error occurred:")
                    last_good = experiment_id - self.look_back

                    # since the fail gate could start outside the successive fail range, we have to look back twice
                    for eid in reversed(range(experiment_id - 2 * self.look_back, experiment_id + 1)):
                        par = self.database.get_parameters_of_experiment_rel(eid)
                        res = par[-1]
                        if res is not None and expected in res:
                            last_good = eid
                            break

                    # search from last_good to experiment_id for the first erroneous experiment with characterization we want to keep
                    if keep is not None:
                        break_flag = False
                        for eid in range(last_good, experiment_id + 1):
                            par = self.database.get_parameters_of_experiment_rel(eid)
                            res = par[-1]
                            for characterization_to_keep in keep:
                                if characterization_to_keep in res:
                                    last_good = eid - 1
                                    break_flag = True
                                    break
                            if break_flag:
                                break

                    # remove everything expect the first erroneous experiment
                    for eid in range(last_good + 2, experiment_id + 1):
                        print(f"Removing experiment {eid} from database")
                        self.database.remove_rel(eid)

                    # get parameters of first erroneous experiment and store this event in database with extra classification
                    parameters = self.database.get_parameters_of_experiment_rel(last_good + 1)
                    response = b'error: successive error occurred'
                    try:
                        parameters = (last_good + 2, ) + parameters[1:-2] + (recolor, response)
                        self.database.insert(*parameters)
                    except Exception as _:
                        pass
                
                # execute user action
                if user_action is None:
                    self.exit_action()
                else:
                    user_action()
                self.successive_fails = 0

            return response
