MKesenheimer/fault-injection-library/findus/firmware/PicoGlitcher.py

# Copyright (C) 2024 Dr. Matthias Kesenheimer - All Rights Reserved.
# You may use, distribute and modify this code under the terms of the GPL3 license.
#
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
"""
This is the documentation of the PicoGlitcher module and all its classes.

Upload this module onto your Pico Glitcher. The classes and methods will become available through the pyboard interface.
"""

import machine
from rp2 import PIO
from machine import Pin
import time
import ujson
from FastADC import FastADC
import AD910X
from PulseGenerator import PulseGenerator
import Globals
import sys
import Statemachines

class PicoGlitcher():
    """
    Class that contains the code to access the hardware of the Pico Glitcher.
    """
    def __init__(self):
        """
        Default constructor.
        Initializes the Pico Glitcher with the default configuration.
        - Disables `VTARGET`
        - Enables the low-power MOSFET for glitching
        - Configures the Pico Glitcher to use the rising-edge triggger condition.
        """
        self.init()

    def init(self):
        self.sm0 = PIO(0).state_machine(0)
        self.sm1 = PIO(0).state_machine(1)
        self.sm2 = PIO(0).state_machine(2)
        self.cleanup_pio()
        self.frequency = None
        self.trigger_mode = "tio"
        self.glitch_mode = "crowbar"
        self.baudrate = 115200
        self.number_of_bits = 8
        self.armed = False

        # read config
        with open("config.json", "r") as file:
            self.config = ujson.load(file)

        if self.config["hardware_version"][0] == 1:
            # overclocking supposedly works, script runs also with 270_000_000
            self.set_frequency(200_000_000)
        elif self.config["hardware_version"][0] >= 2:
            self.set_frequency(250_000_000)
        # LED
        self.led = Pin("LED", Pin.OUT)
        self.led.low()
        if (self.config["hardware_version"][0] == 2 and self.config["hardware_version"][1] >= 3) or self.config["hardware_version"][0] == 3:
            # VTARGET_EN (active high) for v2.3 and higher
            self.pin_vtarget_en = Pin(Globals.VTARGET_EN, Pin.OUT, Pin.PULL_DOWN)
            self.vtarget_enable_value = 1
            self.vtarget_disable_value = 0
        elif (self.config["hardware_version"][0] == 2 and self.config["hardware_version"][1] < 3) or self.config["hardware_version"][0] == 1:
            # VTARGET_EN (active low) for 2.2 and lower
            self.pin_vtarget_en = Pin(Globals.VTARGET_EN, Pin.OUT, Pin.PULL_UP)
            self.vtarget_enable_value = 0
            self.vtarget_disable_value = 1
        else:
            raise Exception(f"Hardware version {self.config['hardware_version']} not implemented.")
        self.pin_vtarget_en.value(self.vtarget_disable_value)
        # RESET
        self.pin_reset = Pin(Globals.RESET, Pin.OUT, Pin.PULL_UP)
        self.pin_reset.low()
        # GLITCH_EN
        self.pin_glitch_en = Pin(Globals.GLITCH_EN, Pin.OUT, Pin.PULL_DOWN)
        self.pin_glitch_en.low()
        # TRIGGER
        self.pin_trigger = Pin(Globals.TRIGGER, Pin.IN)
        self.trigger_inverting = False
        # HP_GLITCH
        self.pin_hpglitch = Pin(Globals.HP_GLITCH, Pin.OUT, Pin.PULL_DOWN)
        self.pin_hpglitch.low()
        # LP_GLITCH
        self.pin_lpglitch = Pin(Globals.LP_GLITCH, Pin.OUT, Pin.PULL_DOWN)
        self.pin_lpglitch.low()
        # which glitching transistor to use. Default: lpglitch
        self.pin_glitch = self.pin_lpglitch
        # standard dead zone after power down
        self.dead_time = 0.0
        self.pin_condition = self.pin_glitch_en
        self.condition = "rising"
        self.number_of_edges = 1
        # analog digital converter
        self.fastadc = FastADC()
        self.fastsamples = self.fastadc.init_array()
        self.adc_samples_captured = False
        # gpio outputs (are configured later as required)
        self.pin_gpios = {}
        # pins for multiplexing and pulse-shaping (only hardware version 2 and later)
        if self.config["hardware_version"][0] >= 2:
            self.pin_mux1 = Pin(Globals.MUX1, Pin.OUT, Pin.PULL_DOWN)
            self.pin_mux0 = Pin(Globals.MUX0, Pin.OUT, Pin.PULL_DOWN)
            self.pin_mux1.value(Globals.MUX1_INIT)
            self.pin_mux0.value(Globals.MUX0_INIT)
            # msb: GPIO0 -> MUX1
            # lsb: GPIO1 -> MUX0
            # 0b00: VI1
            # 0b10: VI2
            # 0b01: +1V8
            # 0b11: GND
            self.voltage_map = {"VI1": 0b00, "VI2": 0b10, "1.8": 0b01, "GND": 0b11, "3.3": 0b10, "VCC": 0b00}
            # Pulse shaping expansion board related stuff
            self.ad910x = AD910X.AD910X()
            self.ad910x.reset()
            self.ad910x.init()
            self.pin_ps_trigger = self.ad910x.get_trigger_pin()
            self.pulse_generator = PulseGenerator(vhigh=self.config["ps_offset"], factor=self.config["ps_factor"])

    def switch_pio(self, pio_base):
        self.sm0 = PIO(pio_base).state_machine(0)
        self.sm1 = PIO(pio_base).state_machine(1)
        self.sm2 = PIO(pio_base).state_machine(2)

    def waveform_generator(self, frequency:int = AD910X.DEFAULT_FREQUENCY, gain:float = AD910X.DEFAULT_GAIN, waveid:int = AD910X.WAVE_TRIANGLE):
        if self.config["hardware_version"][0] < 2:
            raise Exception("Pulse-shaping not implemented in hardware version 1.")
        if waveid < AD910X.WAVE_SINE or waveid > AD910X.WAVE_NEGATIVE_SAWTOOTH:
            raise Exception("Wave-id not supported. Choose one of [0, 1, 2, 3, 4].")
        self.ad910x.set_frequency(frequency)
        self.ad910x.set_gain(gain)
        self.ad910x.set_wave_output(waveid)

    def get_firmware_version(self) -> list[int]:
        """
        Get the current firmware version. Can be used to check if the current version is compatible with findus.

        Returns:
            Returns the current firmware version.
        """
        print(self.config["software_version"])
        return self.config["software_version"]

    def set_frequency(self, frequency:int = 200_000_000):
        """
        Set the CPU frequency of the Raspberry Pi Pico.
        
        Parameters:
            frequency: the CPU frequency.
        """
        machine.freq(frequency)
        self.frequency = machine.freq()

    def get_frequency(self) -> int:
        """
        Get the current CPU frequency of the Raspberry Pi Pico.
        
        Returns:
            Returns the CPU frequency.
        """
        print(machine.freq())
        return machine.freq()

    def set_trigger(self, mode:str = "tio", pin_trigger:str = "default", edge_type:str = "rising"):
        """
        Configures the Pico Glitcher which triggger mode to use.
        In "tio"-mode, the Pico Glitcher triggers on a rising edge on the `TRIGGER` pin.
        If "uart"-mode is chosen, the Pico Glitcher listens on the `TRIGGER` pin and triggers if a specific byte pattern in the serial communication is observed. In "edge"-mode, the Pico Glitcher counts the number of edges and triggers if a certain number of edges were observed. The parameter `edge_type` should be ignored if "uart"-mode is selected.

        Parameters:
            mode: The trigger mode to use. Either "tio" or "uart".
            pin_trigger: The trigger pin to use. Can be either "default" or "alt". For hardware version 2 options "ext1" or "ext2" can also be chosen.
            edge_type: Trigger on the "rising" (default) or "falling" edge.
        """
        self.trigger_mode = mode
        if pin_trigger == "default":
            self.pin_trigger = Pin(Globals.TRIGGER, Pin.IN)
            if edge_type == "rising":
                self.trigger_inverting = False
            else:
                self.trigger_inverting = True
        elif pin_trigger == "alt":
            self.pin_trigger = Pin(Globals.ALT_TRIGGER, Pin.IN)
            if edge_type == "rising":
                self.trigger_inverting = False
            else:
                self.trigger_inverting = True
        elif pin_trigger == "ext1":
            self.pin_trigger = Pin(Globals.EXT1, Pin.IN)
            if edge_type == "rising":
                self.trigger_inverting = True
            else:
                self.trigger_inverting = False
        elif pin_trigger == "ext2":
            self.pin_trigger = Pin(Globals.EXT2, Pin.IN)
            if edge_type == "rising":
                self.trigger_inverting = True
            else:
                self.trigger_inverting = False

    def set_number_of_edges(self, number_of_edges:int = 2):
        """
        Set the number of edges after which the Pico Glitcher triggers in edge-counting trigger mode.

        Parameters:
            number_of_edges: The number of edges after which the Pico Glitcher triggers.
        """
        self.number_of_edges = number_of_edges

    def set_baudrate(self, baud:int = 115200):
        """
        Set the baudrate of the UART communication in UART-trigger mode.

        Parameters:
            baud: The baudrate to use.
        """
        self.baudrate = baud

    def set_number_of_bits(self, number_of_bits:int = 8):
        """
        Set the number of bits of the UART communication in UART-trigger mode.
        
        Parameters:
            number_of_bits: The number of bits of the UART payload to use.
        """
        self.number_of_bits = number_of_bits

    def set_pattern_match(self, pattern:int):
        """
        Configure the Pico Glitcher to trigger when a specific byte pattern is observed on the RX line (`TRIGGER` pin).

        Parameters:
            pattern: Byte pattern that is transmitted on the serial lines to trigger on. For example `0x11`.
        """
        self.pattern = pattern

    def enable_vtarget(self):
        """
        Enable `VTARGET` output. Activates the Pico Glitcher's power supply for the target.
        """
        self.pin_vtarget_en.value(self.vtarget_enable_value)

    def disable_vtarget(self):
        """
        Disables `VTARGET` output. Disables the Pico Glitcher's power supply for the target.
        """
        self.pin_vtarget_en.value(self.vtarget_disable_value)

    def __ps_power_cycle(self, power_cycle_time:float):
        if self.sm0 is not None:
            # deactivate any statemachine that has access to the ps_trigger pin
            self.sm0.active(0)
            # take control over the pins
            self.pin_ps_trigger = self.ad910x.init_trigger_pin()
        self.ad910x.set_pulse_output_continous()
        value = self.pulse_generator.get_value(0)
        self.ad910x.set_const(value, 100)
        self.ad910x.update_sram(1)
        self.pin_ps_trigger.low()
        time.sleep(power_cycle_time)
        self.pin_ps_trigger.high()
        self.ad910x.set_pulse_output_oneshot()

    def __mux_power_cycle(self, power_cycle_time:float):
        if self.sm0 is not None:
            # deactivate any statemachine that has access to the multiplexer
            self.sm0.active(0)
            #PIO(0).remove_program() # not necessary
            # take control over the pins
            self.pin_mux1 = Pin(Globals.MUX1, Pin.OUT, Pin.PULL_DOWN)
            self.pin_mux0 = Pin(Globals.MUX0, Pin.OUT, Pin.PULL_DOWN)
        # pull the multiplexer to GND
        self.pin_mux1.value(1)
        self.pin_mux0.value(1)
        time.sleep(power_cycle_time)
        # enable power
        self.pin_mux1.value(Globals.MUX1_INIT)
        self.pin_mux0.value(Globals.MUX0_INIT)

    def set_mux_voltage(self, voltage:str = "GND"):
        if self.sm0 is not None:
            # deactivate any statemachine that has access to the multiplexer
            self.sm0.active(0)
            # take control over the pins
            self.pin_mux1 = Pin(Globals.MUX1, Pin.OUT, Pin.PULL_DOWN)
            self.pin_mux0 = Pin(Globals.MUX0, Pin.OUT, Pin.PULL_DOWN)
        if voltage == "GND":
            self.pin_mux1.value(1)
            self.pin_mux0.value(1)
        elif voltage == "VI1" or voltage == "VCC":
            self.pin_mux1.value(0)
            self.pin_mux0.value(0)
        elif voltage == "1.8":
            self.pin_mux1.value(1)
            self.pin_mux0.value(0)
        else: # 3.3 or VI2
            self.pin_mux1.value(0)
            self.pin_mux0.value(1)

    def power_cycle_target(self, power_cycle_time:float = 0.2):
        """
        Power cycle the target via the Pico Glitcher `VTARGET` output.
        
        Parameters:
            power_cycle_time: Time how long the power supply is cut.
        """
        if self.glitch_mode == "mul":
            if self.armed:
                raise Exception("Error: Power-cycling with multiplexing stage not possible when armed.")
            self.__mux_power_cycle(power_cycle_time)
        elif self.glitch_mode == "pul":
            if self.armed:
                raise Exception("Error: Power-cycling with pulse-shaping stage not possible when armed.")
            self.__ps_power_cycle(power_cycle_time)
        else:
            # power-cycling in "normal" mode
            self.disable_vtarget()
            time.sleep(power_cycle_time)
            self.enable_vtarget()

    def power_cycle_reset(self, power_cycle_time:float = 0.2):
        """
        Power cycle and reset the target via the Pico Glitcher `VTARGET` and `RESET` output. Optionally the multiplexing stage can be used to power-cycle the target. Can also be used to define sharper trigger conditions via the `RESET` line.

        Parameters:
            power_cycle_time: Time how long the power supply is cut. If `ext_power` is defined, the external power supply is cycled.
        """
        if self.glitch_mode == "mul":
            if self.armed:
                raise Exception("Error: Power-cycling with multiplexing stage not possible when armed.")
            self.initiate_reset()
            self.__mux_power_cycle(power_cycle_time)
            self.release_reset()
        elif self.glitch_mode == "pul":
            if self.armed:
                raise Exception("Error: Power-cycling with pulse-shaping stage not possible when armed.")
            self.initiate_reset()
            self.__ps_power_cycle(power_cycle_time)
            self.release_reset()
        else:
            # power-cycling in "normal" mode
            self.disable_vtarget()
            self.initiate_reset()
            time.sleep(power_cycle_time)
            self.enable_vtarget()
            self.release_reset()

    def initiate_reset(self):
        """
        Reset the target via the Pico Glitcher's `RESET` output.
        """
        self.pin_reset.low()

    def release_reset(self):
        """
        Release the reset on the target via the Pico Glitcher's `RESET` output.
        """
        self.pin_reset.high()

    def reset_target(self, reset_time:float = 0.01):
        """
        Reset the target via the Pico Glitcher's `RESET` output, release the reset on the target after a certain time.
        
        Parameters:
            reset_time: Time how long the target is held in reset.
        """
        self.initiate_reset()
        time.sleep(reset_time)
        self.release_reset()

    def configure_gpio_out(self, pin_number:int):
        # TODO: check if pin is already in use
        self.pin_gpios[pin_number] = Pin(pin_number, Pin.OUT, Pin.PULL_DOWN)

    def set_gpio(self, pin_number:int, value:int):
        try:
            self.pin_gpios[pin_number].value(value)
        except KeyError:
            self.configure_gpio_out(pin_number)
            self.pin_gpios[pin_number].value(value)

    def set_lpglitch(self):
        """
        Enable the low-power crowbar MOSFET for glitch generation.

        The glitch output is an SMA-connected output line that is normally connected to a target's power rails. If this setting is enabled, a low-powered MOSFET shorts the power-rail to ground when the glitch module's output is active.
        """
        self.glitch_mode = "crowbar"
        self.pin_glitch = self.pin_lpglitch

    def set_hpglitch(self):
        """
        Enable the high-power crowbar MOSFET for glitch generation.

        The glitch output is an SMA-connected output line that is normally connected to a target's power rails. If this setting is enabled, a low-powered MOSFET shorts the power-rail to ground when the glitch module's output is active.
        """
        self.glitch_mode = "crowbar"
        self.pin_glitch = self.pin_hpglitch

    def set_ext_mosfet(self, pin=Globals.EXT_GLITCH):
        """
        Enable the external mosfet triggering on GPIO19
        """
        self.pin_ext_mosfet = Pin(pin, Pin.OUT, Pin.PULL_DOWN)
        self.pin_ext_mosfet.low()
        self.glitch_mode = "crowbar"
        self.pin_glitch = self.pin_ext_mosfet

    def set_multiplexing(self):
        """
        Enables the multiplexing mode of the Pico Glitcher version 2 to switch between different voltage levels.
        """
        if self.config["hardware_version"][0] < 2:
            raise Exception("Multiplexing not implemented in hardware version 1.")
        self.glitch_mode = "mul"
        self.pin_glitch = self.pin_mux1

    def set_pulseshaping(self, vinit=1.8):
        """
        Enables the pulse-shaping mode of the Pico Glitcher version 2 to emit a pre-defined voltage pulse on the Pulse Shaping expansion board.
        """
        if self.config["hardware_version"][0] < 2:
            raise Exception("Pulse-shaping not implemented in hardware version 1.")
        self.glitch_mode = "pul"
        self.pin_glitch = self.pin_ps_trigger

        # Configure the AD9102
        self.pulse_generator.set_offset(vinit)
        self.ad910x.set_frequency(self.pulse_generator.get_frequency())
        self.ad910x.set_gain(1.5)
        # configure the AD9102 to emit an oneshot pulse
        self.ad910x.set_pulse_output_oneshot()

    def do_calibration(self, vhigh:float):
        """
        Emit a calibration pulse with that can be used to determine `vhigh` and `vlow`. These parameters are used to calculate the offset and gain parameters of the DAC.

        Parameters:
            vhigh: The initial voltage to perform the calibration with. Default is `1V`.
        """
        self.set_pulseshaping(vhigh)
        pulse = self.pulse_generator.calibration_pulse()
        self.__arm_pulseshaping(delay=100, pulse=pulse)
        self.reset_target(0.01)

    def apply_calibration(self, vhigh:float, vlow:float, store:bool = True):
        """
        Calculate and store the offset and gain parameters that were determined by the calibration routine. These values are stored in `config.json` and must be re-calculated if the config is overwritten.

        Parameters:
            vhigh: The maximum voltage of the calibration voltage trace.
            vlow: The minimum voltage of the calibration voltage trace.
            store: wether to store the offset and gain factor in the Pico Glitcher configuration.
        """
        factor = 1/(vhigh - vlow)
        self.pulse_generator.set_calibration(vhigh, factor)
        if store:
            self.__change_config("ps_offset", vhigh)
            self.__change_config("ps_factor", factor)

    def set_dead_zone(self, dead_time:float = 0, pin_condition:str = "default", condition:str = "rising"):
        """
        Set a dead time that prohibits triggering within a certain time (trigger rejection). This is intended to exclude false trigger conditions. Can also be set to 0 to disable this feature.
        
        Parameters:
            dead_time: Rejection time during triggering is disabled.
            pin_condition: Can either be "default", "power", "reset" or a GPIO pin number (for example "4", "5" or "6"). In "power" mode, the `TRIGGER` input is connected to the target's power and the rejection time is measured after power down. In "reset" mode, the `TRIGGER` input is connected to the `RESET` line and the rejection time is measured after the device is reset. These modes imply different internal conditions to configure the dead time. If "default" is chosen, effectively no dead time is active.
            condition: Can either be "falling" or "rising". The `dead_time` is measured on the pin `pin_condition` after the specified condition (falling- or rising-edge). For example, a good choice is "rising" for the "default" configuration and "falling" for the "reset" configuration. However, this could depend on the specific use case.
        """
        if pin_condition == "default":
            self.pin_condition = self.pin_glitch_en
        elif pin_condition == "power":
            self.pin_condition = self.pin_vtarget_en
        elif pin_condition == "reset":
            self.pin_condition = self.pin_reset
        elif pin_condition.isdigit():
            pin_number = int(pin_condition)
            self.configure_gpio_out(pin_number)
            self.pin_condition = self.pin_gpios[pin_number]
        #print(f"self.pin_condition = {self.pin_condition}")
        self.dead_time = dead_time
        self.condition = condition

    def cleanup_pio(self):
        if self.sm0 is not None:
            self.sm0.active(0)
            self.sm0.irq(handler=None)
            while self.sm0.rx_fifo() != 0:
                self.sm0.get()
        if self.sm1 is not None:
            self.sm1.active(0)
            self.sm1.irq(handler=None)
            while self.sm1.rx_fifo() != 0:
                self.sm1.get()
        if self.sm2 is not None:
            self.sm2.active(0)
            self.sm2.irq(handler=None)
            while self.sm2.rx_fifo() != 0:
                self.sm2.get()
        PIO(0).remove_program()
        PIO(1).remove_program()

    def __arm_common(self):
        self.sm1.active(0)
        self.sm2.active(0)
        if self.trigger_mode == "tio":
            sm1_func = None
            if not self.trigger_inverting:
                sm1_func = Statemachines.tio_trigger_with_dead_time_rising_edge
            else:
                sm1_func = Statemachines.tio_trigger_with_dead_time_falling_edge
            # state machine that checks the trigger condition
            self.sm1.init(sm1_func, freq=self.frequency, in_base=self.pin_trigger)
            # state machine that blocks for a specific time after a certain condition (dead time)
            sm2_func = None
            if self.condition == "rising":
                sm2_func = Statemachines.block_rising_condition
            else:
                sm2_func = Statemachines.block_falling_condition
            self.sm2.init(sm2_func, freq=self.frequency, in_base=self.pin_condition)
            # push dead time (in seconds) into the fifo of the statemachine
            self.sm2.put(int(self.dead_time * self.frequency))
            self.sm1.active(1)
            self.sm2.active(1)

        elif self.trigger_mode == "edge":
            sm1_func = None
            if not self.trigger_inverting:
                sm1_func = Statemachines.edge_trigger_rising_edge
            else:
                sm1_func = Statemachines.edge_trigger_falling_edge
            # state machine that checks the trigger condition
            self.sm1.init(sm1_func, freq=self.frequency, in_base=self.pin_trigger)
            self.sm1.put(self.number_of_edges - 1)
            self.sm1.active(1)

        elif self.trigger_mode == "uart":
            # state machine that checks the trigger condition
            self.sm1.init(Statemachines.uart_trigger, freq=self.baudrate * 8, in_base=self.pin_trigger)
            # push pattern into the fifo of the statemachine
            pattern = self.pattern << (32 - self.number_of_bits)
            self.sm1.put(pattern)
            # push number of bits into the fifo of the statemachine (self.number_of_bits - 1 is an optimization here)
            self.sm1.put(self.number_of_bits - 1)
            self.sm1.active(1)

        self.armed = True
        self.sm0.active(1)

    def arm(self, delay:int, length:int, number_of_pulses:int = 1, delay_between:int = 0):
        """
        Arm the Pico Glitcher and wait for the trigger condition. The trigger condition can either be when the reset on the target is released or when a certain pattern is observed in the serial communication.

        Parameters:
            delay: Glitch is emitted after this time. Given in nano seconds. Expect a resolution of about 5 nano seconds.
            length: Length of the glitch in nano seconds. Expect a resolution of about 5 nano seconds.
            number_of_pulses: The number of pulses to emit. This can be used to emit bursts of crowbar glitches.
            delay_between: The delay between each pulse.
        """
        self.sm0.active(0)
        if number_of_pulses == 1:
            # state machine that emits the glitch if the trigger condition is met
            self.sm0.init(Statemachines.glitch, freq=self.frequency, set_base=self.pin_glitch, sideset_base=self.pin_glitch_en)
            # push delay and length (in nano seconds) into the fifo of the statemachine
            self.sm0.put(int(delay) // (1_000_000_000 // self.frequency))
            self.sm0.put(int(length) // (1_000_000_000 // self.frequency))
        elif number_of_pulses > 1:
            # state machine that emits the glitch if the trigger condition is met
            self.sm0.init(Statemachines.glitch_burst, freq=self.frequency, set_base=self.pin_glitch, sideset_base=self.pin_glitch_en)
            # push delay and length (in nano seconds) into the fifo of the statemachine
            self.sm0.put(int(delay) // (1_000_000_000 // self.frequency))
            pulse_length = int(length) // (1_000_000_000 // self.frequency)
            delay_between = int(delay_between) // (1_000_000_000 // self.frequency)
            config = delay_between << 16 | pulse_length
            self.sm0.put(config)
            self.sm0.put(number_of_pulses - 1)

        # call common arm function
        self.__arm_common()

    def arm_double(self, delay1:int, length1:int, delay2:int, length2:int):
        """
        Arm the Pico Glitcher and wait for the trigger condition. The trigger condition can either be when the reset on the target is released or when a certain pattern is observed in the serial communication. This functions emits two glitches after a given time, each measured separately from the trigger condition.
        Be sure that `delay2 > delay1 + length1`.

        Parameters:
            delay1: First glitch is emitted after this time. Given in nano seconds. Expect a resolution of about 5 nano seconds.
            length1: Length of the frist glitch in nano seconds. Expect a resolution of about 5 nano seconds.
            delay2: Second glitch is emitted after this time measured from the trigger condition.
            length2: Length of the second glitch in nano seconds.
        """
        if delay2 <= delay1 + length1:
            raise Exception("Second glitch collides with first one; delay2 too short.")

        # make delay2 relative to delay1 + length1
        delay2 = delay2 - (delay1 + length1)

        self.sm0.active(0)
        # state machine that emits the glitch if the trigger condition is met
        self.sm0.init(Statemachines.glitch_multiple, freq=self.frequency, set_base=self.pin_glitch, sideset_base=self.pin_glitch_en)
        pulse1_length = int(length1) // (1_000_000_000 // self.frequency)
        pulse1_delay = int(delay1) // (1_000_000_000 // self.frequency)
        pulse2_length = int(length2) // (1_000_000_000 // self.frequency)
        pulse2_delay = int(delay2) // (1_000_000_000 // self.frequency)

        if pulse1_length > 2**10 or pulse2_length > 2**10:
            raise Exception("Pulse length exceeds maximum value.")
        if pulse1_delay > 2**22 or pulse2_delay > 2**22:
            raise Exception("Pulse delay exceeds maximum value.")

        config1 = pulse1_length << 22 | pulse1_delay
        config2 = pulse2_length << 22 | pulse2_delay
        number_of_pulses = 2
        self.sm0.put(number_of_pulses - 1)
        self.sm0.put(config1)
        self.sm0.put(config2)

        self.__arm_common()

    def arm_multiplexing(self, delay:int, mul_config:dict, vinit:str = "config"):
        """
        Arm the Pico Glitcher in multiplexing mode and wait for the trigger condition.

        Parameters:
            delay: Glitch is emitted after this time. Given in nano seconds. Expect a resolution of about 5 nano seconds.
            mul_config: The dictionary for the multiplexing profile with pairs of identifiers and values. For example, this could be `{"t1": 10, "v1": "GND", "t2": 20, "v2": "1.8", "t3": 30, "v3": "GND", "t4": 40, "v4": "1.8"}`. Meaning that when triggered, a GND-voltage pulse with duration of `10ns` is emitted, followed by a +1.8V step with duration of `20ns` and so on.
            vinit: The initial value of the multiplexer. If `"config"` is chosen, the initial value is read from the configuration file. Additionally, the user can choose between `"VI1"` or `"VI2"`.
        """
        if self.config["hardware_version"][0] < 2:
            raise Exception("Multiplexing not implemented in hardware version 1.")

        # state machine that emits the glitch if the trigger condition is met (part 1)
        self.sm0.active(0)
        if vinit == "config":
            self.sm0.init(Statemachines.multiplex, freq=self.frequency, set_base=self.pin_glitch, out_base=self.pin_glitch, sideset_base=self.pin_glitch_en)
        elif vinit == "VI1":
            self.sm0.init(Statemachines.multiplex_vin1, freq=self.frequency, set_base=self.pin_glitch, out_base=self.pin_glitch, sideset_base=self.pin_glitch_en)
        elif vinit == "VI2":
            self.sm0.init(Statemachines.multiplex_vin2, freq=self.frequency, set_base=self.pin_glitch, out_base=self.pin_glitch, sideset_base=self.pin_glitch_en)
        # push multiplexing shape config into the fifo of the statemachine
        self.sm0.put(int(delay) // (1_000_000_000 // self.frequency))
        try:
            t1 = int(mul_config["t1"]) // (1_000_000_000 // self.frequency)
            v1 = self.voltage_map[mul_config["v1"]]
        except Exception as _:
            t1 = 0
            v1 = Globals.MUX_PIO_INIT
        try:
            t2 = int(mul_config["t2"]) // (1_000_000_000 // self.frequency)
            v2 = self.voltage_map[mul_config["v2"]]
        except Exception as _:
            t2 = 0
            v2 = Globals.MUX_PIO_INIT
        config = t2 << 18 | v2 << 16 | t1 << 2 | v1
        self.sm0.put(config)
        # push the next multiplexing shape config into the fifo of the statemachine
        try:
            t3 = int(mul_config["t3"]) // (1_000_000_000 // self.frequency)
            v3 = self.voltage_map[mul_config["v3"]]
        except Exception as _:
            t3 = 0
            v3 = Globals.MUX_PIO_INIT
        try:
            t4 = int(mul_config["t4"]) // (1_000_000_000 // self.frequency)
            v4 = self.voltage_map[mul_config["v4"]]
        except Exception as _:
            t4 = 0
            v4 = Globals.MUX_PIO_INIT
        config = t4 << 18 | v4 << 16 | t3 << 2 | v3
        self.sm0.put(config)

        self.__arm_common()

    def arm_multiplexing_test(self, delay:int, mul_config:dict, vinit:str = "config"):
        # state machine that emits the glitch if the trigger condition is met (part 1)
        self.sm0.active(0)
        self.sm0.init(Statemachines.multiplex_vin2, freq=self.frequency, set_base=self.pin_glitch, out_base=self.pin_glitch, sideset_base=self.pin_glitch_en)
        # push multiplexing shape config into the fifo of the statemachine
        self.sm0.put(int(delay) // (1_000_000_000 // self.frequency))
        # 0b00: VI1
        # 0b10: VI2
        # 0b01: +1V8
        # 0b11: GND
        t1 = 5
        v1 = 0b11
        t2 = 40
        v2 = 0b10
        config = t2 << 18 | v2 << 16 | t1 << 2 | v1
        self.sm0.put(config)
        t3 = 0
        v3 = 0b10
        t4 = 0
        v4 = 0b10
        config = t4 << 18 | v4 << 16 | t3 << 2 | v3
        self.sm0.put(config)
        self.__arm_common()

    def arm_pulseshaping_from_config(self, delay:int, ps_config:list[list[float]]):
        """
        Arm the Pico Glitcher and wait for the trigger condition. The pulse is defined via a configuration similar to multiplexing (without interpolation):

        Parameters:
            delay: Glitch is emitted after this time. Given in nano seconds. Expect a resolution of about 5 nano seconds.
            ps_config: The pulse configuration given as a list of time deltas and voltage values.
        """
        pulse = self.pulse_generator.pulse_from_config(ps_config)
        self.__arm_pulseshaping(delay, pulse)

    def arm_pulseshaping_from_spline(self, delay:int, xpoints:list[int], ypoints:list[float]):
        """
        Arm the Pico Glitcher and wait for the trigger condition. The pulse definition is given by time and voltage points. Intermediate values are interpolated.

        Parameters:
            delay: Glitch is emitted after this time. Given in nano seconds. Expect a resolution of about 5 nano seconds.
            xpoints: A list of time points (in nanoseconds) where voltage changes occur.
            ypoints: The corresponding voltage levels at each time point.
        """
        pulse = self.pulse_generator.pulse_from_spline(xpoints, ypoints)
        self.__arm_pulseshaping(delay, pulse)

    def arm_pulseshaping_from_lambda(self, delay:int, ps_lambda, pulse_number_of_points:int):
        """
        Arm the Pico Glitcher and wait for the trigger condition. Generate the pulse from a lambda function depending on the time.

        Parameters:
            delay: Glitch is emitted after this time. Given in nano seconds. Expect a resolution of about 5 nano seconds.
            ps_lambda: A lambda function that defines the glitch at certain times. Must be given as string which is processed by the Pico Glitcher at runtime.
            pulse_number_of_points: The approximate length of the pulse. This is needed to constrain the pulse and to save computing time.
        """
        pulse = self.pulse_generator.pulse_from_lambda(ps_lambda, pulse_number_of_points)
        self.__arm_pulseshaping(delay, pulse)

    def arm_pulseshaping_from_list(self, delay:int, pulse:list[int]):
        """
        Arm the Pico Glitcher and wait for the trigger condition. Genereate the pulse from a raw array of values.

        Parameters:
            delay: Glitch is emitted after this time. Given in nano seconds. Expect a resolution of about 5 nano seconds.
            pulse: A raw list of points that define the pulse. No calibration and no constraints are applied to the list. The list is forwarded directly to the DAC.
        """
        pulse = self.pulse_generator.pulse_from_list(pulse)
        self.__arm_pulseshaping(delay, pulse)

    def __arm_pulseshaping(self, delay:int, pulse:list[int]):
        if self.config["hardware_version"][0] < 2:
            raise Exception("Multiplexing not implemented in hardware version 1.")

        # load the pulse into AD9102 SRAM
        self.ad910x.write_sram_from_start(pulse)
        self.ad910x.update_sram(len(pulse))

        # state machine that pulls the ps_trigger pin to low if the trigger condition is met
        self.sm0.active(0)
        self.sm0.init(Statemachines.pulse_shaping, freq=self.frequency, set_base=self.pin_glitch, out_base=self.pin_glitch, sideset_base=self.pin_glitch_en)
        # push delay (in nano seconds) into the fifo of the statemachine
        self.sm0.put(int(delay) // (1_000_000_000 // self.frequency))
        maxlength = 10_000 # TODO: control this by an argument or the pulse length
        self.sm0.put(maxlength // (1_000_000_000 // self.frequency))

        self.__arm_common()
        #print(pulse)

    def block(self, timeout:float):
        """
        Block until trigger condition is met. Raises an exception if times out.
        
        Parameters:
            timeout: Time after the block is released.
        """
        if self.sm0 is not None:
            timeout_ms = int(timeout * 1_000)
            start_time = time.ticks_ms()
            while time.ticks_diff(time.ticks_ms(), start_time) < timeout_ms:
                if self.sm0.rx_fifo() > 0:
                    self.armed = False
                    break
            if time.ticks_diff(time.ticks_ms(), start_time) >= timeout_ms:
                self.sm0.active(0)
                self.pin_glitch_en.low()
                self.adc_samples_captured = True
                self.armed = False
                raise Exception("Function execution timed out!")

    def check_glitch(self) -> bool:
        """
        Check if the glitch was emitted.

        Returns:
            Returns True if statemachine 0, that is used for glitch generation, was triggered.
        """
        if self.sm0 is not None:
            check = self.sm0.rx_fifo() > 0
            print(check)
            return check

    def get_sm1_output(self):
        if self.sm1 is not None:
            res = self.sm1.get()
            print(res)

    def __change_config(self, key:str, value:int|float|str):
        """
        Change the content of the configuration file `config.json`. Note that the value to be changed must already exist.

        Parameters:
            key: Key of value to be replaced.
            value: Value to be set.
        """
        with open("config.json", "r") as file:
            config = ujson.load(file)

        # change value
        config[key] = value
        # dump config to file
        with open("config.json", "w") as file:
            ujson.dump(config, file)

        # read back
        with open("config.json", "r") as file:
            config = ujson.load(file)
        print(config)

    def change_config_and_apply(self, key:str, value:int|float|str):
        """
        Change the content of the configuration file `config.json`. Note that the value to be changed must already exist. Apply the values afterwards.

        Parameters:
            key: Key of value to be replaced.
            value: Value to be set.
        """
        self.__change_config(key, value)
        with open("config.json", "r") as file:
            self.config = ujson.load(file)
        # reload the global variables and Statemachines
        del sys.modules['Globals']
        import Globals

    def change_config_and_reset(self, key:str, value:int|float|str):
        """
        Change the content of the configuration file `config.json`. Note that the value to be changed must already exist. Reset the Pico Glitcher.

        Parameters:
            key: Key of value to be replaced.
            value: Value to be set.
        """
        self.__change_config(key, value)
        machine.soft_reset()
        #machine.reset()

    def hard_reset(self):
        """
        Perform a hard reset of the Pico Glitcher (Raspberry Pi Pico).
        """
        machine.reset()

    @micropython.native
    def __poll_fast_adc(self, sm):
        # this code runs with ~2us per sample -> 450 ksps
        self.fastsamples = self.fastadc.read()
        self.adc_samples_captured = True

    def arm_adc(self):
        """
        Arm the ADC on pin 26 and capture ADC samples if the trigger condition is met. On Pico Glitcher hardware version 1, the separate SMA connector labeled `Analog` can be used to measure analog voltage traces. On revision 2, the analog input is directly connected to the `GLITCH` line.
        """
        self.adc_samples_captured = False
        self.sm0.irq(handler=self.__poll_fast_adc)

    def get_adc_samples(self, timeout:float = 1.0):
        """
        Read back the captured ADC samples.
        """
        timeout_ms = int(timeout * 1_000)
        start_time = time.ticks_ms()
        while time.ticks_diff(time.ticks_ms(), start_time) < timeout_ms:
            if self.adc_samples_captured:
                break
        if time.ticks_diff(time.ticks_ms(), start_time) >= timeout_ms:
            raise Exception("ADC timed out!")
        print(self.fastsamples)

    def configure_adc(self, number_of_samples:int = 1024, sampling_freq:int = 500_000):
        """
        Configure the onboard ADC of the Pico Glitcher.

        Parameters:
            number_of_samples: The number of samples to capture after triggering.
            sampling_freq: The sampling frequency of the ADC. `500 kSPS` is the maximum.
        """
        self.fastadc.configure_adc(number_of_samples, sampling_freq)
