MKesenheimer/fault-injection-library/examples/pico-glitcher.py

#!/usr/bin/env python3
# Copyright (C) 2024 Dr. Matthias Kesenheimer - All Rights Reserved.
# You may use, distribute and modify this code under the terms of the GPL3 license.
#
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
# This script can be used to test the pico-glitcher.
# -> Connect Trigger input with Reset.
# -> Between Glitch and VTarget, connect a 10 Ohm resistor (this is the "device under test").
# -> Run the script:
# python pico-glitcher.py --rpico /dev/tty.usbmodem1101 --delay 100 100 --length 100 100
# -> You should now be able to observe the glitches with a oscilloscope on the 10 Ohm resistor.
# -> measure the expected delay and glitch length.

import argparse
import logging
import random
import sys
import time

# import custom libraries
from findus import Database, PicoGlitcher
from findus import AnalogPlot

# inherit functionality and overwrite some functions
class DerivedGlitcher(PicoGlitcher):
    def classify(self, response):
        if b'Trigger ok' in response:
            color = 'G'
        elif b'Error' in response:
            color = 'M'
        elif b'Fatal exception' in response:
            color = 'M'
        elif b'Timeout' in response:
            color = 'Y'
        else:
            color = 'R'
        return color

class Main():
    def __init__(self, args):
        self.args = args

        # logging
        logging.basicConfig(filename="execution.log", filemode="a", format="%(asctime)s %(message)s", level=logging.INFO, force=True)

        # glitcher
        self.glitcher = DerivedGlitcher()
        # if argument args.power is not provided, the internal power-cycling capabilities of the pico-glitcher will be used. In this case, ext_power_voltage is not used.
        self.glitcher.init(port=args.rpico, ext_power=args.power, ext_power_voltage=3.3)
        #self.glitcher.set_cpu_frequency(300_000_000)

        # the initial voltage for multiplexing must be hard-coded and can only be applied
        # if the raspberry pi pico is reset and re-initialized.
        if args.multiplexing:
            self.glitcher.change_config_and_reset("mux_vinit", "VI2")
            self.glitcher.init(port=args.rpico, ext_power=args.power, ext_power_voltage=3.3)

        # choose rising edge trigger with dead time of 0 seconds after power down
        # note that you still have to physically connect the trigger input with vtarget
        self.glitcher.rising_edge_trigger(pin_trigger=args.trigger_input)
        #self.glitcher.rising_edge_trigger(pin_trigger=args.trigger_input, dead_time=0.01, pin_condition="reset")
        #self.glitcher.rising_edge_trigger(pin_trigger=args.trigger_input, dead_time=0.001, pin_condition="6", condition="falling")

        # choose multiplexing, pulse-shaping or crowbar glitching
        if args.multiplexing:
            self.glitcher.set_multiplexing()
        elif args.pulse_shaping:
            self.glitcher.set_pulseshaping(vinit=3.3)
        elif args.lp_glitch:
            self.glitcher.set_lpglitch()
        elif args.hp_glitch:
            self.glitcher.set_hpglitch()
        elif args.ext_glitch is not None:
            self.glitcher.set_ext_mosfet(*args.ext_glitch)
        else:
            self.glitcher.set_lpglitch()

        # set up the database
        self.database = Database(sys.argv, resume=self.args.resume, nostore=self.args.no_store)
        self.start_time = int(time.time())

        # plot the voltage trace while glitching
        if args.use_adc:
            self.number_of_samples = 1024
            self.sampling_freq = 450_000
            self.glitcher.configure_adc(number_of_samples=self.number_of_samples, sampling_freq=self.sampling_freq)
            self.plotter = AnalogPlot(number_of_samples=self.number_of_samples, sampling_freq=self.sampling_freq)

    def run(self):
        # log execution
        logging.info(" ".join(sys.argv))

        s_length = self.args.length[0]
        e_length = self.args.length[1]
        s_delay = self.args.delay[0]
        e_delay = self.args.delay[1]

        experiment_id = 0
        while True:
            # set up glitch parameters (in nano seconds) and arm glitcher
            # trunk-ignore(bandit/B311)
            delay = random.randint(s_delay, e_delay)
            # trunk-ignore(bandit/B311)
            length = random.randint(s_length, e_length)

            # power-cycle the target: If power-cycling is done via the multiplexing or pulse-shaping
            # stage this must be done before arming the Pico Glitcher, since this would disable
            # the statemachine for glitch generation.
            #self.glitcher.power_cycle_target(0.05)
            #time.sleep(0.1)

            # arm
            if args.multiplexing:
                mul_config = {"t1": length, "v1": "1.8", "t2": length, "v2": "VI1", "t3": length, "v3": "VI2",  "t4": length, "v4": "GND"}
                self.glitcher.arm_multiplexing(delay, mul_config)
                #self.glitcher.arm_multiplexing(delay, {"t1": 1, "v1": "GND", "t2": 200, "v2": "3.3"})
            elif args.pulse_shaping:
                # pulse from lambda; ramp down to 1.8V than GND glitch
                ps_lambda = f"lambda t:-1.5/({2*length})*t+3.3 if t<{2*length} else 1.8 if t<{4*length} else 0.0 if t<{5*length} else 3.3"
                self.glitcher.arm_pulseshaping_from_lambda(delay, ps_lambda, 6*length)
            else:
                # burst
                #self.glitcher.arm(delay, length, 10, 1000)
                # one shot
                self.glitcher.arm(delay, length)

            if args.use_adc:
                self.glitcher.arm_adc()

            # reset target
            time.sleep(0.01)
            self.glitcher.reset_target(0.01)
            #self.glitcher.power_cycle_reset(0.01)

            # reset target via gpio
            # see issue #21: if this is used to generate the trigger, the ADC times out
            #self.glitcher.set_gpio(5, 0)
            #time.sleep(0.01)
            #self.glitcher.set_gpio(5, 1)

            # block until glitch
            try:
                self.glitcher.block(timeout=1)
                # Manually set the response to a reasonable value.
                # In a real scenario, this would be filled by the response of the microcontroller (UART, SWD, etc.)
                response = b'Trigger ok'
                if args.use_adc:
                    samples = self.glitcher.get_adc_samples()
                    self.plotter.update_curve(samples)
            except Exception as e:
                print(e)
                print("[-] Timeout received in block(). Continuing.")
                self.glitcher.power_cycle_target(power_cycle_time=1)
                time.sleep(0.2)
                response = b'Timeout'

            # check if glitch was emitted
            #print(self.glitcher.check_glitch())

            # classify response
            color = self.glitcher.classify(response)

            # add to database
            self.database.insert(experiment_id, delay, length, color, response)

            # monitor
            speed = self.glitcher.get_speed(self.start_time, experiment_id)
            experiment_base_id = self.database.get_base_experiments_count()
            print(self.glitcher.colorize(f"[+] Experiment {experiment_id}\t{experiment_base_id}\t({speed})\t{length}\t{delay}\t{color}\t{response}", color))

            # increase experiment id
            experiment_id += 1

if __name__ == "__main__":
    parser = argparse.ArgumentParser()
    parser.add_argument("--rpico", required=False, help="rpico port", default="/dev/ttyACM0")
    parser.add_argument("--power", required=False, help="rk6006 port", default=None)
    parser.add_argument("--delay", required=True, nargs=2, help="delay start and end", type=int)
    parser.add_argument("--length", required=True, nargs=2, help="length start and end", type=int)
    parser.add_argument("--resume", required=False, action='store_true', help="if an previous dataset should be resumed")
    parser.add_argument("--no-store", required=False, action='store_true', help="do not store the run in the database")
    parser.add_argument("--multiplexing", required=False, action='store_true', help="Instead of crowbar glitching, perform a fault injection with multiplexing between different voltages (requires PicoGlitcher v2).")
    parser.add_argument("--pulse-shaping", required=False, action='store_true', help="Instead of crowbar glitching, perform a fault injection with a predefined voltage profile (requires PicoGlitcher v2).")
    parser.add_argument("--trigger-input", required=False, default="default", help="The trigger input to use (default, alt, ext1, ext2). The inputs ext1 and ext2 require the PicoGlitcher v2.")
    parser.add_argument("--use-adc", required=False, action='store_true', help="Use the onboard ADC of the Pico Glitcher to show the voltage curve during glitching.")
    parser.add_argument("--lp-glitch", required=False, action='store_true', help="Use the low power MOSFET for glitch generation.")
    parser.add_argument("--hp-glitch", required=False, action='store_true', help="Use the high power MOSFET for glitch generation.")
    parser.add_argument("--ext-glitch", required=False, nargs='*', help="Use GPIO pin 19 to output the glitch. Other GPIO pins could also be chosen, for example 16, 17 or 18.", type=int, default=None)

    args = parser.parse_args()

    main = Main(args)

    try:
        main.run()
    except KeyboardInterrupt:
        print("\nExitting...")
        sys.exit(1)
